fractalclockwork/core-memory-redux/kicad/_preview/pcb_ccs_sense-1.png

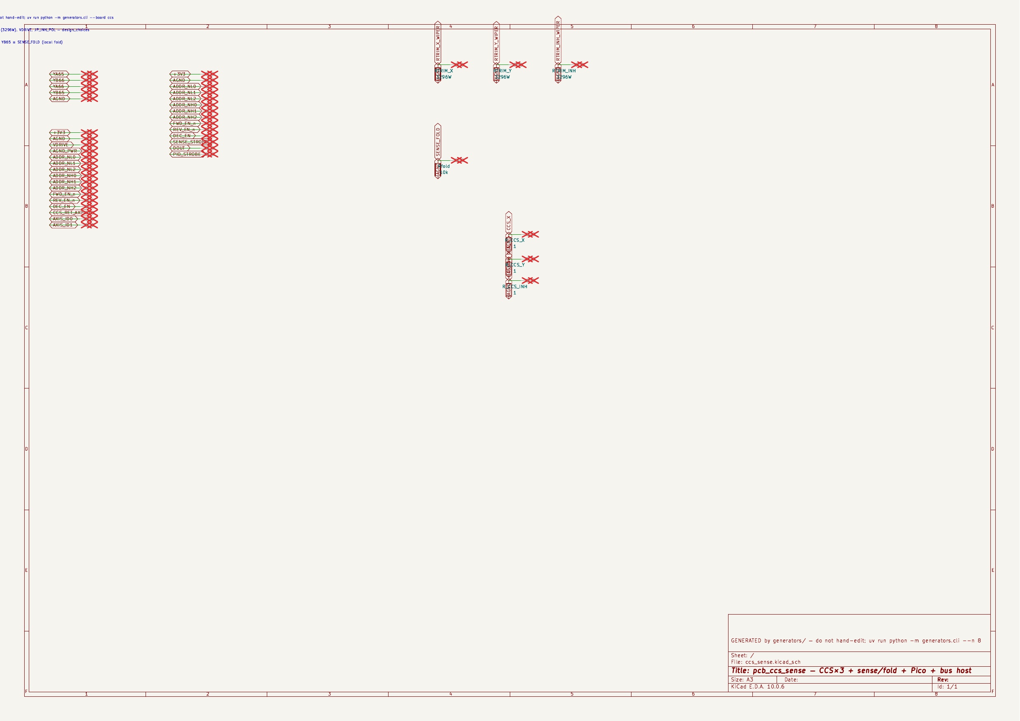
kicad/_preview/pcb_ccs_sense-1.png
