fractalclockwork/core-memory-redux/kicad/bringup_2x2/ccs_channel.kicad_sch

## KiCad design kicad/bringup_2x2/ccs_channel.kicad_sch (2026-10-05)

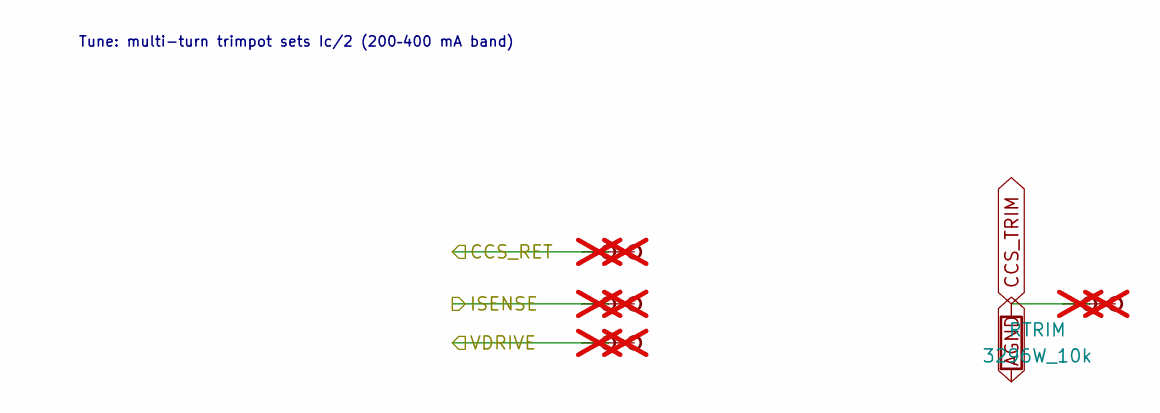
[picture p16: schematic ccs_channel.kicad_sch]

Parts:
RTRIM: 3296W_10k
TP_CCS_RET: Stub; not fitted
TP_CCS_RETb: Stub; not fitted
TP_CCS_TRIM_80_01_35_, TP_CCS_TRIM_80_01_35_b: Stub; not fitted
TP_ISENSE: Stub; not fitted
TP_ISENSEb: Stub; not fitted
TP_VDRIVE: Stub; not fitted
TP_VDRIVEb: Stub; not fitted

Connections:
AGND: RTRIM.2
CCS_RET: TP_CCS_RET.1, TP_CCS_RETb.1
CCS_TRIM: RTRIM.1, TP_CCS_TRIM_80_01_35_.1, TP_CCS_TRIM_80_01_35_b.1
ISENSE: TP_ISENSE.1, TP_ISENSEb.1
VDRIVE: TP_VDRIVE.1, TP_VDRIVEb.1

Notes on the sheet:
Tune: multi-turn trimpot sets Ic/2 (200–400 mA band)
