fractalclockwork/core-memory-redux/kicad/bringup_2x2/decode_block.kicad_sch

## KiCad design kicad/bringup_2x2/decode_block.kicad_sch (2026-10-05)

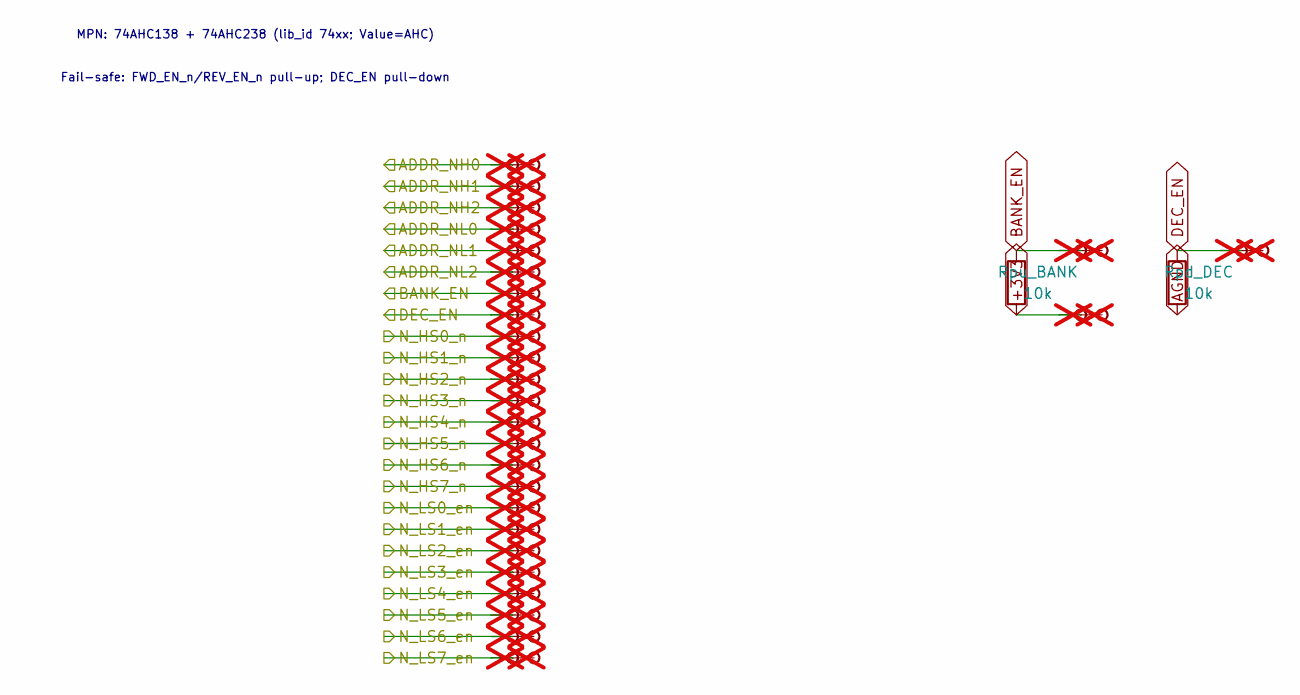
[picture p17: schematic decode_block.kicad_sch]

Parts:
Rpd_DEC: 10k
Rpu_BANK: 10k
TP_ADDR_NH0, TP_ADDR_NH0b, TP_ADDR_NH1, TP_ADDR_NH1b, TP_ADDR_NH2, TP_ADDR_NH2b: Stub; not fitted
TP_ADDR_NL0, TP_ADDR_NL0b, TP_ADDR_NL1, TP_ADDR_NL1b, TP_ADDR_NL2, TP_ADDR_NL2b: Stub; not fitted
TP_BANK_EN: Stub; not fitted
TP_BANK_EN_100_33_35_, TP_BANK_EN_100_33_35_b: Stub; not fitted
TP_BANK_ENb: Stub; not fitted
TP_DEC_EN: Stub; not fitted
TP_DEC_EN_119_38_35_5, TP_DEC_EN_119_38_35_5b: Stub; not fitted
TP_DEC_ENb: Stub; not fitted
TP_N_HS0_n, TP_N_HS0_nb, TP_N_HS1_n, TP_N_HS1_nb, TP_N_HS2_n, TP_N_HS2_nb, TP_N_HS3_n, TP_N_HS3_nb, TP_N_HS4_n, TP_N_HS4_nb, TP_N_HS5_n, TP_N_HS5_nb, TP_N_HS6_n, TP_N_HS6_nb, TP_N_HS7_n, TP_N_HS7_nb: Stub; not fitted
TP_N_LS0_en, TP_N_LS0_enb, TP_N_LS1_en, TP_N_LS1_enb, TP_N_LS2_en, TP_N_LS2_enb, TP_N_LS3_en, TP_N_LS3_enb, TP_N_LS4_en, TP_N_LS4_enb, TP_N_LS5_en, TP_N_LS5_enb, TP_N_LS6_en, TP_N_LS6_enb, TP_N_LS7_en, TP_N_LS7_enb: Stub; not fitted
TP__3V3_100_33_43_18, TP__3V3_100_33_43_18b: Stub; not fitted

Connections:
+3V3: Rpu_BANK.2, TP__3V3_100_33_43_18.1, TP__3V3_100_33_43_18b.1
ADDR_NH0: TP_ADDR_NH0.1, TP_ADDR_NH0b.1
ADDR_NH1: TP_ADDR_NH1.1, TP_ADDR_NH1b.1
ADDR_NH2: TP_ADDR_NH2.1, TP_ADDR_NH2b.1
ADDR_NL0: TP_ADDR_NL0.1, TP_ADDR_NL0b.1
ADDR_NL1: TP_ADDR_NL1.1, TP_ADDR_NL1b.1
ADDR_NL2: TP_ADDR_NL2.1, TP_ADDR_NL2b.1
AGND: Rpd_DEC.2
BANK_EN: Rpu_BANK.1, TP_BANK_EN.1, TP_BANK_EN_100_33_35_.1, TP_BANK_EN_100_33_35_b.1, TP_BANK_ENb.1
DEC_EN: Rpd_DEC.1, TP_DEC_EN.1, TP_DEC_EN_119_38_35_5.1, TP_DEC_EN_119_38_35_5b.1, TP_DEC_ENb.1
N_HS0_n: TP_N_HS0_n.1, TP_N_HS0_nb.1
N_HS1_n: TP_N_HS1_n.1, TP_N_HS1_nb.1
N_HS2_n: TP_N_HS2_n.1, TP_N_HS2_nb.1
N_HS3_n: TP_N_HS3_n.1, TP_N_HS3_nb.1
N_HS4_n: TP_N_HS4_n.1, TP_N_HS4_nb.1
N_HS5_n: TP_N_HS5_n.1, TP_N_HS5_nb.1
N_HS6_n: TP_N_HS6_n.1, TP_N_HS6_nb.1
N_HS7_n: TP_N_HS7_n.1, TP_N_HS7_nb.1
N_LS0_en: TP_N_LS0_en.1, TP_N_LS0_enb.1
N_LS1_en: TP_N_LS1_en.1, TP_N_LS1_enb.1
N_LS2_en: TP_N_LS2_en.1, TP_N_LS2_enb.1
N_LS3_en: TP_N_LS3_en.1, TP_N_LS3_enb.1
N_LS4_en: TP_N_LS4_en.1, TP_N_LS4_enb.1
N_LS5_en: TP_N_LS5_en.1, TP_N_LS5_enb.1
N_LS6_en: TP_N_LS6_en.1, TP_N_LS6_enb.1
N_LS7_en: TP_N_LS7_en.1, TP_N_LS7_enb.1

Notes on the sheet:
MPN: 74AHC138 + 74AHC238 (lib_id 74xx; Value=AHC)
Fail-safe: FWD_EN_n/REV_EN_n pull-up; DEC_EN pull-down
