fractalclockwork/core-memory-redux/kicad/bringup_2x2/dmos_hs_array.kicad_sch

## KiCad design kicad/bringup_2x2/dmos_hs_array.kicad_sch (2026-10-05)

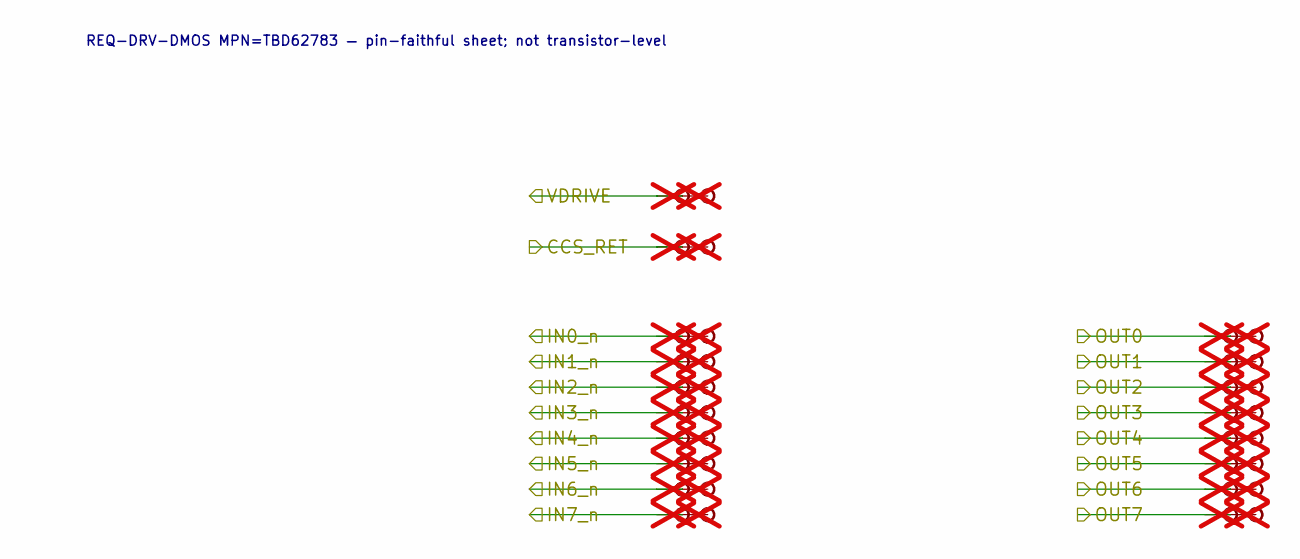
[picture p18: schematic dmos_hs_array.kicad_sch]

Parts:
TP_CCS_RET: Stub; not fitted
TP_CCS_RETb: Stub; not fitted
TP_IN0_n, TP_IN0_nb, TP_IN1_n, TP_IN1_nb, TP_IN2_n, TP_IN2_nb, TP_IN3_n, TP_IN3_nb, TP_IN4_n, TP_IN4_nb, TP_IN5_n, TP_IN5_nb, TP_IN6_n, TP_IN6_nb, TP_IN7_n, TP_IN7_nb: Stub; not fitted
TP_OUT0, TP_OUT0b, TP_OUT1, TP_OUT1b, TP_OUT2, TP_OUT2b, TP_OUT3, TP_OUT3b, TP_OUT4, TP_OUT4b, TP_OUT5, TP_OUT5b, TP_OUT6, TP_OUT6b, TP_OUT7, TP_OUT7b: Stub; not fitted
TP_VDRIVE: Stub; not fitted
TP_VDRIVEb: Stub; not fitted

Connections:
CCS_RET: TP_CCS_RET.1, TP_CCS_RETb.1
IN0_n: TP_IN0_n.1, TP_IN0_nb.1
IN1_n: TP_IN1_n.1, TP_IN1_nb.1
IN2_n: TP_IN2_n.1, TP_IN2_nb.1
IN3_n: TP_IN3_n.1, TP_IN3_nb.1
IN4_n: TP_IN4_n.1, TP_IN4_nb.1
IN5_n: TP_IN5_n.1, TP_IN5_nb.1
IN6_n: TP_IN6_n.1, TP_IN6_nb.1
IN7_n: TP_IN7_n.1, TP_IN7_nb.1
OUT0: TP_OUT0.1, TP_OUT0b.1
OUT1: TP_OUT1.1, TP_OUT1b.1
OUT2: TP_OUT2.1, TP_OUT2b.1
OUT3: TP_OUT3.1, TP_OUT3b.1
OUT4: TP_OUT4.1, TP_OUT4b.1
OUT5: TP_OUT5.1, TP_OUT5b.1
OUT6: TP_OUT6.1, TP_OUT6b.1
OUT7: TP_OUT7.1, TP_OUT7b.1
VDRIVE: TP_VDRIVE.1, TP_VDRIVEb.1

Notes on the sheet:
REQ-DRV-DMOS MPN=TBD62783 — pin-faithful sheet; not transistor-level
