fractalclockwork/core-memory-redux/kicad/bringup_2x2/dmos_ls_array.kicad_sch

## KiCad design kicad/bringup_2x2/dmos_ls_array.kicad_sch (2026-10-05)

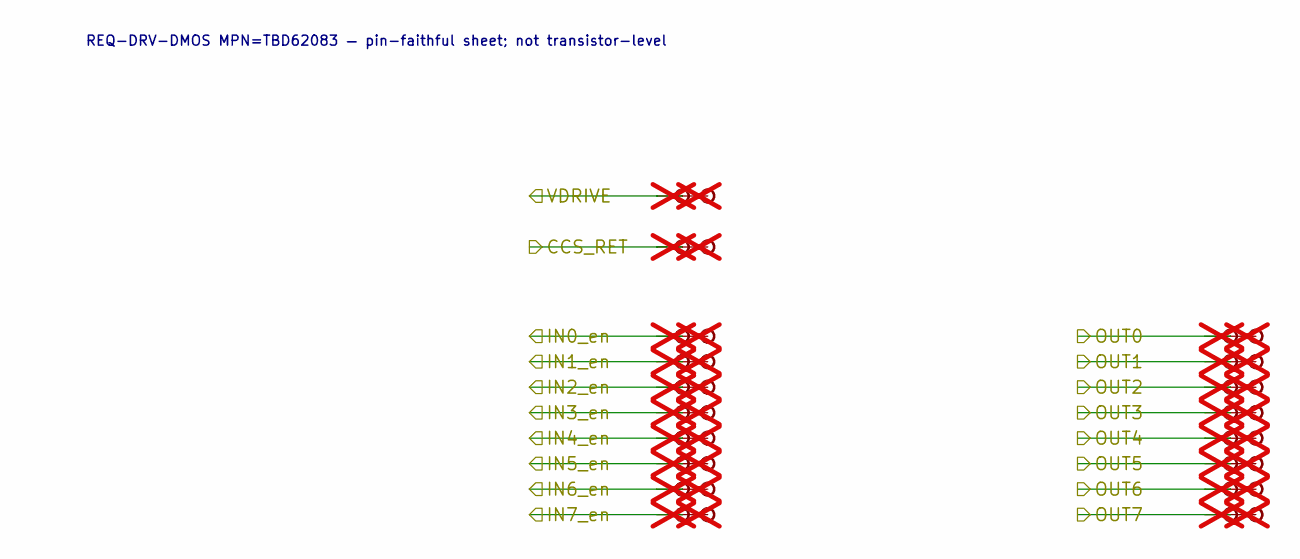
[picture p19: schematic dmos_ls_array.kicad_sch]

Parts:
TP_CCS_RET: Stub; not fitted
TP_CCS_RETb: Stub; not fitted
TP_IN0_en, TP_IN0_enb, TP_IN1_en, TP_IN1_enb, TP_IN2_en, TP_IN2_enb, TP_IN3_en, TP_IN3_enb, TP_IN4_en, TP_IN4_enb, TP_IN5_en, TP_IN5_enb, TP_IN6_en, TP_IN6_enb, TP_IN7_en, TP_IN7_enb: Stub; not fitted
TP_OUT0, TP_OUT0b, TP_OUT1, TP_OUT1b, TP_OUT2, TP_OUT2b, TP_OUT3, TP_OUT3b, TP_OUT4, TP_OUT4b, TP_OUT5, TP_OUT5b, TP_OUT6, TP_OUT6b, TP_OUT7, TP_OUT7b: Stub; not fitted
TP_VDRIVE: Stub; not fitted
TP_VDRIVEb: Stub; not fitted

Connections:
CCS_RET: TP_CCS_RET.1, TP_CCS_RETb.1
IN0_en: TP_IN0_en.1, TP_IN0_enb.1
IN1_en: TP_IN1_en.1, TP_IN1_enb.1
IN2_en: TP_IN2_en.1, TP_IN2_enb.1
IN3_en: TP_IN3_en.1, TP_IN3_enb.1
IN4_en: TP_IN4_en.1, TP_IN4_enb.1
IN5_en: TP_IN5_en.1, TP_IN5_enb.1
IN6_en: TP_IN6_en.1, TP_IN6_enb.1
IN7_en: TP_IN7_en.1, TP_IN7_enb.1
OUT0: TP_OUT0.1, TP_OUT0b.1
OUT1: TP_OUT1.1, TP_OUT1b.1
OUT2: TP_OUT2.1, TP_OUT2b.1
OUT3: TP_OUT3.1, TP_OUT3b.1
OUT4: TP_OUT4.1, TP_OUT4b.1
OUT5: TP_OUT5.1, TP_OUT5b.1
OUT6: TP_OUT6.1, TP_OUT6b.1
OUT7: TP_OUT7.1, TP_OUT7b.1
VDRIVE: TP_VDRIVE.1, TP_VDRIVEb.1

Notes on the sheet:
REQ-DRV-DMOS MPN=TBD62083 — pin-faithful sheet; not transistor-level
