fractalclockwork/core-memory-redux/kicad/bringup_2x2/driver.kicad_sch

## KiCad design kicad/bringup_2x2/driver.kicad_sch (2026-10-05)

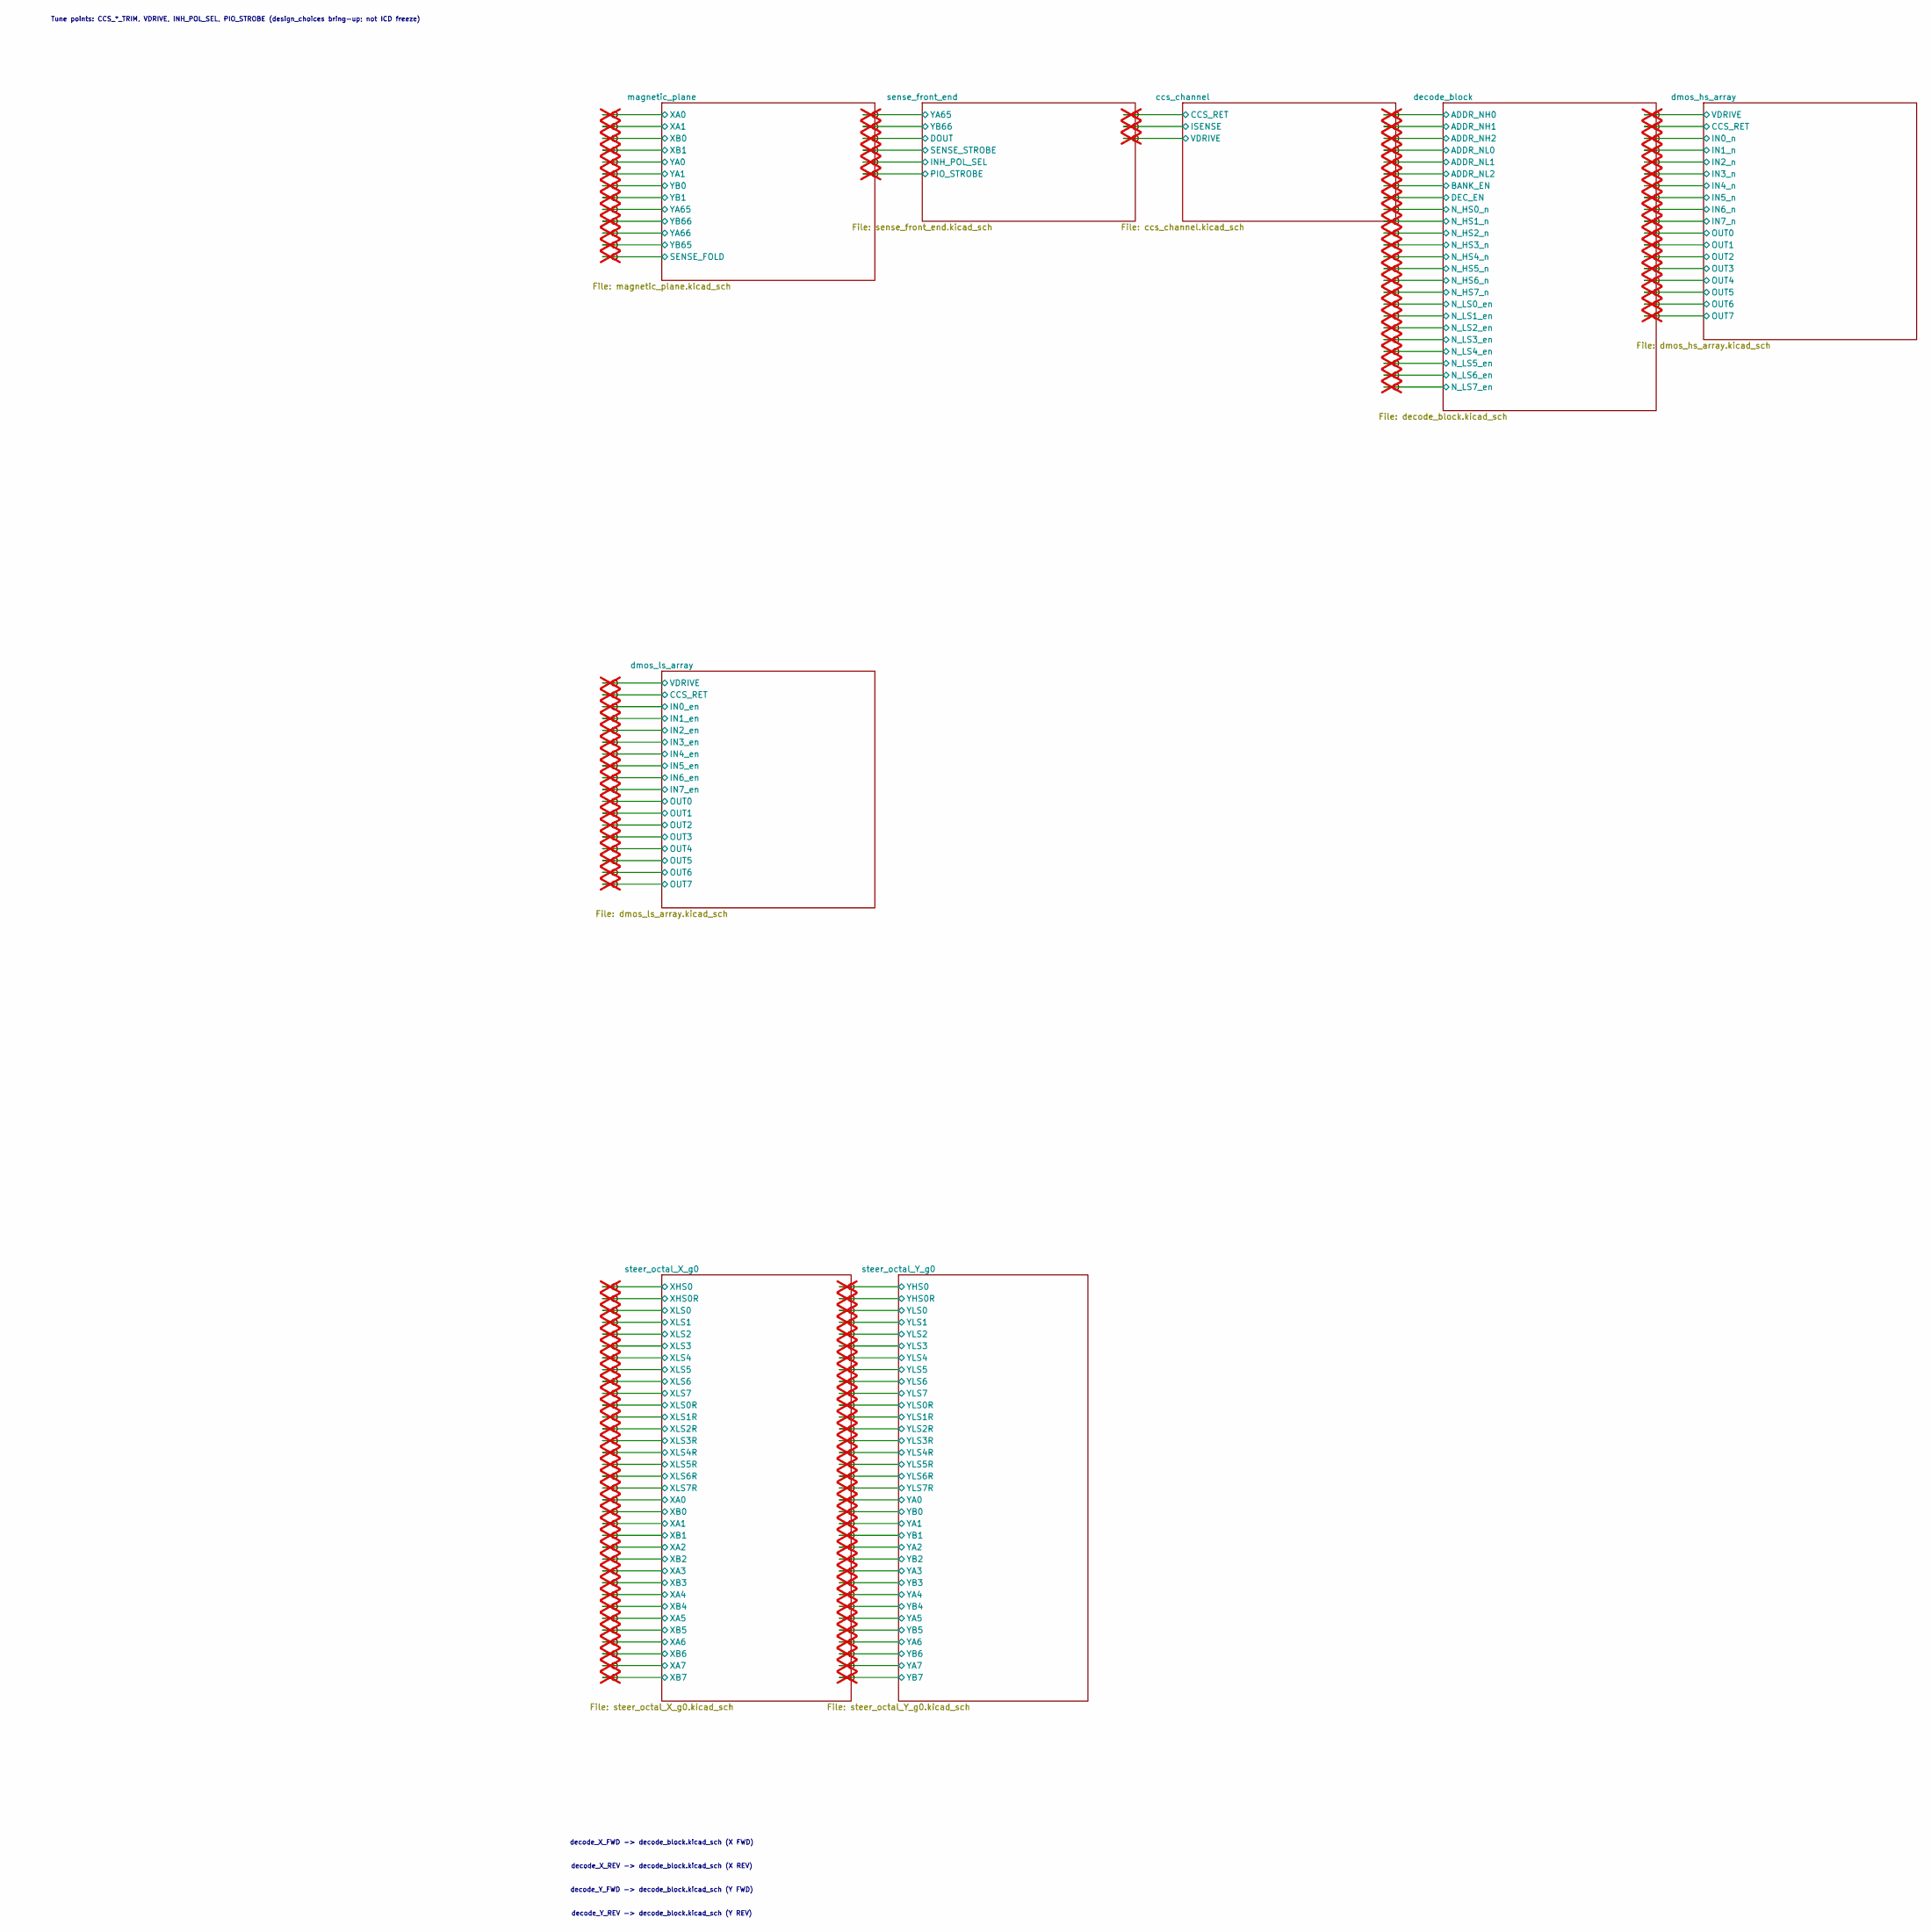
[picture p20: schematic driver.kicad_sch]

Parts:
TP_ccs_channel_CCS_RET: Stub; not fitted
TP_ccs_channel_ISENSE: Stub; not fitted
TP_ccs_channel_VDRIVE: Stub; not fitted
TP_decode_block_ADDR_NH: Stub; not fitted
TP_decode_block_ADDR_NL: Stub; not fitted
TP_decode_block_BANK_EN: Stub; not fitted
TP_decode_block_DEC_EN: Stub; not fitted
TP_decode_block_N_HS0_n, TP_decode_block_N_HS1_n, TP_decode_block_N_HS2_n, TP_decode_block_N_HS3_n, TP_decode_block_N_HS4_n, TP_decode_block_N_HS5_n, TP_decode_block_N_HS6_n, TP_decode_block_N_HS7_n: Stub; not fitted
TP_decode_block_N_LS0_e, TP_decode_block_N_LS1_e, TP_decode_block_N_LS2_e, TP_decode_block_N_LS3_e, TP_decode_block_N_LS4_e, TP_decode_block_N_LS5_e, TP_decode_block_N_LS6_e, TP_decode_block_N_LS7_e: Stub; not fitted
TP_dmos_hs_array_CCS_RE: Stub; not fitted
TP_dmos_hs_array_IN0_n, TP_dmos_hs_array_IN1_n, TP_dmos_hs_array_IN2_n, TP_dmos_hs_array_IN3_n, TP_dmos_hs_array_IN4_n, TP_dmos_hs_array_IN5_n, TP_dmos_hs_array_IN6_n, TP_dmos_hs_array_IN7_n: Stub; not fitted
TP_dmos_hs_array_OUT0, TP_dmos_hs_array_OUT1, TP_dmos_hs_array_OUT2, TP_dmos_hs_array_OUT3, TP_dmos_hs_array_OUT4, TP_dmos_hs_array_OUT5, TP_dmos_hs_array_OUT6, TP_dmos_hs_array_OUT7: Stub; not fitted
TP_dmos_hs_array_VDRIVE: Stub; not fitted
TP_dmos_ls_array_CCS_RE: Stub; not fitted
TP_dmos_ls_array_IN0_en, TP_dmos_ls_array_IN1_en, TP_dmos_ls_array_IN2_en, TP_dmos_ls_array_IN3_en, TP_dmos_ls_array_IN4_en, TP_dmos_ls_array_IN5_en, TP_dmos_ls_array_IN6_en, TP_dmos_ls_array_IN7_en: Stub; not fitted
TP_dmos_ls_array_OUT0, TP_dmos_ls_array_OUT1, TP_dmos_ls_array_OUT2, TP_dmos_ls_array_OUT3, TP_dmos_ls_array_OUT4, TP_dmos_ls_array_OUT5, TP_dmos_ls_array_OUT6, TP_dmos_ls_array_OUT7: Stub; not fitted
TP_dmos_ls_array_VDRIVE: Stub; not fitted
TP_magnetic_plane_SENSE: Stub; not fitted
TP_magnetic_plane_XA0, TP_magnetic_plane_XA1: Stub; not fitted
TP_magnetic_plane_XB0, TP_magnetic_plane_XB1: Stub; not fitted
TP_magnetic_plane_YA0, TP_magnetic_plane_YA1, TP_magnetic_plane_YA65, TP_magnetic_plane_YA66: Stub; not fitted
TP_magnetic_plane_YB0, TP_magnetic_plane_YB1, TP_magnetic_plane_YB65, TP_magnetic_plane_YB66: Stub; not fitted
TP_sense_front_end_DOUT: Stub; not fitted
TP_sense_front_end_INH_: Stub; not fitted
TP_sense_front_end_PIO_: Stub; not fitted
TP_sense_front_end_SENS: Stub; not fitted
TP_sense_front_end_YA65: Stub; not fitted
TP_sense_front_end_YB66: Stub; not fitted
TP_steer_octal_X_g0_XA0, TP_steer_octal_X_g0_XA1, TP_steer_octal_X_g0_XA2, TP_steer_octal_X_g0_XA3, TP_steer_octal_X_g0_XA4, TP_steer_octal_X_g0_XA5, TP_steer_octal_X_g0_XA6, TP_steer_octal_X_g0_XA7, TP_steer_octal_X_g0_XB0, TP_steer_octal_X_g0_XB1, TP_steer_octal_X_g0_XB2, TP_steer_octal_X_g0_XB3, TP_steer_octal_X_g0_XB4, TP_steer_octal_X_g0_XB5, TP_steer_octal_X_g0_XB6, TP_steer_octal_X_g0_XB7, TP_steer_octal_X_g0_XHS, TP_steer_octal_X_g0_XLS: Stub; not fitted
TP_steer_octal_Y_g0_YA0, TP_steer_octal_Y_g0_YA1, TP_steer_octal_Y_g0_YA2, TP_steer_octal_Y_g0_YA3, TP_steer_octal_Y_g0_YA4, TP_steer_octal_Y_g0_YA5, TP_steer_octal_Y_g0_YA6, TP_steer_octal_Y_g0_YA7, TP_steer_octal_Y_g0_YB0, TP_steer_octal_Y_g0_YB1, TP_steer_octal_Y_g0_YB2, TP_steer_octal_Y_g0_YB3, TP_steer_octal_Y_g0_YB4, TP_steer_octal_Y_g0_YB5, TP_steer_octal_Y_g0_YB6, TP_steer_octal_Y_g0_YB7, TP_steer_octal_Y_g0_YHS, TP_steer_octal_Y_g0_YLS: Stub; not fitted

Connections:
ADDR_NH0: TP_decode_block_ADDR_NH.1
ADDR_NH1: TP_decode_block_ADDR_NH.1
ADDR_NH2: TP_decode_block_ADDR_NH.1
ADDR_NL0: TP_decode_block_ADDR_NL.1
ADDR_NL1: TP_decode_block_ADDR_NL.1
ADDR_NL2: TP_decode_block_ADDR_NL.1
BANK_EN: TP_decode_block_BANK_EN.1
CCS_RET: TP_ccs_channel_CCS_RET.1, TP_dmos_hs_array_CCS_RE.1, TP_dmos_ls_array_CCS_RE.1
DEC_EN: TP_decode_block_DEC_EN.1
DOUT: TP_sense_front_end_DOUT.1
IN0_en: TP_dmos_ls_array_IN0_en.1
IN0_n: TP_dmos_hs_array_IN0_n.1
IN1_en: TP_dmos_ls_array_IN1_en.1
IN1_n: TP_dmos_hs_array_IN1_n.1
IN2_en: TP_dmos_ls_array_IN2_en.1
IN2_n: TP_dmos_hs_array_IN2_n.1
IN3_en: TP_dmos_ls_array_IN3_en.1
IN3_n: TP_dmos_hs_array_IN3_n.1
IN4_en: TP_dmos_ls_array_IN4_en.1
IN4_n: TP_dmos_hs_array_IN4_n.1
IN5_en: TP_dmos_ls_array_IN5_en.1
IN5_n: TP_dmos_hs_array_IN5_n.1
IN6_en: TP_dmos_ls_array_IN6_en.1
IN6_n: TP_dmos_hs_array_IN6_n.1
IN7_en: TP_dmos_ls_array_IN7_en.1
IN7_n: TP_dmos_hs_array_IN7_n.1
INH_POL_SEL: TP_sense_front_end_INH_.1
ISENSE: TP_ccs_channel_ISENSE.1
N_HS0_n: TP_decode_block_N_HS0_n.1
N_HS1_n: TP_decode_block_N_HS1_n.1
N_HS2_n: TP_decode_block_N_HS2_n.1
N_HS3_n: TP_decode_block_N_HS3_n.1
N_HS4_n: TP_decode_block_N_HS4_n.1
N_HS5_n: TP_decode_block_N_HS5_n.1
N_HS6_n: TP_decode_block_N_HS6_n.1
N_HS7_n: TP_decode_block_N_HS7_n.1
N_LS0_en: TP_decode_block_N_LS0_e.1
N_LS1_en: TP_decode_block_N_LS1_e.1
N_LS2_en: TP_decode_block_N_LS2_e.1
N_LS3_en: TP_decode_block_N_LS3_e.1
N_LS4_en: TP_decode_block_N_LS4_e.1
N_LS5_en: TP_decode_block_N_LS5_e.1
N_LS6_en: TP_decode_block_N_LS6_e.1
N_LS7_en: TP_decode_block_N_LS7_e.1
OUT0: TP_dmos_hs_array_OUT0.1, TP_dmos_ls_array_OUT0.1
OUT1: TP_dmos_hs_array_OUT1.1, TP_dmos_ls_array_OUT1.1
OUT2: TP_dmos_hs_array_OUT2.1, TP_dmos_ls_array_OUT2.1
OUT3: TP_dmos_hs_array_OUT3.1, TP_dmos_ls_array_OUT3.1
OUT4: TP_dmos_hs_array_OUT4.1, TP_dmos_ls_array_OUT4.1
OUT5: TP_dmos_hs_array_OUT5.1, TP_dmos_ls_array_OUT5.1
OUT6: TP_dmos_hs_array_OUT6.1, TP_dmos_ls_array_OUT6.1
OUT7: TP_dmos_hs_array_OUT7.1, TP_dmos_ls_array_OUT7.1
PIO_STROBE: TP_sense_front_end_PIO_.1
SENSE_FOLD: TP_magnetic_plane_SENSE.1
SENSE_STROBE: TP_sense_front_end_SENS.1
VDRIVE: TP_ccs_channel_VDRIVE.1, TP_dmos_hs_array_VDRIVE.1, TP_dmos_ls_array_VDRIVE.1
XA0: TP_magnetic_plane_XA0.1, TP_steer_octal_X_g0_XA0.1
XA1: TP_magnetic_plane_XA1.1, TP_steer_octal_X_g0_XA1.1
XA2: TP_steer_octal_X_g0_XA2.1
XA3: TP_steer_octal_X_g0_XA3.1
XA4: TP_steer_octal_X_g0_XA4.1
XA5: TP_steer_octal_X_g0_XA5.1
XA6: TP_steer_octal_X_g0_XA6.1
XA7: TP_steer_octal_X_g0_XA7.1
XB0: TP_magnetic_plane_XB0.1, TP_steer_octal_X_g0_XB0.1
XB1: TP_magnetic_plane_XB1.1, TP_steer_octal_X_g0_XB1.1
XB2: TP_steer_octal_X_g0_XB2.1
XB3: TP_steer_octal_X_g0_XB3.1
XB4: TP_steer_octal_X_g0_XB4.1
XB5: TP_steer_octal_X_g0_XB5.1
XB6: TP_steer_octal_X_g0_XB6.1
XB7: TP_steer_octal_X_g0_XB7.1
XHS0: TP_steer_octal_X_g0_XHS.1
XHS0R: TP_steer_octal_X_g0_XHS.1
XLS0: TP_steer_octal_X_g0_XLS.1
XLS0R: TP_steer_octal_X_g0_XLS.1
XLS1: TP_steer_octal_X_g0_XLS.1
XLS1R: TP_steer_octal_X_g0_XLS.1
XLS2: TP_steer_octal_X_g0_XLS.1
XLS2R: TP_steer_octal_X_g0_XLS.1
XLS3: TP_steer_octal_X_g0_XLS.1
XLS3R: TP_steer_octal_X_g0_XLS.1
XLS4: TP_steer_octal_X_g0_XLS.1
XLS4R: TP_steer_octal_X_g0_XLS.1
XLS5: TP_steer_octal_X_g0_XLS.1
XLS5R: TP_steer_octal_X_g0_XLS.1
XLS6: TP_steer_octal_X_g0_XLS.1
XLS6R: TP_steer_octal_X_g0_XLS.1
XLS7: TP_steer_octal_X_g0_XLS.1
XLS7R: TP_steer_octal_X_g0_XLS.1
YA0: TP_magnetic_plane_YA0.1, TP_steer_octal_Y_g0_YA0.1
YA1: TP_magnetic_plane_YA1.1, TP_steer_octal_Y_g0_YA1.1
YA2: TP_steer_octal_Y_g0_YA2.1
YA3: TP_steer_octal_Y_g0_YA3.1
YA4: TP_steer_octal_Y_g0_YA4.1
YA5: TP_steer_octal_Y_g0_YA5.1
YA6: TP_steer_octal_Y_g0_YA6.1
YA7: TP_steer_octal_Y_g0_YA7.1
YA65: TP_magnetic_plane_YA65.1, TP_sense_front_end_YA65.1
YA66: TP_magnetic_plane_YA66.1
YB0: TP_magnetic_plane_YB0.1, TP_steer_octal_Y_g0_YB0.1
YB1: TP_magnetic_plane_YB1.1, TP_steer_octal_Y_g0_YB1.1
YB2: TP_steer_octal_Y_g0_YB2.1
YB3: TP_steer_octal_Y_g0_YB3.1
YB4: TP_steer_octal_Y_g0_YB4.1
YB5: TP_steer_octal_Y_g0_YB5.1
YB6: TP_steer_octal_Y_g0_YB6.1
YB7: TP_steer_octal_Y_g0_YB7.1
YB65: TP_magnetic_plane_YB65.1
YB66: TP_magnetic_plane_YB66.1, TP_sense_front_end_YB66.1
YHS0: TP_steer_octal_Y_g0_YHS.1
YHS0R: TP_steer_octal_Y_g0_YHS.1
YLS0: TP_steer_octal_Y_g0_YLS.1
YLS0R: TP_steer_octal_Y_g0_YLS.1
YLS1: TP_steer_octal_Y_g0_YLS.1
YLS1R: TP_steer_octal_Y_g0_YLS.1
YLS2: TP_steer_octal_Y_g0_YLS.1
YLS2R: TP_steer_octal_Y_g0_YLS.1
YLS3: TP_steer_octal_Y_g0_YLS.1
YLS3R: TP_steer_octal_Y_g0_YLS.1
YLS4: TP_steer_octal_Y_g0_YLS.1
YLS4R: TP_steer_octal_Y_g0_YLS.1
YLS5: TP_steer_octal_Y_g0_YLS.1
YLS5R: TP_steer_octal_Y_g0_YLS.1
YLS6: TP_steer_octal_Y_g0_YLS.1
YLS6R: TP_steer_octal_Y_g0_YLS.1
YLS7: TP_steer_octal_Y_g0_YLS.1
YLS7R: TP_steer_octal_Y_g0_YLS.1

Notes on the sheet:
decode_X_FWD -> decode_block.kicad_sch (X FWD)
decode_Y_FWD -> decode_block.kicad_sch (Y FWD)
Tune points: CCS_*_TRIM, VDRIVE, INH_POL_SEL, PIO_STROBE (design_choices bring-up; not ICD freeze)
decode_X_REV -> decode_block.kicad_sch (X REV)
decode_Y_REV -> decode_block.kicad_sch (Y REV)
