fractalclockwork/core-memory-redux/kicad/bringup_2x2/magnetic_plane.kicad_sch

## KiCad design kicad/bringup_2x2/magnetic_plane.kicad_sch (2026-10-05)

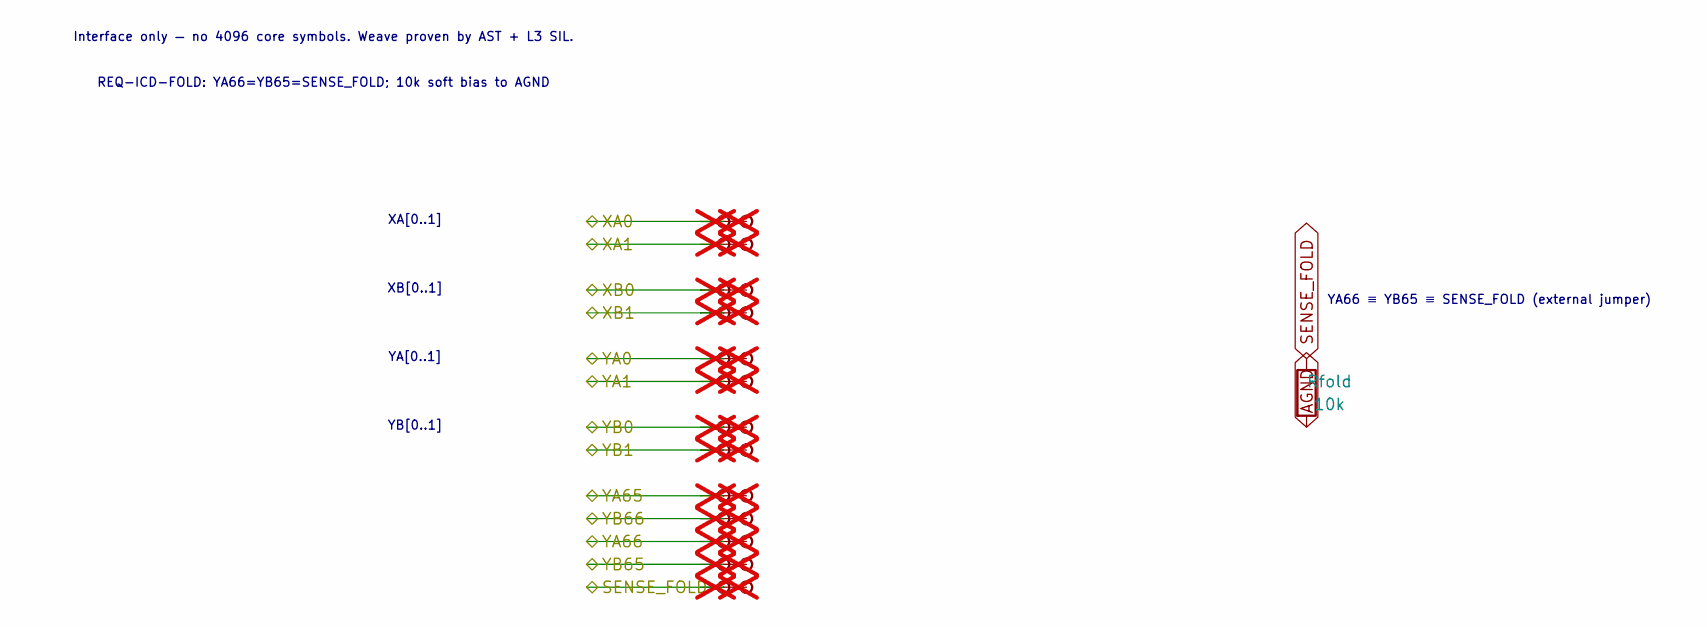
[picture p21: schematic magnetic_plane.kicad_sch]

Parts:
Rfold: 10k
TP_SENSE_FOLD: Stub; not fitted
TP_SENSE_FOLDb: Stub; not fitted
TP_XA0, TP_XA0b, TP_XA1, TP_XA1b: Stub; not fitted
TP_XB0, TP_XB0b, TP_XB1, TP_XB1b: Stub; not fitted
TP_YA0, TP_YA0b, TP_YA1, TP_YA1b, TP_YA65, TP_YA65b, TP_YA66, TP_YA66b: Stub; not fitted
TP_YB0, TP_YB0b, TP_YB1, TP_YB1b, TP_YB65, TP_YB65b, TP_YB66, TP_YB66b: Stub; not fitted

Connections:
AGND: Rfold.2
SENSE_FOLD: Rfold.1, TP_SENSE_FOLD.1, TP_SENSE_FOLDb.1
XA0: TP_XA0.1, TP_XA0b.1
XA1: TP_XA1.1, TP_XA1b.1
XB0: TP_XB0.1, TP_XB0b.1
XB1: TP_XB1.1, TP_XB1b.1
YA0: TP_YA0.1, TP_YA0b.1
YA1: TP_YA1.1, TP_YA1b.1
YA65: TP_YA65.1, TP_YA65b.1
YA66: TP_YA66.1, TP_YA66b.1
YB0: TP_YB0.1, TP_YB0b.1
YB1: TP_YB1.1, TP_YB1b.1
YB65: TP_YB65.1, TP_YB65b.1
YB66: TP_YB66.1, TP_YB66b.1

Notes on the sheet:
Interface only — no 4096 core symbols. Weave proven by AST + L3 SIL.
REQ-ICD-FOLD: YA66=YB65=SENSE_FOLD; 10k soft bias to AGND
XA[0..1]
XB[0..1]
YA[0..1]
YB[0..1]
YA66 ≡ YB65 ≡ SENSE_FOLD (external jumper)
