fractalclockwork/core-memory-redux/kicad/bringup_2x2/sense_front_end.kicad_sch

## KiCad design kicad/bringup_2x2/sense_front_end.kicad_sch (2026-10-05)

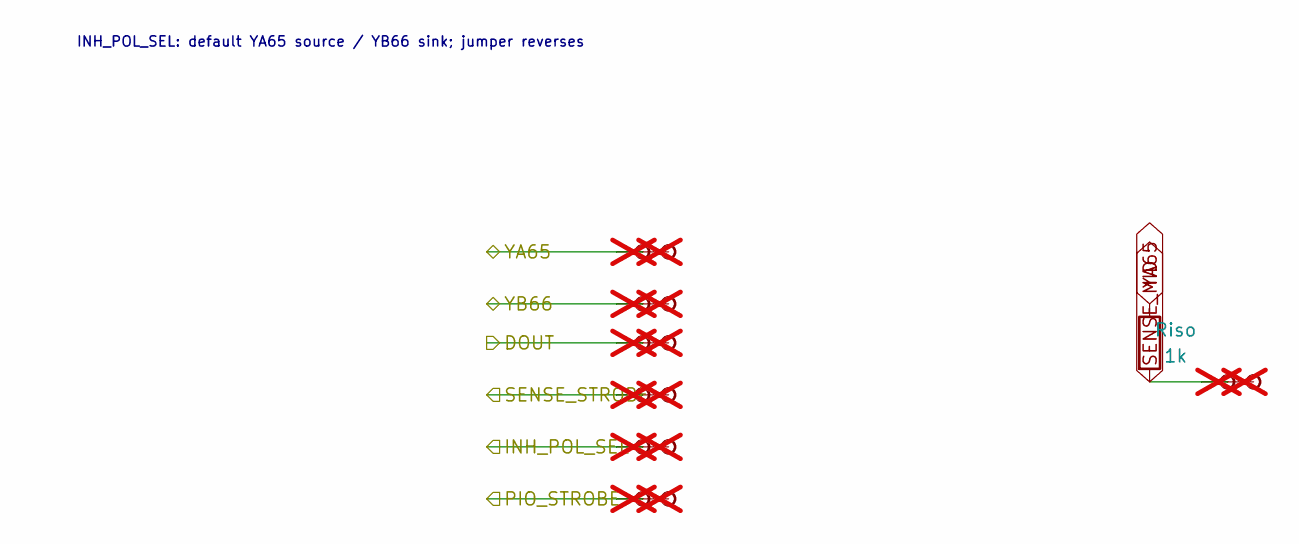
[picture p22: schematic sense_front_end.kicad_sch]

Parts:
Riso: 1k
TP_DOUT: Stub; not fitted
TP_DOUTb: Stub; not fitted
TP_INH_POL_SEL: Stub; not fitted
TP_INH_POL_SELb: Stub; not fitted
TP_PIO_STROBE: Stub; not fitted
TP_PIO_STROBEb: Stub; not fitted
TP_SENSE_MID_90_17_43, TP_SENSE_MID_90_17_43b: Stub; not fitted
TP_SENSE_STROBE: Stub; not fitted
TP_SENSE_STROBEb: Stub; not fitted
TP_YA65, TP_YA65b: Stub; not fitted
TP_YB66, TP_YB66b: Stub; not fitted

Connections:
DOUT: TP_DOUT.1, TP_DOUTb.1
INH_POL_SEL: TP_INH_POL_SEL.1, TP_INH_POL_SELb.1
PIO_STROBE: TP_PIO_STROBE.1, TP_PIO_STROBEb.1
SENSE_MID: Riso.2, TP_SENSE_MID_90_17_43.1, TP_SENSE_MID_90_17_43b.1
SENSE_STROBE: TP_SENSE_STROBE.1, TP_SENSE_STROBEb.1
YA65: Riso.1, TP_YA65.1, TP_YA65b.1
YB66: TP_YB66.1, TP_YB66b.1

Notes on the sheet:
INH_POL_SEL: default YA65 source / YB66 sink; jumper reverses
