fractalclockwork/core-memory-redux/kicad/bringup_2x2/steer_octal_X_g0.kicad_sch

## KiCad design kicad/bringup_2x2/steer_octal_X_g0.kicad_sch (2026-10-05)

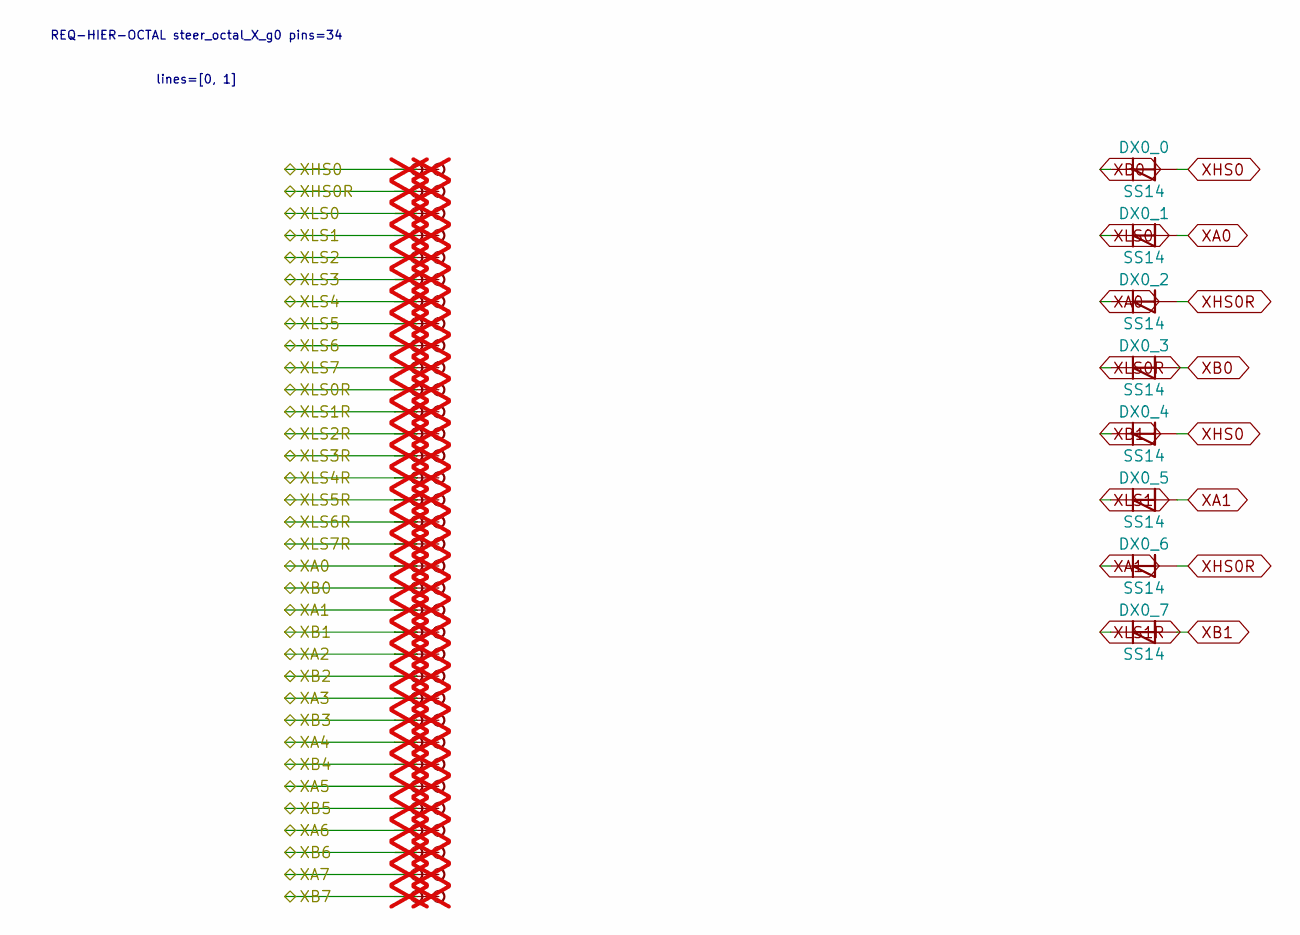
[picture p23: schematic steer_octal_X_g0.kicad_sch]

Parts:
DX0_0, DX0_1, DX0_2, DX0_3, DX0_4, DX0_5, DX0_6, DX0_7: SS14; D_SMA
TP_XA0, TP_XA0b, TP_XA1, TP_XA1b, TP_XA2, TP_XA2b, TP_XA3, TP_XA3b, TP_XA4, TP_XA4b, TP_XA5, TP_XA5b, TP_XA6, TP_XA6b, TP_XA7, TP_XA7b: Stub; not fitted
TP_XB0, TP_XB0b, TP_XB1, TP_XB1b, TP_XB2, TP_XB2b, TP_XB3, TP_XB3b, TP_XB4, TP_XB4b, TP_XB5, TP_XB5b, TP_XB6, TP_XB6b, TP_XB7, TP_XB7b: Stub; not fitted
TP_XHS0, TP_XHS0R, TP_XHS0Rb, TP_XHS0b: Stub; not fitted
TP_XLS0, TP_XLS0R, TP_XLS0Rb, TP_XLS0b, TP_XLS1, TP_XLS1R, TP_XLS1Rb, TP_XLS1b, TP_XLS2, TP_XLS2R, TP_XLS2Rb, TP_XLS2b, TP_XLS3, TP_XLS3R, TP_XLS3Rb, TP_XLS3b, TP_XLS4, TP_XLS4R, TP_XLS4Rb, TP_XLS4b, TP_XLS5, TP_XLS5R, TP_XLS5Rb, TP_XLS5b, TP_XLS6, TP_XLS6R, TP_XLS6Rb, TP_XLS6b, TP_XLS7, TP_XLS7R, TP_XLS7Rb, TP_XLS7b: Stub; not fitted

Connections:
XA0: DX0_1.2 (A), DX0_2.1 (K), TP_XA0.1, TP_XA0b.1
XA1: DX0_5.2 (A), DX0_6.1 (K), TP_XA1.1, TP_XA1b.1
XA2: TP_XA2.1, TP_XA2b.1
XA3: TP_XA3.1, TP_XA3b.1
XA4: TP_XA4.1, TP_XA4b.1
XA5: TP_XA5.1, TP_XA5b.1
XA6: TP_XA6.1, TP_XA6b.1
XA7: TP_XA7.1, TP_XA7b.1
XB0: DX0_0.1 (K), DX0_3.2 (A), TP_XB0.1, TP_XB0b.1
XB1: DX0_4.1 (K), DX0_7.2 (A), TP_XB1.1, TP_XB1b.1
XB2: TP_XB2.1, TP_XB2b.1
XB3: TP_XB3.1, TP_XB3b.1
XB4: TP_XB4.1, TP_XB4b.1
XB5: TP_XB5.1, TP_XB5b.1
XB6: TP_XB6.1, TP_XB6b.1
XB7: TP_XB7.1, TP_XB7b.1
XHS0: DX0_0.2 (A), DX0_4.2 (A), TP_XHS0.1, TP_XHS0b.1
XHS0R: DX0_2.2 (A), DX0_6.2 (A), TP_XHS0R.1, TP_XHS0Rb.1
XLS0: DX0_1.1 (K), TP_XLS0.1, TP_XLS0b.1
XLS0R: DX0_3.1 (K), TP_XLS0R.1, TP_XLS0Rb.1
XLS1: DX0_5.1 (K), TP_XLS1.1, TP_XLS1b.1
XLS1R: DX0_7.1 (K), TP_XLS1R.1, TP_XLS1Rb.1
XLS2: TP_XLS2.1, TP_XLS2b.1
XLS2R: TP_XLS2R.1, TP_XLS2Rb.1
XLS3: TP_XLS3.1, TP_XLS3b.1
XLS3R: TP_XLS3R.1, TP_XLS3Rb.1
XLS4: TP_XLS4.1, TP_XLS4b.1
XLS4R: TP_XLS4R.1, TP_XLS4Rb.1
XLS5: TP_XLS5.1, TP_XLS5b.1
XLS5R: TP_XLS5R.1, TP_XLS5Rb.1
XLS6: TP_XLS6.1, TP_XLS6b.1
XLS6R: TP_XLS6R.1, TP_XLS6Rb.1
XLS7: TP_XLS7.1, TP_XLS7b.1
XLS7R: TP_XLS7R.1, TP_XLS7Rb.1

Notes on the sheet:
REQ-HIER-OCTAL steer_octal_X_g0 pins=34
lines=[0, 1]
