fractalclockwork/core-memory-redux/kicad/bringup_2x2/steer_octal_Y_g0.kicad_sch

## KiCad design kicad/bringup_2x2/steer_octal_Y_g0.kicad_sch (2026-10-05)

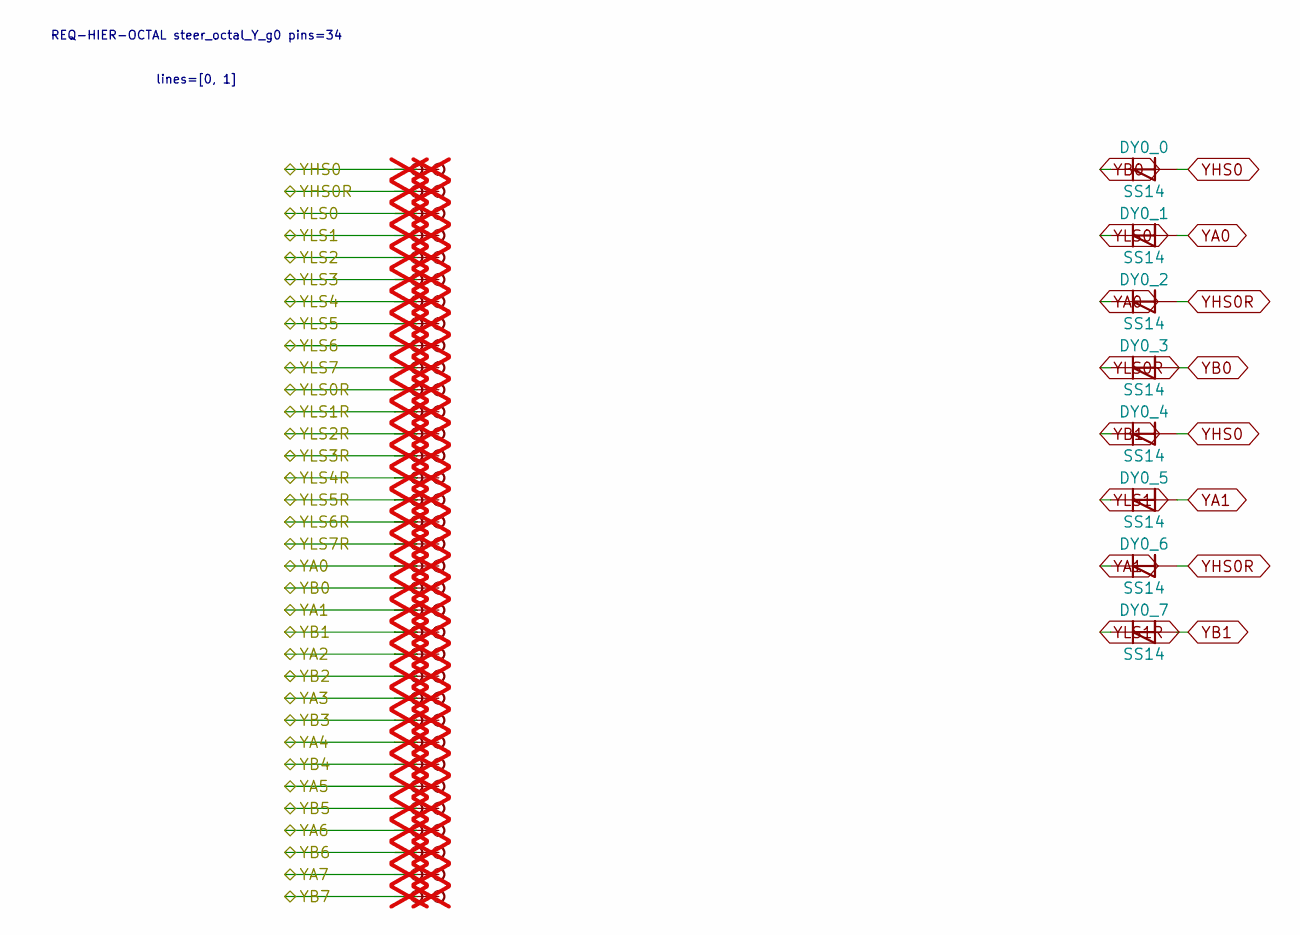
[picture p24: schematic steer_octal_Y_g0.kicad_sch]

Parts:
DY0_0, DY0_1, DY0_2, DY0_3, DY0_4, DY0_5, DY0_6, DY0_7: SS14; D_SMA
TP_YA0, TP_YA0b, TP_YA1, TP_YA1b, TP_YA2, TP_YA2b, TP_YA3, TP_YA3b, TP_YA4, TP_YA4b, TP_YA5, TP_YA5b, TP_YA6, TP_YA6b, TP_YA7, TP_YA7b: Stub; not fitted
TP_YB0, TP_YB0b, TP_YB1, TP_YB1b, TP_YB2, TP_YB2b, TP_YB3, TP_YB3b, TP_YB4, TP_YB4b, TP_YB5, TP_YB5b, TP_YB6, TP_YB6b, TP_YB7, TP_YB7b: Stub; not fitted
TP_YHS0, TP_YHS0R, TP_YHS0Rb, TP_YHS0b: Stub; not fitted
TP_YLS0, TP_YLS0R, TP_YLS0Rb, TP_YLS0b, TP_YLS1, TP_YLS1R, TP_YLS1Rb, TP_YLS1b, TP_YLS2, TP_YLS2R, TP_YLS2Rb, TP_YLS2b, TP_YLS3, TP_YLS3R, TP_YLS3Rb, TP_YLS3b, TP_YLS4, TP_YLS4R, TP_YLS4Rb, TP_YLS4b, TP_YLS5, TP_YLS5R, TP_YLS5Rb, TP_YLS5b, TP_YLS6, TP_YLS6R, TP_YLS6Rb, TP_YLS6b, TP_YLS7, TP_YLS7R, TP_YLS7Rb, TP_YLS7b: Stub; not fitted

Connections:
YA0: DY0_1.2 (A), DY0_2.1 (K), TP_YA0.1, TP_YA0b.1
YA1: DY0_5.2 (A), DY0_6.1 (K), TP_YA1.1, TP_YA1b.1
YA2: TP_YA2.1, TP_YA2b.1
YA3: TP_YA3.1, TP_YA3b.1
YA4: TP_YA4.1, TP_YA4b.1
YA5: TP_YA5.1, TP_YA5b.1
YA6: TP_YA6.1, TP_YA6b.1
YA7: TP_YA7.1, TP_YA7b.1
YB0: DY0_0.1 (K), DY0_3.2 (A), TP_YB0.1, TP_YB0b.1
YB1: DY0_4.1 (K), DY0_7.2 (A), TP_YB1.1, TP_YB1b.1
YB2: TP_YB2.1, TP_YB2b.1
YB3: TP_YB3.1, TP_YB3b.1
YB4: TP_YB4.1, TP_YB4b.1
YB5: TP_YB5.1, TP_YB5b.1
YB6: TP_YB6.1, TP_YB6b.1
YB7: TP_YB7.1, TP_YB7b.1
YHS0: DY0_0.2 (A), DY0_4.2 (A), TP_YHS0.1, TP_YHS0b.1
YHS0R: DY0_2.2 (A), DY0_6.2 (A), TP_YHS0R.1, TP_YHS0Rb.1
YLS0: DY0_1.1 (K), TP_YLS0.1, TP_YLS0b.1
YLS0R: DY0_3.1 (K), TP_YLS0R.1, TP_YLS0Rb.1
YLS1: DY0_5.1 (K), TP_YLS1.1, TP_YLS1b.1
YLS1R: DY0_7.1 (K), TP_YLS1R.1, TP_YLS1Rb.1
YLS2: TP_YLS2.1, TP_YLS2b.1
YLS2R: TP_YLS2R.1, TP_YLS2Rb.1
YLS3: TP_YLS3.1, TP_YLS3b.1
YLS3R: TP_YLS3R.1, TP_YLS3Rb.1
YLS4: TP_YLS4.1, TP_YLS4b.1
YLS4R: TP_YLS4R.1, TP_YLS4Rb.1
YLS5: TP_YLS5.1, TP_YLS5b.1
YLS5R: TP_YLS5R.1, TP_YLS5Rb.1
YLS6: TP_YLS6.1, TP_YLS6b.1
YLS6R: TP_YLS6R.1, TP_YLS6Rb.1
YLS7: TP_YLS7.1, TP_YLS7b.1
YLS7R: TP_YLS7R.1, TP_YLS7Rb.1

Notes on the sheet:
REQ-HIER-OCTAL steer_octal_Y_g0 pins=34
lines=[0, 1]
