fractalclockwork/core-memory-redux/kicad/driver_64x64/driver.kicad_sch

## KiCad design kicad/driver_64x64/driver.kicad_sch (2026-10-05)

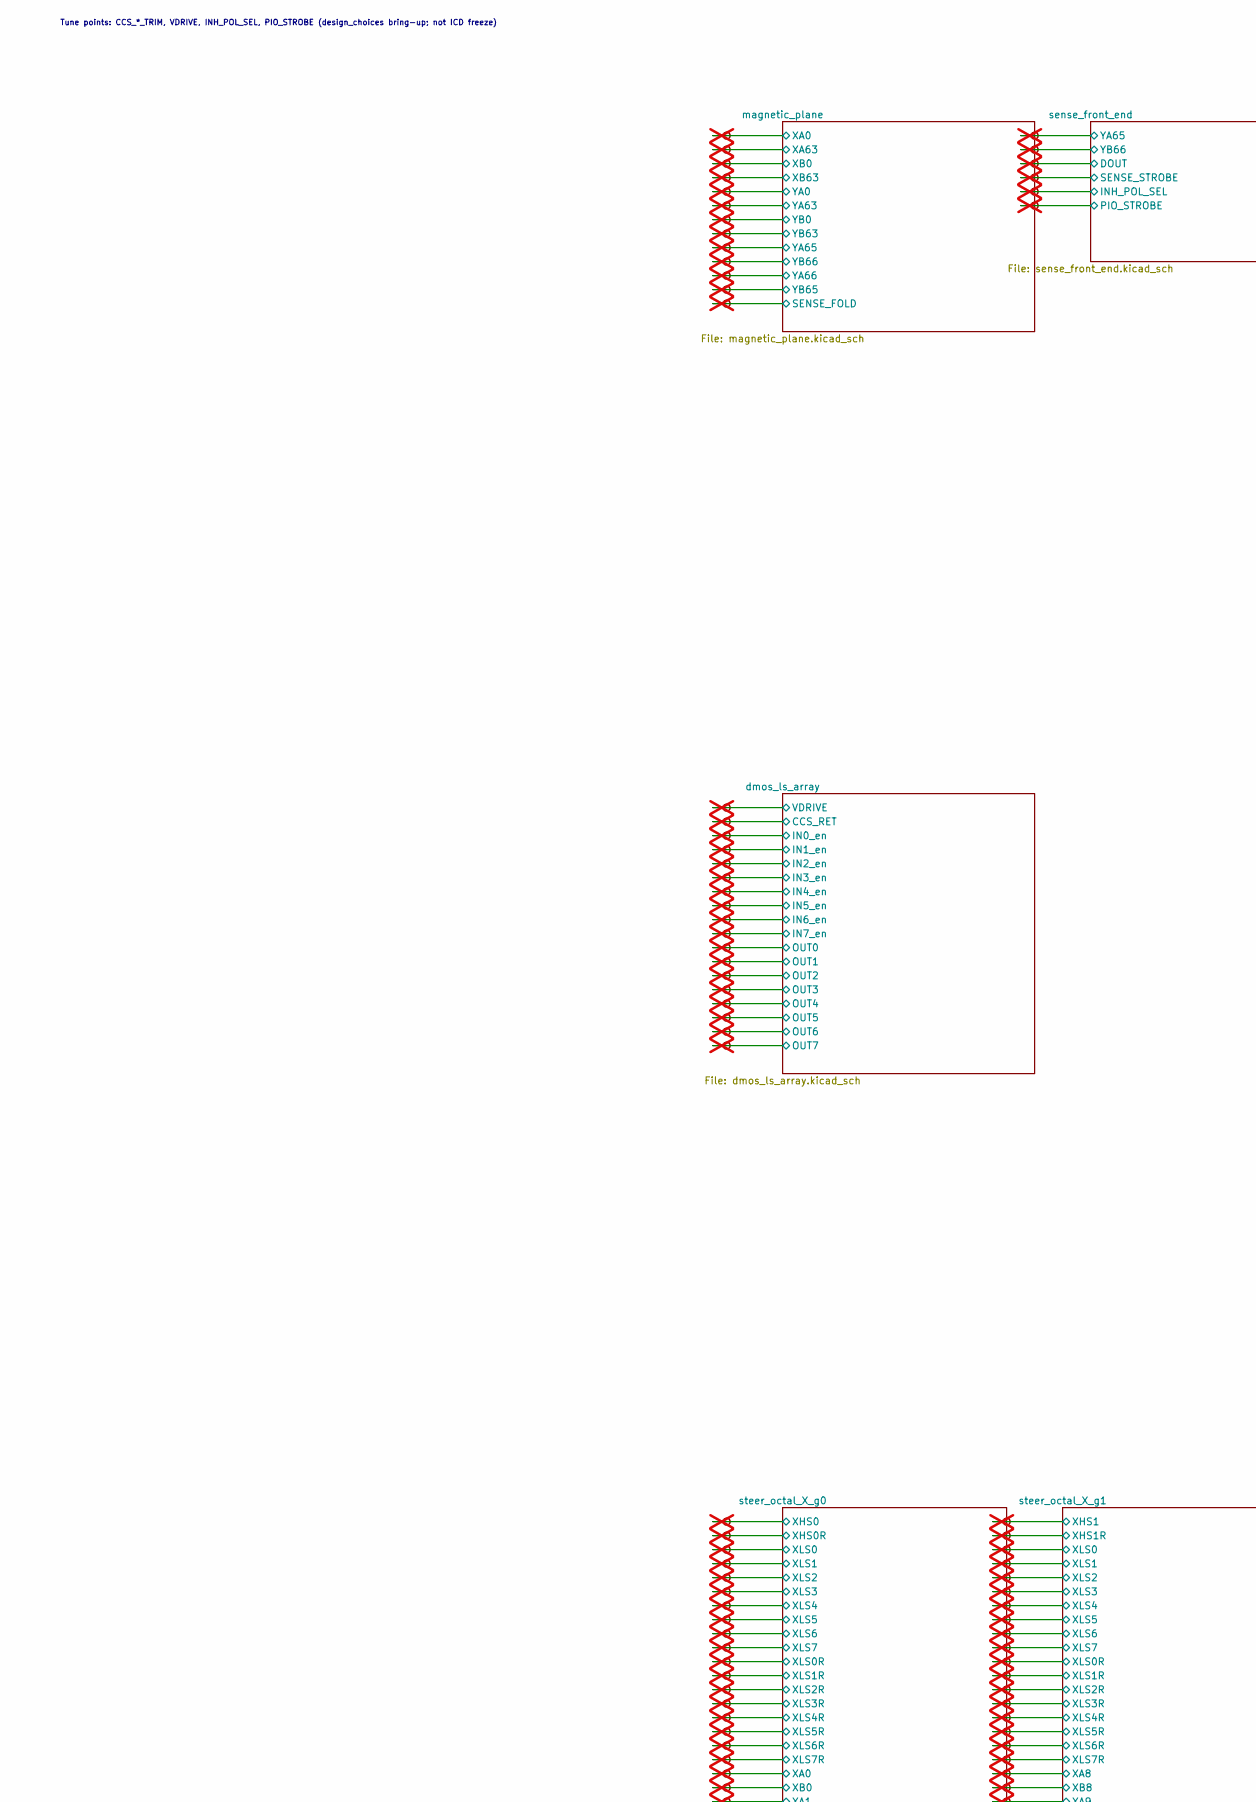
[picture p25: schematic driver.kicad_sch, part in row 1, column 1]

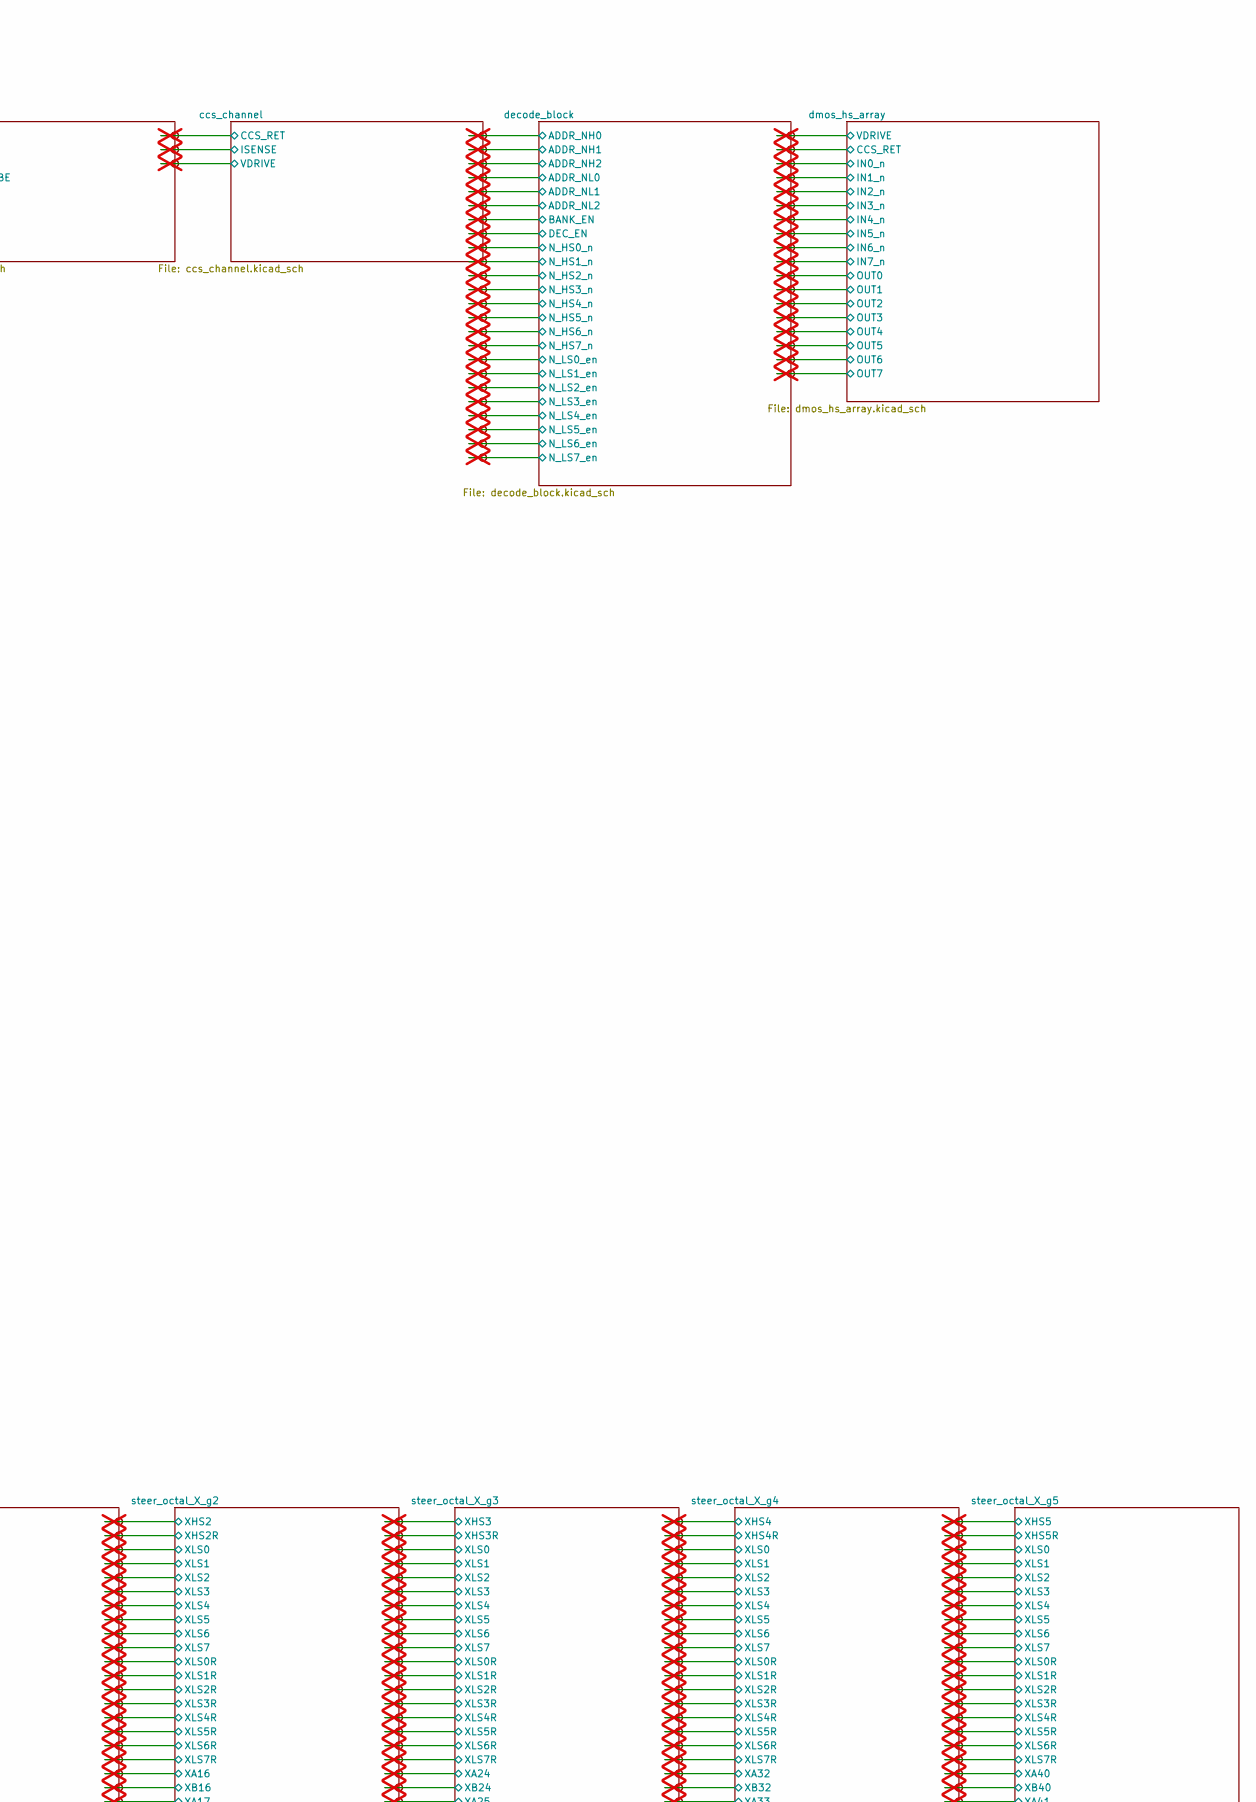
[picture p26: schematic driver.kicad_sch, part in row 1, column 2]

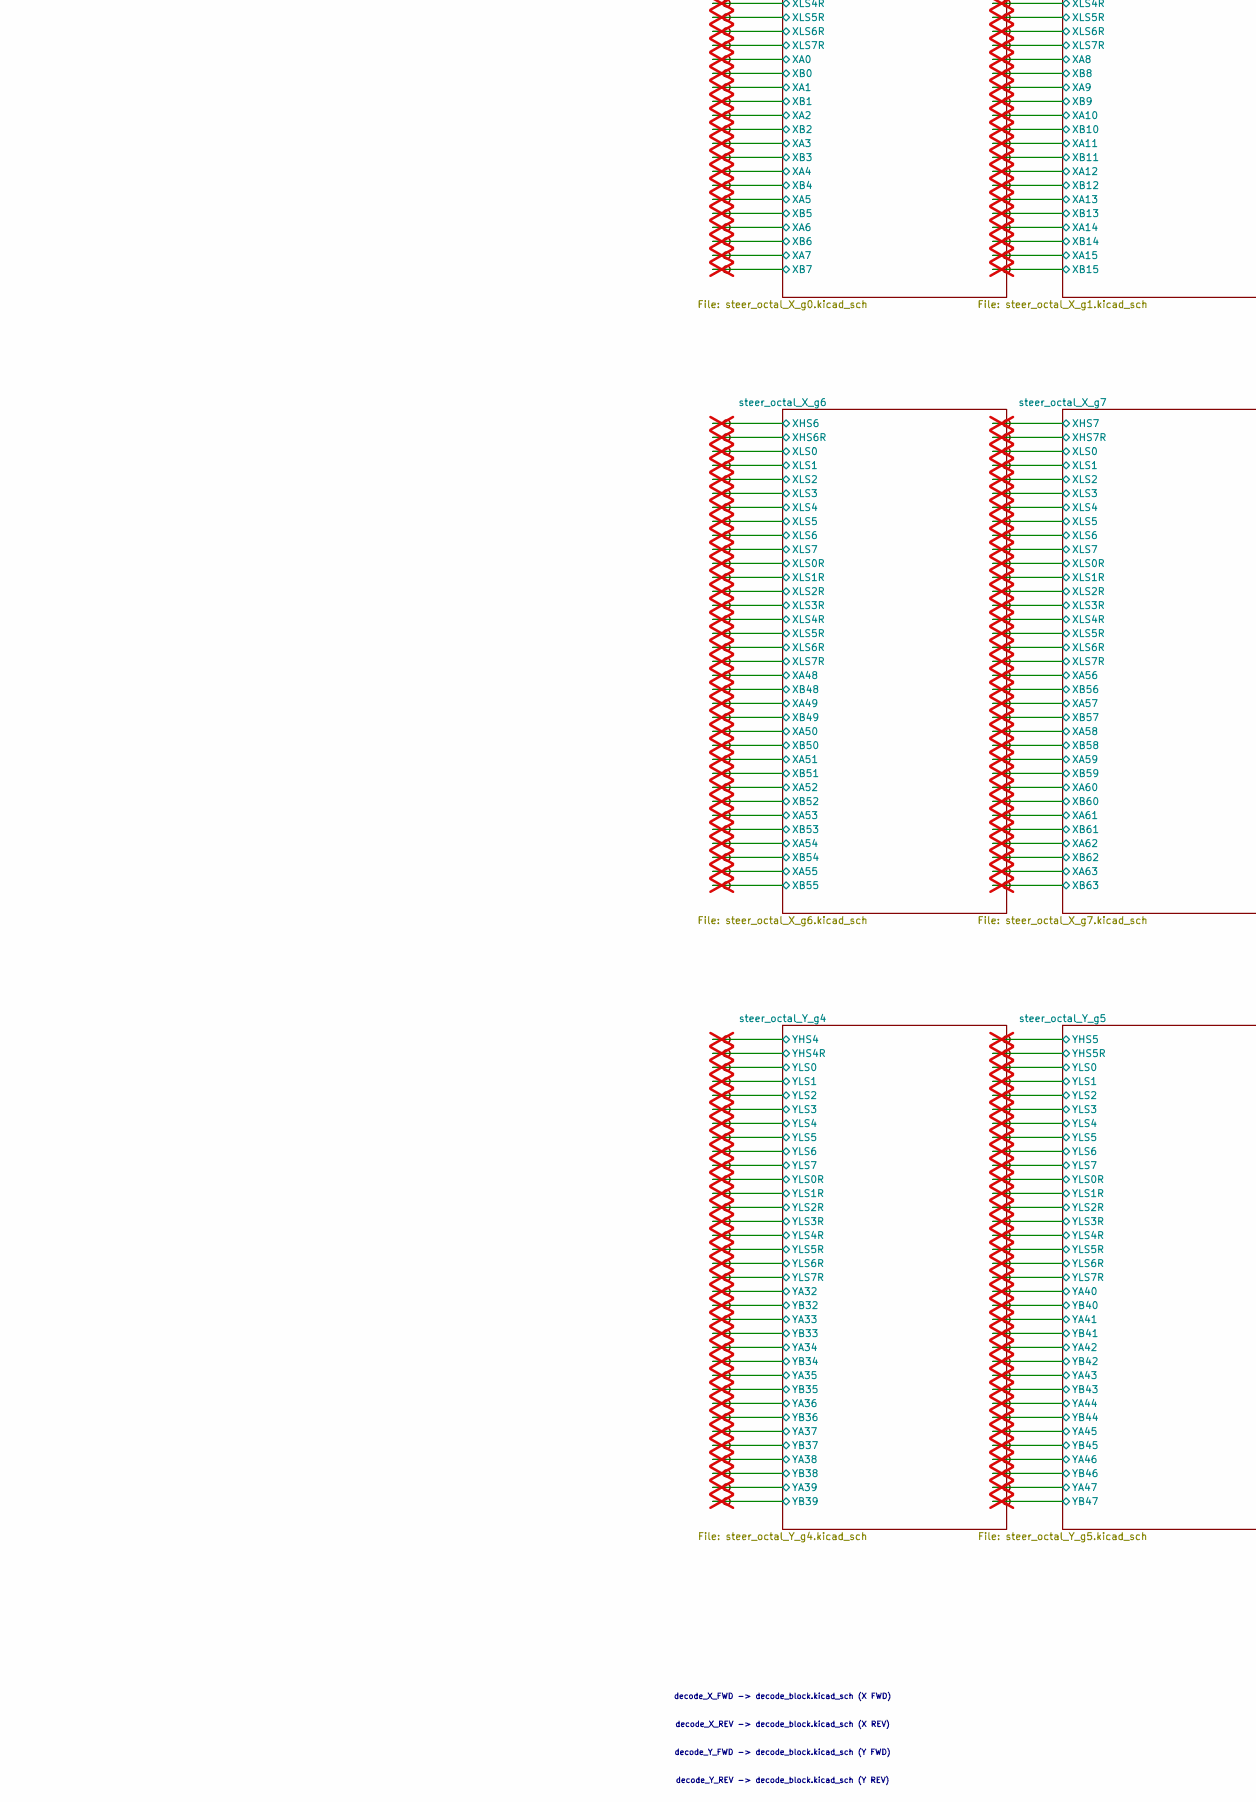
[picture p27: schematic driver.kicad_sch, part in row 2, column 1]

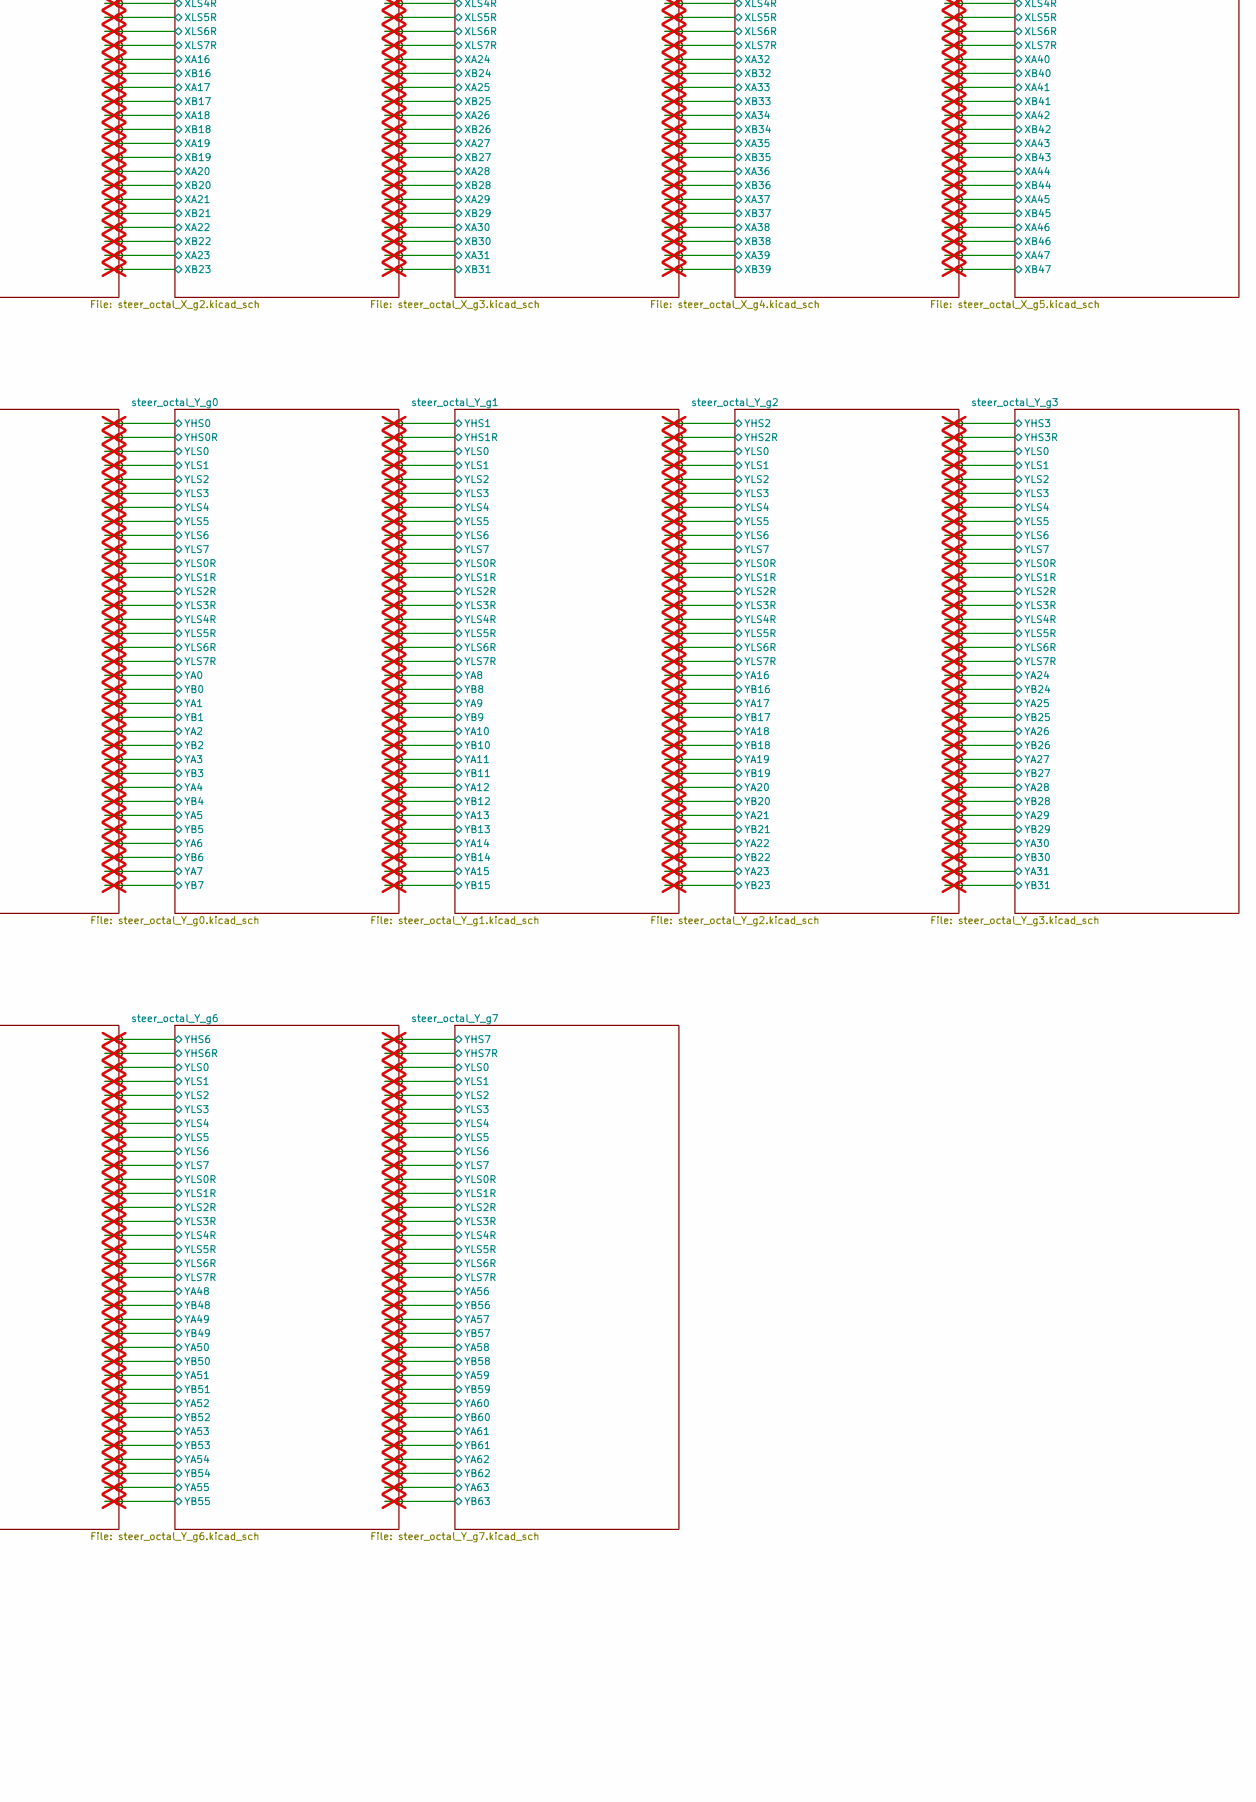
[picture p28: schematic driver.kicad_sch, part in row 2, column 2]

Parts:
TP_ccs_channel_CCS_RET: Stub; not fitted
TP_ccs_channel_ISENSE: Stub; not fitted
TP_ccs_channel_VDRIVE: Stub; not fitted
TP_decode_block_ADDR_NH: Stub; not fitted
TP_decode_block_ADDR_NL: Stub; not fitted
TP_decode_block_BANK_EN: Stub; not fitted
TP_decode_block_DEC_EN: Stub; not fitted
TP_decode_block_N_HS0_n, TP_decode_block_N_HS1_n, TP_decode_block_N_HS2_n, TP_decode_block_N_HS3_n, TP_decode_block_N_HS4_n, TP_decode_block_N_HS5_n, TP_decode_block_N_HS6_n, TP_decode_block_N_HS7_n: Stub; not fitted
TP_decode_block_N_LS0_e, TP_decode_block_N_LS1_e, TP_decode_block_N_LS2_e, TP_decode_block_N_LS3_e, TP_decode_block_N_LS4_e, TP_decode_block_N_LS5_e, TP_decode_block_N_LS6_e, TP_decode_block_N_LS7_e: Stub; not fitted
TP_dmos_hs_array_CCS_RE: Stub; not fitted
TP_dmos_hs_array_IN0_n, TP_dmos_hs_array_IN1_n, TP_dmos_hs_array_IN2_n, TP_dmos_hs_array_IN3_n, TP_dmos_hs_array_IN4_n, TP_dmos_hs_array_IN5_n, TP_dmos_hs_array_IN6_n, TP_dmos_hs_array_IN7_n: Stub; not fitted
TP_dmos_hs_array_OUT0, TP_dmos_hs_array_OUT1, TP_dmos_hs_array_OUT2, TP_dmos_hs_array_OUT3, TP_dmos_hs_array_OUT4, TP_dmos_hs_array_OUT5, TP_dmos_hs_array_OUT6, TP_dmos_hs_array_OUT7: Stub; not fitted
TP_dmos_hs_array_VDRIVE: Stub; not fitted
TP_dmos_ls_array_CCS_RE: Stub; not fitted
TP_dmos_ls_array_IN0_en, TP_dmos_ls_array_IN1_en, TP_dmos_ls_array_IN2_en, TP_dmos_ls_array_IN3_en, TP_dmos_ls_array_IN4_en, TP_dmos_ls_array_IN5_en, TP_dmos_ls_array_IN6_en, TP_dmos_ls_array_IN7_en: Stub; not fitted
TP_dmos_ls_array_OUT0, TP_dmos_ls_array_OUT1, TP_dmos_ls_array_OUT2, TP_dmos_ls_array_OUT3, TP_dmos_ls_array_OUT4, TP_dmos_ls_array_OUT5, TP_dmos_ls_array_OUT6, TP_dmos_ls_array_OUT7: Stub; not fitted
TP_dmos_ls_array_VDRIVE: Stub; not fitted
TP_magnetic_plane_SENSE: Stub; not fitted
TP_magnetic_plane_XA0, TP_magnetic_plane_XA63: Stub; not fitted
TP_magnetic_plane_XB0, TP_magnetic_plane_XB63: Stub; not fitted
TP_magnetic_plane_YA0, TP_magnetic_plane_YA63, TP_magnetic_plane_YA65, TP_magnetic_plane_YA66: Stub; not fitted
TP_magnetic_plane_YB0, TP_magnetic_plane_YB63, TP_magnetic_plane_YB65, TP_magnetic_plane_YB66: Stub; not fitted
TP_sense_front_end_DOUT: Stub; not fitted
TP_sense_front_end_INH_: Stub; not fitted
TP_sense_front_end_PIO_: Stub; not fitted
TP_sense_front_end_SENS: Stub; not fitted
TP_sense_front_end_YA65: Stub; not fitted
TP_sense_front_end_YB66: Stub; not fitted
TP_steer_octal_X_g0_XA0, TP_steer_octal_X_g0_XA1, TP_steer_octal_X_g0_XA2, TP_steer_octal_X_g0_XA3, TP_steer_octal_X_g0_XA4, TP_steer_octal_X_g0_XA5, TP_steer_octal_X_g0_XA6, TP_steer_octal_X_g0_XA7, TP_steer_octal_X_g0_XB0, TP_steer_octal_X_g0_XB1, TP_steer_octal_X_g0_XB2, TP_steer_octal_X_g0_XB3, TP_steer_octal_X_g0_XB4, TP_steer_octal_X_g0_XB5, TP_steer_octal_X_g0_XB6, TP_steer_octal_X_g0_XB7, TP_steer_octal_X_g0_XHS, TP_steer_octal_X_g0_XLS, TP_steer_octal_X_g1_XA1, TP_steer_octal_X_g1_XA8, TP_steer_octal_X_g1_XA9, TP_steer_octal_X_g1_XB1, TP_steer_octal_X_g1_XB8, TP_steer_octal_X_g1_XB9, TP_steer_octal_X_g1_XHS, TP_steer_octal_X_g1_XLS, TP_steer_octal_X_g2_XA1, TP_steer_octal_X_g2_XA2, TP_steer_octal_X_g2_XB1, TP_steer_octal_X_g2_XB2, TP_steer_octal_X_g2_XHS, TP_steer_octal_X_g2_XLS, TP_steer_octal_X_g3_XA2, TP_steer_octal_X_g3_XA3, TP_steer_octal_X_g3_XB2, TP_steer_octal_X_g3_XB3, TP_steer_octal_X_g3_XHS, TP_steer_octal_X_g3_XLS, TP_steer_octal_X_g4_XA3, TP_steer_octal_X_g4_XB3, TP_steer_octal_X_g4_XHS, TP_steer_octal_X_g4_XLS, TP_steer_octal_X_g5_XA4, TP_steer_octal_X_g5_XB4, TP_steer_octal_X_g5_XHS, TP_steer_octal_X_g5_XLS, TP_steer_octal_X_g6_XA4, TP_steer_octal_X_g6_XA5, TP_steer_octal_X_g6_XB4, TP_steer_octal_X_g6_XB5, TP_steer_octal_X_g6_XHS, TP_steer_octal_X_g6_XLS, TP_steer_octal_X_g7_XA5, TP_steer_octal_X_g7_XA6, TP_steer_octal_X_g7_XB5, TP_steer_octal_X_g7_XB6, TP_steer_octal_X_g7_XHS, TP_steer_octal_X_g7_XLS: Stub; not fitted
TP_steer_octal_Y_g0_YA0, TP_steer_octal_Y_g0_YA1, TP_steer_octal_Y_g0_YA2, TP_steer_octal_Y_g0_YA3, TP_steer_octal_Y_g0_YA4, TP_steer_octal_Y_g0_YA5, TP_steer_octal_Y_g0_YA6, TP_steer_octal_Y_g0_YA7, TP_steer_octal_Y_g0_YB0, TP_steer_octal_Y_g0_YB1, TP_steer_octal_Y_g0_YB2, TP_steer_octal_Y_g0_YB3, TP_steer_octal_Y_g0_YB4, TP_steer_octal_Y_g0_YB5, TP_steer_octal_Y_g0_YB6, TP_steer_octal_Y_g0_YB7, TP_steer_octal_Y_g0_YHS, TP_steer_octal_Y_g0_YLS, TP_steer_octal_Y_g1_YA1, TP_steer_octal_Y_g1_YA8, TP_steer_octal_Y_g1_YA9, TP_steer_octal_Y_g1_YB1, TP_steer_octal_Y_g1_YB8, TP_steer_octal_Y_g1_YB9, TP_steer_octal_Y_g1_YHS, TP_steer_octal_Y_g1_YLS, TP_steer_octal_Y_g2_YA1, TP_steer_octal_Y_g2_YA2, TP_steer_octal_Y_g2_YB1, TP_steer_octal_Y_g2_YB2, TP_steer_octal_Y_g2_YHS, TP_steer_octal_Y_g2_YLS, TP_steer_octal_Y_g3_YA2, TP_steer_octal_Y_g3_YA3, TP_steer_octal_Y_g3_YB2, TP_steer_octal_Y_g3_YB3, TP_steer_octal_Y_g3_YHS, TP_steer_octal_Y_g3_YLS, TP_steer_octal_Y_g4_YA3, TP_steer_octal_Y_g4_YB3, TP_steer_octal_Y_g4_YHS, TP_steer_octal_Y_g4_YLS, TP_steer_octal_Y_g5_YA4, TP_steer_octal_Y_g5_YB4, TP_steer_octal_Y_g5_YHS, TP_steer_octal_Y_g5_YLS, TP_steer_octal_Y_g6_YA4, TP_steer_octal_Y_g6_YA5, TP_steer_octal_Y_g6_YB4, TP_steer_octal_Y_g6_YB5, TP_steer_octal_Y_g6_YHS, TP_steer_octal_Y_g6_YLS, TP_steer_octal_Y_g7_YA5, TP_steer_octal_Y_g7_YA6, TP_steer_octal_Y_g7_YB5, TP_steer_octal_Y_g7_YB6, TP_steer_octal_Y_g7_YHS, TP_steer_octal_Y_g7_YLS: Stub; not fitted

Connections:
ADDR_NH0: TP_decode_block_ADDR_NH.1
ADDR_NH1: TP_decode_block_ADDR_NH.1
ADDR_NH2: TP_decode_block_ADDR_NH.1
ADDR_NL0: TP_decode_block_ADDR_NL.1
ADDR_NL1: TP_decode_block_ADDR_NL.1
ADDR_NL2: TP_decode_block_ADDR_NL.1
BANK_EN: TP_decode_block_BANK_EN.1
CCS_RET: TP_ccs_channel_CCS_RET.1, TP_dmos_hs_array_CCS_RE.1, TP_dmos_ls_array_CCS_RE.1
DEC_EN: TP_decode_block_DEC_EN.1
DOUT: TP_sense_front_end_DOUT.1
IN0_en: TP_dmos_ls_array_IN0_en.1
IN0_n: TP_dmos_hs_array_IN0_n.1
IN1_en: TP_dmos_ls_array_IN1_en.1
IN1_n: TP_dmos_hs_array_IN1_n.1
IN2_en: TP_dmos_ls_array_IN2_en.1
IN2_n: TP_dmos_hs_array_IN2_n.1
IN3_en: TP_dmos_ls_array_IN3_en.1
IN3_n: TP_dmos_hs_array_IN3_n.1
IN4_en: TP_dmos_ls_array_IN4_en.1
IN4_n: TP_dmos_hs_array_IN4_n.1
IN5_en: TP_dmos_ls_array_IN5_en.1
IN5_n: TP_dmos_hs_array_IN5_n.1
IN6_en: TP_dmos_ls_array_IN6_en.1
IN6_n: TP_dmos_hs_array_IN6_n.1
IN7_en: TP_dmos_ls_array_IN7_en.1
IN7_n: TP_dmos_hs_array_IN7_n.1
INH_POL_SEL: TP_sense_front_end_INH_.1
ISENSE: TP_ccs_channel_ISENSE.1
N_HS0_n: TP_decode_block_N_HS0_n.1
N_HS1_n: TP_decode_block_N_HS1_n.1
N_HS2_n: TP_decode_block_N_HS2_n.1
N_HS3_n: TP_decode_block_N_HS3_n.1
N_HS4_n: TP_decode_block_N_HS4_n.1
N_HS5_n: TP_decode_block_N_HS5_n.1
N_HS6_n: TP_decode_block_N_HS6_n.1
N_HS7_n: TP_decode_block_N_HS7_n.1
N_LS0_en: TP_decode_block_N_LS0_e.1
N_LS1_en: TP_decode_block_N_LS1_e.1
N_LS2_en: TP_decode_block_N_LS2_e.1
N_LS3_en: TP_decode_block_N_LS3_e.1
N_LS4_en: TP_decode_block_N_LS4_e.1
N_LS5_en: TP_decode_block_N_LS5_e.1
N_LS6_en: TP_decode_block_N_LS6_e.1
N_LS7_en: TP_decode_block_N_LS7_e.1
OUT0: TP_dmos_hs_array_OUT0.1, TP_dmos_ls_array_OUT0.1
OUT1: TP_dmos_hs_array_OUT1.1, TP_dmos_ls_array_OUT1.1
OUT2: TP_dmos_hs_array_OUT2.1, TP_dmos_ls_array_OUT2.1
OUT3: TP_dmos_hs_array_OUT3.1, TP_dmos_ls_array_OUT3.1
OUT4: TP_dmos_hs_array_OUT4.1, TP_dmos_ls_array_OUT4.1
OUT5: TP_dmos_hs_array_OUT5.1, TP_dmos_ls_array_OUT5.1
OUT6: TP_dmos_hs_array_OUT6.1, TP_dmos_ls_array_OUT6.1
OUT7: TP_dmos_hs_array_OUT7.1, TP_dmos_ls_array_OUT7.1
PIO_STROBE: TP_sense_front_end_PIO_.1
SENSE_FOLD: TP_magnetic_plane_SENSE.1
SENSE_STROBE: TP_sense_front_end_SENS.1
VDRIVE: TP_ccs_channel_VDRIVE.1, TP_dmos_hs_array_VDRIVE.1, TP_dmos_ls_array_VDRIVE.1
XA0: TP_magnetic_plane_XA0.1, TP_steer_octal_X_g0_XA0.1
XA1: TP_steer_octal_X_g0_XA1.1
XA2: TP_steer_octal_X_g0_XA2.1
XA3: TP_steer_octal_X_g0_XA3.1
XA4: TP_steer_octal_X_g0_XA4.1
XA5: TP_steer_octal_X_g0_XA5.1
XA6: TP_steer_octal_X_g0_XA6.1
XA7: TP_steer_octal_X_g0_XA7.1
XA8: TP_steer_octal_X_g1_XA8.1
XA9: TP_steer_octal_X_g1_XA9.1
XA10: TP_steer_octal_X_g1_XA1.1
XA11: TP_steer_octal_X_g1_XA1.1
XA12: TP_steer_octal_X_g1_XA1.1
XA13: TP_steer_octal_X_g1_XA1.1
XA14: TP_steer_octal_X_g1_XA1.1
XA15: TP_steer_octal_X_g1_XA1.1
XA16: TP_steer_octal_X_g2_XA1.1
XA17: TP_steer_octal_X_g2_XA1.1
XA18: TP_steer_octal_X_g2_XA1.1
XA19: TP_steer_octal_X_g2_XA1.1
XA20: TP_steer_octal_X_g2_XA2.1
XA21: TP_steer_octal_X_g2_XA2.1
XA22: TP_steer_octal_X_g2_XA2.1
XA23: TP_steer_octal_X_g2_XA2.1
XA24: TP_steer_octal_X_g3_XA2.1
XA25: TP_steer_octal_X_g3_XA2.1
XA26: TP_steer_octal_X_g3_XA2.1
XA27: TP_steer_octal_X_g3_XA2.1
XA28: TP_steer_octal_X_g3_XA2.1
XA29: TP_steer_octal_X_g3_XA2.1
XA30: TP_steer_octal_X_g3_XA3.1
XA31: TP_steer_octal_X_g3_XA3.1
XA32: TP_steer_octal_X_g4_XA3.1
XA33: TP_steer_octal_X_g4_XA3.1
XA34: TP_steer_octal_X_g4_XA3.1
XA35: TP_steer_octal_X_g4_XA3.1
XA36: TP_steer_octal_X_g4_XA3.1
XA37: TP_steer_octal_X_g4_XA3.1
XA38: TP_steer_octal_X_g4_XA3.1
XA39: TP_steer_octal_X_g4_XA3.1
XA40: TP_steer_octal_X_g5_XA4.1
XA41: TP_steer_octal_X_g5_XA4.1
XA42: TP_steer_octal_X_g5_XA4.1
XA43: TP_steer_octal_X_g5_XA4.1
XA44: TP_steer_octal_X_g5_XA4.1
XA45: TP_steer_octal_X_g5_XA4.1
XA46: TP_steer_octal_X_g5_XA4.1
XA47: TP_steer_octal_X_g5_XA4.1
XA48: TP_steer_octal_X_g6_XA4.1
XA49: TP_steer_octal_X_g6_XA4.1
XA50: TP_steer_octal_X_g6_XA5.1
XA51: TP_steer_octal_X_g6_XA5.1
XA52: TP_steer_octal_X_g6_XA5.1
XA53: TP_steer_octal_X_g6_XA5.1
XA54: TP_steer_octal_X_g6_XA5.1
XA55: TP_steer_octal_X_g6_XA5.1
XA56: TP_steer_octal_X_g7_XA5.1
XA57: TP_steer_octal_X_g7_XA5.1
XA58: TP_steer_octal_X_g7_XA5.1
XA59: TP_steer_octal_X_g7_XA5.1
XA60: TP_steer_octal_X_g7_XA6.1
XA61: TP_steer_octal_X_g7_XA6.1
XA62: TP_steer_octal_X_g7_XA6.1
XA63: TP_magnetic_plane_XA63.1, TP_steer_octal_X_g7_XA6.1
XB0: TP_magnetic_plane_XB0.1, TP_steer_octal_X_g0_XB0.1
XB1: TP_steer_octal_X_g0_XB1.1
XB2: TP_steer_octal_X_g0_XB2.1
XB3: TP_steer_octal_X_g0_XB3.1
XB4: TP_steer_octal_X_g0_XB4.1
XB5: TP_steer_octal_X_g0_XB5.1
XB6: TP_steer_octal_X_g0_XB6.1
XB7: TP_steer_octal_X_g0_XB7.1
XB8: TP_steer_octal_X_g1_XB8.1
XB9: TP_steer_octal_X_g1_XB9.1
XB10: TP_steer_octal_X_g1_XB1.1
XB11: TP_steer_octal_X_g1_XB1.1
XB12: TP_steer_octal_X_g1_XB1.1
XB13: TP_steer_octal_X_g1_XB1.1
XB14: TP_steer_octal_X_g1_XB1.1
XB15: TP_steer_octal_X_g1_XB1.1
XB16: TP_steer_octal_X_g2_XB1.1
XB17: TP_steer_octal_X_g2_XB1.1
XB18: TP_steer_octal_X_g2_XB1.1
XB19: TP_steer_octal_X_g2_XB1.1
XB20: TP_steer_octal_X_g2_XB2.1
XB21: TP_steer_octal_X_g2_XB2.1
XB22: TP_steer_octal_X_g2_XB2.1
XB23: TP_steer_octal_X_g2_XB2.1
XB24: TP_steer_octal_X_g3_XB2.1
XB25: TP_steer_octal_X_g3_XB2.1
XB26: TP_steer_octal_X_g3_XB2.1
XB27: TP_steer_octal_X_g3_XB2.1
XB28: TP_steer_octal_X_g3_XB2.1
XB29: TP_steer_octal_X_g3_XB2.1
XB30: TP_steer_octal_X_g3_XB3.1
XB31: TP_steer_octal_X_g3_XB3.1
XB32: TP_steer_octal_X_g4_XB3.1
XB33: TP_steer_octal_X_g4_XB3.1
XB34: TP_steer_octal_X_g4_XB3.1
XB35: TP_steer_octal_X_g4_XB3.1
XB36: TP_steer_octal_X_g4_XB3.1
XB37: TP_steer_octal_X_g4_XB3.1
XB38: TP_steer_octal_X_g4_XB3.1
XB39: TP_steer_octal_X_g4_XB3.1
XB40: TP_steer_octal_X_g5_XB4.1
XB41: TP_steer_octal_X_g5_XB4.1
XB42: TP_steer_octal_X_g5_XB4.1
XB43: TP_steer_octal_X_g5_XB4.1
XB44: TP_steer_octal_X_g5_XB4.1
XB45: TP_steer_octal_X_g5_XB4.1
XB46: TP_steer_octal_X_g5_XB4.1
XB47: TP_steer_octal_X_g5_XB4.1
XB48: TP_steer_octal_X_g6_XB4.1
XB49: TP_steer_octal_X_g6_XB4.1
XB50: TP_steer_octal_X_g6_XB5.1
XB51: TP_steer_octal_X_g6_XB5.1
XB52: TP_steer_octal_X_g6_XB5.1
XB53: TP_steer_octal_X_g6_XB5.1
XB54: TP_steer_octal_X_g6_XB5.1
XB55: TP_steer_octal_X_g6_XB5.1
XB56: TP_steer_octal_X_g7_XB5.1
XB57: TP_steer_octal_X_g7_XB5.1
XB58: TP_steer_octal_X_g7_XB5.1
XB59: TP_steer_octal_X_g7_XB5.1
XB60: TP_steer_octal_X_g7_XB6.1
XB61: TP_steer_octal_X_g7_XB6.1
XB62: TP_steer_octal_X_g7_XB6.1
XB63: TP_magnetic_plane_XB63.1, TP_steer_octal_X_g7_XB6.1
XHS0: TP_steer_octal_X_g0_XHS.1
XHS0R: TP_steer_octal_X_g0_XHS.1
XHS1: TP_steer_octal_X_g1_XHS.1
XHS1R: TP_steer_octal_X_g1_XHS.1
XHS2: TP_steer_octal_X_g2_XHS.1
XHS2R: TP_steer_octal_X_g2_XHS.1
XHS3: TP_steer_octal_X_g3_XHS.1
XHS3R: TP_steer_octal_X_g3_XHS.1
XHS4: TP_steer_octal_X_g4_XHS.1
XHS4R: TP_steer_octal_X_g4_XHS.1
XHS5: TP_steer_octal_X_g5_XHS.1
XHS5R: TP_steer_octal_X_g5_XHS.1
XHS6: TP_steer_octal_X_g6_XHS.1
XHS6R: TP_steer_octal_X_g6_XHS.1
XHS7: TP_steer_octal_X_g7_XHS.1
XHS7R: TP_steer_octal_X_g7_XHS.1
XLS0: TP_steer_octal_X_g0_XLS.1, TP_steer_octal_X_g1_XLS.1, TP_steer_octal_X_g2_XLS.1, TP_steer_octal_X_g3_XLS.1, TP_steer_octal_X_g4_XLS.1, TP_steer_octal_X_g5_XLS.1, TP_steer_octal_X_g6_XLS.1, TP_steer_octal_X_g7_XLS.1
XLS0R: TP_steer_octal_X_g0_XLS.1, TP_steer_octal_X_g1_XLS.1, TP_steer_octal_X_g2_XLS.1, TP_steer_octal_X_g3_XLS.1, TP_steer_octal_X_g4_XLS.1, TP_steer_octal_X_g5_XLS.1, TP_steer_octal_X_g6_XLS.1, TP_steer_octal_X_g7_XLS.1
XLS1: TP_steer_octal_X_g0_XLS.1, TP_steer_octal_X_g1_XLS.1, TP_steer_octal_X_g2_XLS.1, TP_steer_octal_X_g3_XLS.1, TP_steer_octal_X_g4_XLS.1, TP_steer_octal_X_g5_XLS.1, TP_steer_octal_X_g6_XLS.1, TP_steer_octal_X_g7_XLS.1
XLS1R: TP_steer_octal_X_g0_XLS.1, TP_steer_octal_X_g1_XLS.1, TP_steer_octal_X_g2_XLS.1, TP_steer_octal_X_g3_XLS.1, TP_steer_octal_X_g4_XLS.1, TP_steer_octal_X_g5_XLS.1, TP_steer_octal_X_g6_XLS.1, TP_steer_octal_X_g7_XLS.1
XLS2: TP_steer_octal_X_g0_XLS.1, TP_steer_octal_X_g1_XLS.1, TP_steer_octal_X_g2_XLS.1, TP_steer_octal_X_g3_XLS.1, TP_steer_octal_X_g4_XLS.1, TP_steer_octal_X_g5_XLS.1, TP_steer_octal_X_g6_XLS.1, TP_steer_octal_X_g7_XLS.1
XLS2R: TP_steer_octal_X_g0_XLS.1, TP_steer_octal_X_g1_XLS.1, TP_steer_octal_X_g2_XLS.1, TP_steer_octal_X_g3_XLS.1, TP_steer_octal_X_g4_XLS.1, TP_steer_octal_X_g5_XLS.1, TP_steer_octal_X_g6_XLS.1, TP_steer_octal_X_g7_XLS.1
XLS3: TP_steer_octal_X_g0_XLS.1, TP_steer_octal_X_g1_XLS.1, TP_steer_octal_X_g2_XLS.1, TP_steer_octal_X_g3_XLS.1, TP_steer_octal_X_g4_XLS.1, TP_steer_octal_X_g5_XLS.1, TP_steer_octal_X_g6_XLS.1, TP_steer_octal_X_g7_XLS.1
XLS3R: TP_steer_octal_X_g0_XLS.1, TP_steer_octal_X_g1_XLS.1, TP_steer_octal_X_g2_XLS.1, TP_steer_octal_X_g3_XLS.1, TP_steer_octal_X_g4_XLS.1, TP_steer_octal_X_g5_XLS.1, TP_steer_octal_X_g6_XLS.1, TP_steer_octal_X_g7_XLS.1
XLS4: TP_steer_octal_X_g0_XLS.1, TP_steer_octal_X_g1_XLS.1, TP_steer_octal_X_g2_XLS.1, TP_steer_octal_X_g3_XLS.1, TP_steer_octal_X_g4_XLS.1, TP_steer_octal_X_g5_XLS.1, TP_steer_octal_X_g6_XLS.1, TP_steer_octal_X_g7_XLS.1
XLS4R: TP_steer_octal_X_g0_XLS.1, TP_steer_octal_X_g1_XLS.1, TP_steer_octal_X_g2_XLS.1, TP_steer_octal_X_g3_XLS.1, TP_steer_octal_X_g4_XLS.1, TP_steer_octal_X_g5_XLS.1, TP_steer_octal_X_g6_XLS.1, TP_steer_octal_X_g7_XLS.1
XLS5: TP_steer_octal_X_g0_XLS.1, TP_steer_octal_X_g1_XLS.1, TP_steer_octal_X_g2_XLS.1, TP_steer_octal_X_g3_XLS.1, TP_steer_octal_X_g4_XLS.1, TP_steer_octal_X_g5_XLS.1, TP_steer_octal_X_g6_XLS.1, TP_steer_octal_X_g7_XLS.1
XLS5R: TP_steer_octal_X_g0_XLS.1, TP_steer_octal_X_g1_XLS.1, TP_steer_octal_X_g2_XLS.1, TP_steer_octal_X_g3_XLS.1, TP_steer_octal_X_g4_XLS.1, TP_steer_octal_X_g5_XLS.1, TP_steer_octal_X_g6_XLS.1, TP_steer_octal_X_g7_XLS.1
XLS6: TP_steer_octal_X_g0_XLS.1, TP_steer_octal_X_g1_XLS.1, TP_steer_octal_X_g2_XLS.1, TP_steer_octal_X_g3_XLS.1, TP_steer_octal_X_g4_XLS.1, TP_steer_octal_X_g5_XLS.1, TP_steer_octal_X_g6_XLS.1, TP_steer_octal_X_g7_XLS.1
XLS6R: TP_steer_octal_X_g0_XLS.1, TP_steer_octal_X_g1_XLS.1, TP_steer_octal_X_g2_XLS.1, TP_steer_octal_X_g3_XLS.1, TP_steer_octal_X_g4_XLS.1, TP_steer_octal_X_g5_XLS.1, TP_steer_octal_X_g6_XLS.1, TP_steer_octal_X_g7_XLS.1
XLS7: TP_steer_octal_X_g0_XLS.1, TP_steer_octal_X_g1_XLS.1, TP_steer_octal_X_g2_XLS.1, TP_steer_octal_X_g3_XLS.1, TP_steer_octal_X_g4_XLS.1, TP_steer_octal_X_g5_XLS.1, TP_steer_octal_X_g6_XLS.1, TP_steer_octal_X_g7_XLS.1
XLS7R: TP_steer_octal_X_g0_XLS.1, TP_steer_octal_X_g1_XLS.1, TP_steer_octal_X_g2_XLS.1, TP_steer_octal_X_g3_XLS.1, TP_steer_octal_X_g4_XLS.1, TP_steer_octal_X_g5_XLS.1, TP_steer_octal_X_g6_XLS.1, TP_steer_octal_X_g7_XLS.1
YA0: TP_magnetic_plane_YA0.1, TP_steer_octal_Y_g0_YA0.1
YA1: TP_steer_octal_Y_g0_YA1.1
YA2: TP_steer_octal_Y_g0_YA2.1
YA3: TP_steer_octal_Y_g0_YA3.1
YA4: TP_steer_octal_Y_g0_YA4.1
YA5: TP_steer_octal_Y_g0_YA5.1
YA6: TP_steer_octal_Y_g0_YA6.1
YA7: TP_steer_octal_Y_g0_YA7.1
YA8: TP_steer_octal_Y_g1_YA8.1
YA9: TP_steer_octal_Y_g1_YA9.1
YA10: TP_steer_octal_Y_g1_YA1.1
YA11: TP_steer_octal_Y_g1_YA1.1
YA12: TP_steer_octal_Y_g1_YA1.1
YA13: TP_steer_octal_Y_g1_YA1.1
YA14: TP_steer_octal_Y_g1_YA1.1
YA15: TP_steer_octal_Y_g1_YA1.1
YA16: TP_steer_octal_Y_g2_YA1.1
YA17: TP_steer_octal_Y_g2_YA1.1
YA18: TP_steer_octal_Y_g2_YA1.1
YA19: TP_steer_octal_Y_g2_YA1.1
YA20: TP_steer_octal_Y_g2_YA2.1
YA21: TP_steer_octal_Y_g2_YA2.1
YA22: TP_steer_octal_Y_g2_YA2.1
YA23: TP_steer_octal_Y_g2_YA2.1
YA24: TP_steer_octal_Y_g3_YA2.1
YA25: TP_steer_octal_Y_g3_YA2.1
YA26: TP_steer_octal_Y_g3_YA2.1
YA27: TP_steer_octal_Y_g3_YA2.1
YA28: TP_steer_octal_Y_g3_YA2.1
YA29: TP_steer_octal_Y_g3_YA2.1
YA30: TP_steer_octal_Y_g3_YA3.1
YA31: TP_steer_octal_Y_g3_YA3.1
YA32: TP_steer_octal_Y_g4_YA3.1
YA33: TP_steer_octal_Y_g4_YA3.1
YA34: TP_steer_octal_Y_g4_YA3.1
YA35: TP_steer_octal_Y_g4_YA3.1
YA36: TP_steer_octal_Y_g4_YA3.1
YA37: TP_steer_octal_Y_g4_YA3.1
YA38: TP_steer_octal_Y_g4_YA3.1
YA39: TP_steer_octal_Y_g4_YA3.1
YA40: TP_steer_octal_Y_g5_YA4.1
YA41: TP_steer_octal_Y_g5_YA4.1
YA42: TP_steer_octal_Y_g5_YA4.1
YA43: TP_steer_octal_Y_g5_YA4.1
YA44: TP_steer_octal_Y_g5_YA4.1
YA45: TP_steer_octal_Y_g5_YA4.1
YA46: TP_steer_octal_Y_g5_YA4.1
YA47: TP_steer_octal_Y_g5_YA4.1
YA48: TP_steer_octal_Y_g6_YA4.1
YA49: TP_steer_octal_Y_g6_YA4.1
YA50: TP_steer_octal_Y_g6_YA5.1
YA51: TP_steer_octal_Y_g6_YA5.1
YA52: TP_steer_octal_Y_g6_YA5.1
YA53: TP_steer_octal_Y_g6_YA5.1
YA54: TP_steer_octal_Y_g6_YA5.1
YA55: TP_steer_octal_Y_g6_YA5.1
YA56: TP_steer_octal_Y_g7_YA5.1
YA57: TP_steer_octal_Y_g7_YA5.1
YA58: TP_steer_octal_Y_g7_YA5.1
YA59: TP_steer_octal_Y_g7_YA5.1
YA60: TP_steer_octal_Y_g7_YA6.1
YA61: TP_steer_octal_Y_g7_YA6.1
YA62: TP_steer_octal_Y_g7_YA6.1
YA63: TP_magnetic_plane_YA63.1, TP_steer_octal_Y_g7_YA6.1
YA65: TP_magnetic_plane_YA65.1, TP_sense_front_end_YA65.1
YA66: TP_magnetic_plane_YA66.1
YB0: TP_magnetic_plane_YB0.1, TP_steer_octal_Y_g0_YB0.1
YB1: TP_steer_octal_Y_g0_YB1.1
YB2: TP_steer_octal_Y_g0_YB2.1
YB3: TP_steer_octal_Y_g0_YB3.1
YB4: TP_steer_octal_Y_g0_YB4.1
YB5: TP_steer_octal_Y_g0_YB5.1
YB6: TP_steer_octal_Y_g0_YB6.1
YB7: TP_steer_octal_Y_g0_YB7.1
YB8: TP_steer_octal_Y_g1_YB8.1
YB9: TP_steer_octal_Y_g1_YB9.1
YB10: TP_steer_octal_Y_g1_YB1.1
YB11: TP_steer_octal_Y_g1_YB1.1
YB12: TP_steer_octal_Y_g1_YB1.1
YB13: TP_steer_octal_Y_g1_YB1.1
YB14: TP_steer_octal_Y_g1_YB1.1
YB15: TP_steer_octal_Y_g1_YB1.1
YB16: TP_steer_octal_Y_g2_YB1.1
YB17: TP_steer_octal_Y_g2_YB1.1
YB18: TP_steer_octal_Y_g2_YB1.1
YB19: TP_steer_octal_Y_g2_YB1.1
YB20: TP_steer_octal_Y_g2_YB2.1
YB21: TP_steer_octal_Y_g2_YB2.1
YB22: TP_steer_octal_Y_g2_YB2.1
YB23: TP_steer_octal_Y_g2_YB2.1
YB24: TP_steer_octal_Y_g3_YB2.1
YB25: TP_steer_octal_Y_g3_YB2.1
YB26: TP_steer_octal_Y_g3_YB2.1
YB27: TP_steer_octal_Y_g3_YB2.1
YB28: TP_steer_octal_Y_g3_YB2.1
YB29: TP_steer_octal_Y_g3_YB2.1
YB30: TP_steer_octal_Y_g3_YB3.1
YB31: TP_steer_octal_Y_g3_YB3.1
YB32: TP_steer_octal_Y_g4_YB3.1
YB33: TP_steer_octal_Y_g4_YB3.1
YB34: TP_steer_octal_Y_g4_YB3.1
YB35: TP_steer_octal_Y_g4_YB3.1
YB36: TP_steer_octal_Y_g4_YB3.1
YB37: TP_steer_octal_Y_g4_YB3.1
YB38: TP_steer_octal_Y_g4_YB3.1
YB39: TP_steer_octal_Y_g4_YB3.1
YB40: TP_steer_octal_Y_g5_YB4.1
YB41: TP_steer_octal_Y_g5_YB4.1
YB42: TP_steer_octal_Y_g5_YB4.1
YB43: TP_steer_octal_Y_g5_YB4.1
YB44: TP_steer_octal_Y_g5_YB4.1
YB45: TP_steer_octal_Y_g5_YB4.1
YB46: TP_steer_octal_Y_g5_YB4.1
YB47: TP_steer_octal_Y_g5_YB4.1
YB48: TP_steer_octal_Y_g6_YB4.1
YB49: TP_steer_octal_Y_g6_YB4.1
YB50: TP_steer_octal_Y_g6_YB5.1
YB51: TP_steer_octal_Y_g6_YB5.1
YB52: TP_steer_octal_Y_g6_YB5.1
YB53: TP_steer_octal_Y_g6_YB5.1
YB54: TP_steer_octal_Y_g6_YB5.1
YB55: TP_steer_octal_Y_g6_YB5.1
YB56: TP_steer_octal_Y_g7_YB5.1
YB57: TP_steer_octal_Y_g7_YB5.1
YB58: TP_steer_octal_Y_g7_YB5.1
YB59: TP_steer_octal_Y_g7_YB5.1
YB60: TP_steer_octal_Y_g7_YB6.1
YB61: TP_steer_octal_Y_g7_YB6.1
YB62: TP_steer_octal_Y_g7_YB6.1
YB63: TP_magnetic_plane_YB63.1, TP_steer_octal_Y_g7_YB6.1
YB65: TP_magnetic_plane_YB65.1
YB66: TP_magnetic_plane_YB66.1, TP_sense_front_end_YB66.1
YHS0: TP_steer_octal_Y_g0_YHS.1
YHS0R: TP_steer_octal_Y_g0_YHS.1
YHS1: TP_steer_octal_Y_g1_YHS.1
YHS1R: TP_steer_octal_Y_g1_YHS.1
YHS2: TP_steer_octal_Y_g2_YHS.1
YHS2R: TP_steer_octal_Y_g2_YHS.1
YHS3: TP_steer_octal_Y_g3_YHS.1
YHS3R: TP_steer_octal_Y_g3_YHS.1
YHS4: TP_steer_octal_Y_g4_YHS.1
YHS4R: TP_steer_octal_Y_g4_YHS.1
YHS5: TP_steer_octal_Y_g5_YHS.1
YHS5R: TP_steer_octal_Y_g5_YHS.1
YHS6: TP_steer_octal_Y_g6_YHS.1
YHS6R: TP_steer_octal_Y_g6_YHS.1
YHS7: TP_steer_octal_Y_g7_YHS.1
YHS7R: TP_steer_octal_Y_g7_YHS.1
YLS0: TP_steer_octal_Y_g0_YLS.1, TP_steer_octal_Y_g1_YLS.1, TP_steer_octal_Y_g2_YLS.1, TP_steer_octal_Y_g3_YLS.1, TP_steer_octal_Y_g4_YLS.1, TP_steer_octal_Y_g5_YLS.1, TP_steer_octal_Y_g6_YLS.1, TP_steer_octal_Y_g7_YLS.1
YLS0R: TP_steer_octal_Y_g0_YLS.1, TP_steer_octal_Y_g1_YLS.1, TP_steer_octal_Y_g2_YLS.1, TP_steer_octal_Y_g3_YLS.1, TP_steer_octal_Y_g4_YLS.1, TP_steer_octal_Y_g5_YLS.1, TP_steer_octal_Y_g6_YLS.1, TP_steer_octal_Y_g7_YLS.1
YLS1: TP_steer_octal_Y_g0_YLS.1, TP_steer_octal_Y_g1_YLS.1, TP_steer_octal_Y_g2_YLS.1, TP_steer_octal_Y_g3_YLS.1, TP_steer_octal_Y_g4_YLS.1, TP_steer_octal_Y_g5_YLS.1, TP_steer_octal_Y_g6_YLS.1, TP_steer_octal_Y_g7_YLS.1
YLS1R: TP_steer_octal_Y_g0_YLS.1, TP_steer_octal_Y_g1_YLS.1, TP_steer_octal_Y_g2_YLS.1, TP_steer_octal_Y_g3_YLS.1, TP_steer_octal_Y_g4_YLS.1, TP_steer_octal_Y_g5_YLS.1, TP_steer_octal_Y_g6_YLS.1, TP_steer_octal_Y_g7_YLS.1
YLS2: TP_steer_octal_Y_g0_YLS.1, TP_steer_octal_Y_g1_YLS.1, TP_steer_octal_Y_g2_YLS.1, TP_steer_octal_Y_g3_YLS.1, TP_steer_octal_Y_g4_YLS.1, TP_steer_octal_Y_g5_YLS.1, TP_steer_octal_Y_g6_YLS.1, TP_steer_octal_Y_g7_YLS.1
YLS2R: TP_steer_octal_Y_g0_YLS.1, TP_steer_octal_Y_g1_YLS.1, TP_steer_octal_Y_g2_YLS.1, TP_steer_octal_Y_g3_YLS.1, TP_steer_octal_Y_g4_YLS.1, TP_steer_octal_Y_g5_YLS.1, TP_steer_octal_Y_g6_YLS.1, TP_steer_octal_Y_g7_YLS.1
YLS3: TP_steer_octal_Y_g0_YLS.1, TP_steer_octal_Y_g1_YLS.1, TP_steer_octal_Y_g2_YLS.1, TP_steer_octal_Y_g3_YLS.1, TP_steer_octal_Y_g4_YLS.1, TP_steer_octal_Y_g5_YLS.1, TP_steer_octal_Y_g6_YLS.1, TP_steer_octal_Y_g7_YLS.1
YLS3R: TP_steer_octal_Y_g0_YLS.1, TP_steer_octal_Y_g1_YLS.1, TP_steer_octal_Y_g2_YLS.1, TP_steer_octal_Y_g3_YLS.1, TP_steer_octal_Y_g4_YLS.1, TP_steer_octal_Y_g5_YLS.1, TP_steer_octal_Y_g6_YLS.1, TP_steer_octal_Y_g7_YLS.1
YLS4: TP_steer_octal_Y_g0_YLS.1, TP_steer_octal_Y_g1_YLS.1, TP_steer_octal_Y_g2_YLS.1, TP_steer_octal_Y_g3_YLS.1, TP_steer_octal_Y_g4_YLS.1, TP_steer_octal_Y_g5_YLS.1, TP_steer_octal_Y_g6_YLS.1, TP_steer_octal_Y_g7_YLS.1
YLS4R: TP_steer_octal_Y_g0_YLS.1, TP_steer_octal_Y_g1_YLS.1, TP_steer_octal_Y_g2_YLS.1, TP_steer_octal_Y_g3_YLS.1, TP_steer_octal_Y_g4_YLS.1, TP_steer_octal_Y_g5_YLS.1, TP_steer_octal_Y_g6_YLS.1, TP_steer_octal_Y_g7_YLS.1
YLS5: TP_steer_octal_Y_g0_YLS.1, TP_steer_octal_Y_g1_YLS.1, TP_steer_octal_Y_g2_YLS.1, TP_steer_octal_Y_g3_YLS.1, TP_steer_octal_Y_g4_YLS.1, TP_steer_octal_Y_g5_YLS.1, TP_steer_octal_Y_g6_YLS.1, TP_steer_octal_Y_g7_YLS.1
YLS5R: TP_steer_octal_Y_g0_YLS.1, TP_steer_octal_Y_g1_YLS.1, TP_steer_octal_Y_g2_YLS.1, TP_steer_octal_Y_g3_YLS.1, TP_steer_octal_Y_g4_YLS.1, TP_steer_octal_Y_g5_YLS.1, TP_steer_octal_Y_g6_YLS.1, TP_steer_octal_Y_g7_YLS.1
YLS6: TP_steer_octal_Y_g0_YLS.1, TP_steer_octal_Y_g1_YLS.1, TP_steer_octal_Y_g2_YLS.1, TP_steer_octal_Y_g3_YLS.1, TP_steer_octal_Y_g4_YLS.1, TP_steer_octal_Y_g5_YLS.1, TP_steer_octal_Y_g6_YLS.1, TP_steer_octal_Y_g7_YLS.1
YLS6R: TP_steer_octal_Y_g0_YLS.1, TP_steer_octal_Y_g1_YLS.1, TP_steer_octal_Y_g2_YLS.1, TP_steer_octal_Y_g3_YLS.1, TP_steer_octal_Y_g4_YLS.1, TP_steer_octal_Y_g5_YLS.1, TP_steer_octal_Y_g6_YLS.1, TP_steer_octal_Y_g7_YLS.1
YLS7: TP_steer_octal_Y_g0_YLS.1, TP_steer_octal_Y_g1_YLS.1, TP_steer_octal_Y_g2_YLS.1, TP_steer_octal_Y_g3_YLS.1, TP_steer_octal_Y_g4_YLS.1, TP_steer_octal_Y_g5_YLS.1, TP_steer_octal_Y_g6_YLS.1, TP_steer_octal_Y_g7_YLS.1
YLS7R: TP_steer_octal_Y_g0_YLS.1, TP_steer_octal_Y_g1_YLS.1, TP_steer_octal_Y_g2_YLS.1, TP_steer_octal_Y_g3_YLS.1, TP_steer_octal_Y_g4_YLS.1, TP_steer_octal_Y_g5_YLS.1, TP_steer_octal_Y_g6_YLS.1, TP_steer_octal_Y_g7_YLS.1

Notes on the sheet:
decode_X_FWD -> decode_block.kicad_sch (X FWD)
decode_Y_FWD -> decode_block.kicad_sch (Y FWD)
Tune points: CCS_*_TRIM, VDRIVE, INH_POL_SEL, PIO_STROBE (design_choices bring-up; not ICD freeze)
decode_X_REV -> decode_block.kicad_sch (X REV)
decode_Y_REV -> decode_block.kicad_sch (Y REV)
