fractalclockwork/core-memory-redux/kicad/driver_64x64/magnetic_plane.kicad_sch

## KiCad design kicad/driver_64x64/magnetic_plane.kicad_sch (2026-10-05)

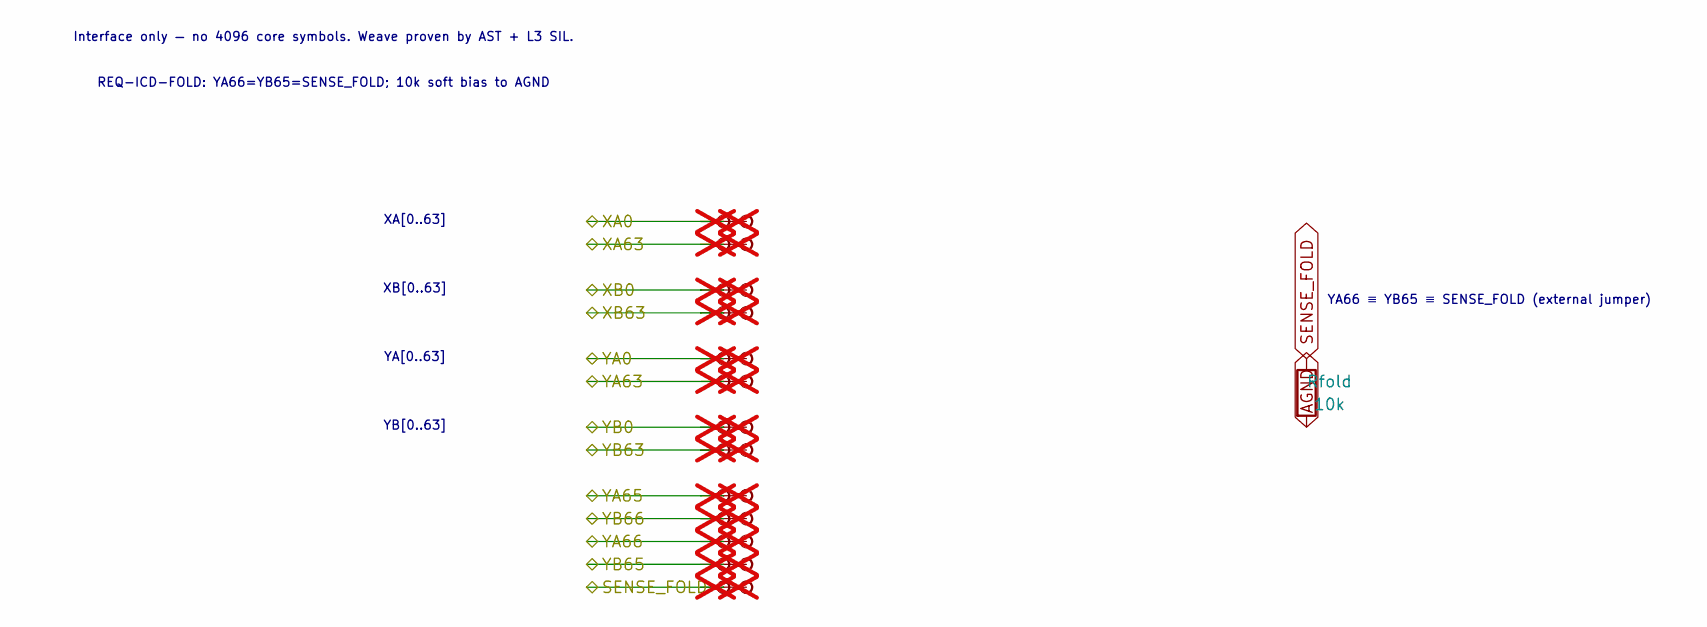
[picture p29: schematic magnetic_plane.kicad_sch]

Parts:
Rfold: 10k
TP_SENSE_FOLD: Stub; not fitted
TP_SENSE_FOLDb: Stub; not fitted
TP_XA0, TP_XA0b, TP_XA63, TP_XA63b: Stub; not fitted
TP_XB0, TP_XB0b, TP_XB63, TP_XB63b: Stub; not fitted
TP_YA0, TP_YA0b, TP_YA63, TP_YA63b, TP_YA65, TP_YA65b, TP_YA66, TP_YA66b: Stub; not fitted
TP_YB0, TP_YB0b, TP_YB63, TP_YB63b, TP_YB65, TP_YB65b, TP_YB66, TP_YB66b: Stub; not fitted

Connections:
AGND: Rfold.2
SENSE_FOLD: Rfold.1, TP_SENSE_FOLD.1, TP_SENSE_FOLDb.1
XA0: TP_XA0.1, TP_XA0b.1
XA63: TP_XA63.1, TP_XA63b.1
XB0: TP_XB0.1, TP_XB0b.1
XB63: TP_XB63.1, TP_XB63b.1
YA0: TP_YA0.1, TP_YA0b.1
YA63: TP_YA63.1, TP_YA63b.1
YA65: TP_YA65.1, TP_YA65b.1
YA66: TP_YA66.1, TP_YA66b.1
YB0: TP_YB0.1, TP_YB0b.1
YB63: TP_YB63.1, TP_YB63b.1
YB65: TP_YB65.1, TP_YB65b.1
YB66: TP_YB66.1, TP_YB66b.1

Notes on the sheet:
Interface only — no 4096 core symbols. Weave proven by AST + L3 SIL.
REQ-ICD-FOLD: YA66=YB65=SENSE_FOLD; 10k soft bias to AGND
XA[0..63]
XB[0..63]
YA[0..63]
YB[0..63]
YA66 ≡ YB65 ≡ SENSE_FOLD (external jumper)
