fractalclockwork/core-memory-redux/kicad/driver_64x64/steer_octal_X_g1.kicad_sch

## KiCad design kicad/driver_64x64/steer_octal_X_g1.kicad_sch (2026-10-05)

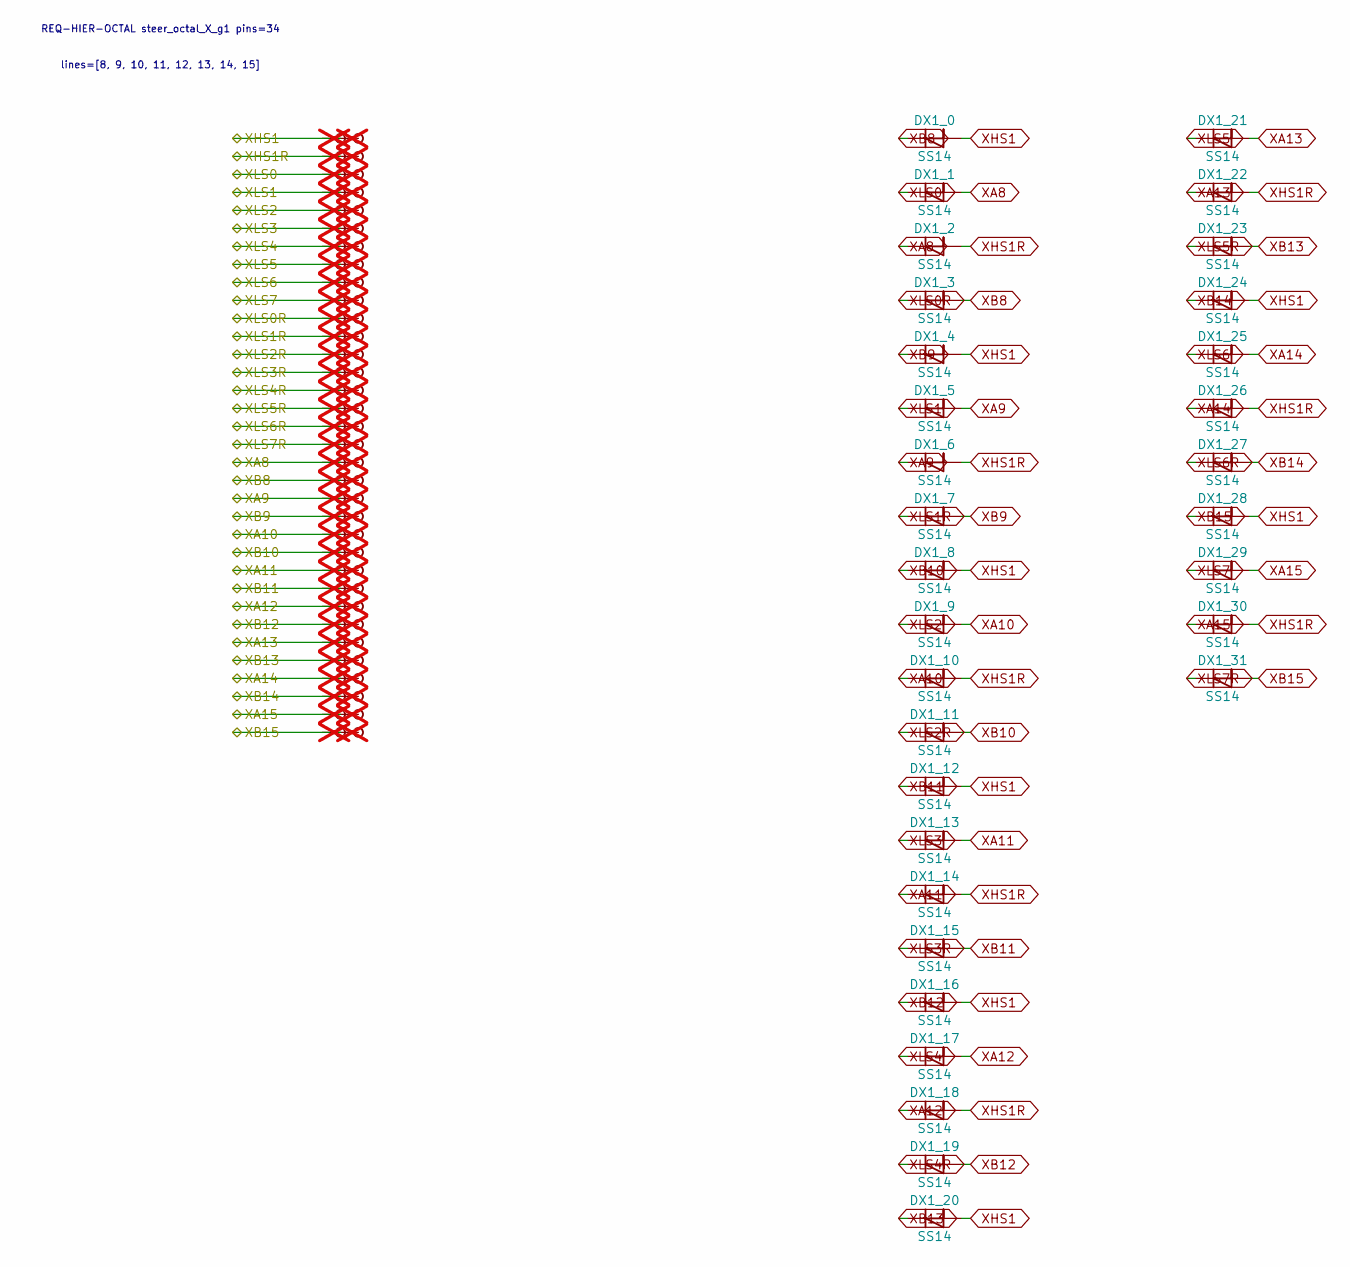
[picture p31: schematic steer_octal_X_g1.kicad_sch]

Parts:
DX1_0, DX1_1, DX1_2, DX1_3, DX1_4, DX1_5, DX1_6, DX1_7, DX1_8, DX1_9, DX1_10, DX1_11, DX1_12, DX1_13, DX1_14, DX1_15, DX1_16, DX1_17, DX1_18, DX1_19, DX1_20, DX1_21, DX1_22, DX1_23, DX1_24, DX1_25, DX1_26, DX1_27, DX1_28, DX1_29, DX1_30, DX1_31: SS14; D_SMA
TP_XA8, TP_XA8b, TP_XA9, TP_XA9b, TP_XA10, TP_XA10b, TP_XA11, TP_XA11b, TP_XA12, TP_XA12b, TP_XA13, TP_XA13b, TP_XA14, TP_XA14b, TP_XA15, TP_XA15b: Stub; not fitted
TP_XB8, TP_XB8b, TP_XB9, TP_XB9b, TP_XB10, TP_XB10b, TP_XB11, TP_XB11b, TP_XB12, TP_XB12b, TP_XB13, TP_XB13b, TP_XB14, TP_XB14b, TP_XB15, TP_XB15b: Stub; not fitted
TP_XHS1, TP_XHS1R, TP_XHS1Rb, TP_XHS1b: Stub; not fitted
TP_XLS0, TP_XLS0R, TP_XLS0Rb, TP_XLS0b, TP_XLS1, TP_XLS1R, TP_XLS1Rb, TP_XLS1b, TP_XLS2, TP_XLS2R, TP_XLS2Rb, TP_XLS2b, TP_XLS3, TP_XLS3R, TP_XLS3Rb, TP_XLS3b, TP_XLS4, TP_XLS4R, TP_XLS4Rb, TP_XLS4b, TP_XLS5, TP_XLS5R, TP_XLS5Rb, TP_XLS5b, TP_XLS6, TP_XLS6R, TP_XLS6Rb, TP_XLS6b, TP_XLS7, TP_XLS7R, TP_XLS7Rb, TP_XLS7b: Stub; not fitted

Connections:
XA8: DX1_1.2 (A), DX1_2.1 (K), TP_XA8.1, TP_XA8b.1
XA9: DX1_5.2 (A), DX1_6.1 (K), TP_XA9.1, TP_XA9b.1
XA10: DX1_9.2 (A), DX1_10.1 (K), TP_XA10.1, TP_XA10b.1
XA11: DX1_13.2 (A), DX1_14.1 (K), TP_XA11.1, TP_XA11b.1
XA12: DX1_17.2 (A), DX1_18.1 (K), TP_XA12.1, TP_XA12b.1
XA13: DX1_21.2 (A), DX1_22.1 (K), TP_XA13.1, TP_XA13b.1
XA14: DX1_25.2 (A), DX1_26.1 (K), TP_XA14.1, TP_XA14b.1
XA15: DX1_29.2 (A), DX1_30.1 (K), TP_XA15.1, TP_XA15b.1
XB8: DX1_0.1 (K), DX1_3.2 (A), TP_XB8.1, TP_XB8b.1
XB9: DX1_4.1 (K), DX1_7.2 (A), TP_XB9.1, TP_XB9b.1
XB10: DX1_8.1 (K), DX1_11.2 (A), TP_XB10.1, TP_XB10b.1
XB11: DX1_12.1 (K), DX1_15.2 (A), TP_XB11.1, TP_XB11b.1
XB12: DX1_16.1 (K), DX1_19.2 (A), TP_XB12.1, TP_XB12b.1
XB13: DX1_20.1 (K), DX1_23.2 (A), TP_XB13.1, TP_XB13b.1
XB14: DX1_24.1 (K), DX1_27.2 (A), TP_XB14.1, TP_XB14b.1
XB15: DX1_28.1 (K), DX1_31.2 (A), TP_XB15.1, TP_XB15b.1
XHS1: DX1_0.2 (A), DX1_4.2 (A), DX1_8.2 (A), DX1_12.2 (A), DX1_16.2 (A), DX1_20.2 (A), DX1_24.2 (A), DX1_28.2 (A), TP_XHS1.1, TP_XHS1b.1
XHS1R: DX1_2.2 (A), DX1_6.2 (A), DX1_10.2 (A), DX1_14.2 (A), DX1_18.2 (A), DX1_22.2 (A), DX1_26.2 (A), DX1_30.2 (A), TP_XHS1R.1, TP_XHS1Rb.1
XLS0: DX1_1.1 (K), TP_XLS0.1, TP_XLS0b.1
XLS0R: DX1_3.1 (K), TP_XLS0R.1, TP_XLS0Rb.1
XLS1: DX1_5.1 (K), TP_XLS1.1, TP_XLS1b.1
XLS1R: DX1_7.1 (K), TP_XLS1R.1, TP_XLS1Rb.1
XLS2: DX1_9.1 (K), TP_XLS2.1, TP_XLS2b.1
XLS2R: DX1_11.1 (K), TP_XLS2R.1, TP_XLS2Rb.1
XLS3: DX1_13.1 (K), TP_XLS3.1, TP_XLS3b.1
XLS3R: DX1_15.1 (K), TP_XLS3R.1, TP_XLS3Rb.1
XLS4: DX1_17.1 (K), TP_XLS4.1, TP_XLS4b.1
XLS4R: DX1_19.1 (K), TP_XLS4R.1, TP_XLS4Rb.1
XLS5: DX1_21.1 (K), TP_XLS5.1, TP_XLS5b.1
XLS5R: DX1_23.1 (K), TP_XLS5R.1, TP_XLS5Rb.1
XLS6: DX1_25.1 (K), TP_XLS6.1, TP_XLS6b.1
XLS6R: DX1_27.1 (K), TP_XLS6R.1, TP_XLS6Rb.1
XLS7: DX1_29.1 (K), TP_XLS7.1, TP_XLS7b.1
XLS7R: DX1_31.1 (K), TP_XLS7R.1, TP_XLS7Rb.1

Notes on the sheet:
REQ-HIER-OCTAL steer_octal_X_g1 pins=34
lines=[8, 9, 10, 11, 12, 13, 14, 15]
