fractalclockwork/core-memory-redux/kicad/driver_64x64/steer_octal_X_g2.kicad_sch

## KiCad design kicad/driver_64x64/steer_octal_X_g2.kicad_sch (2026-10-05)

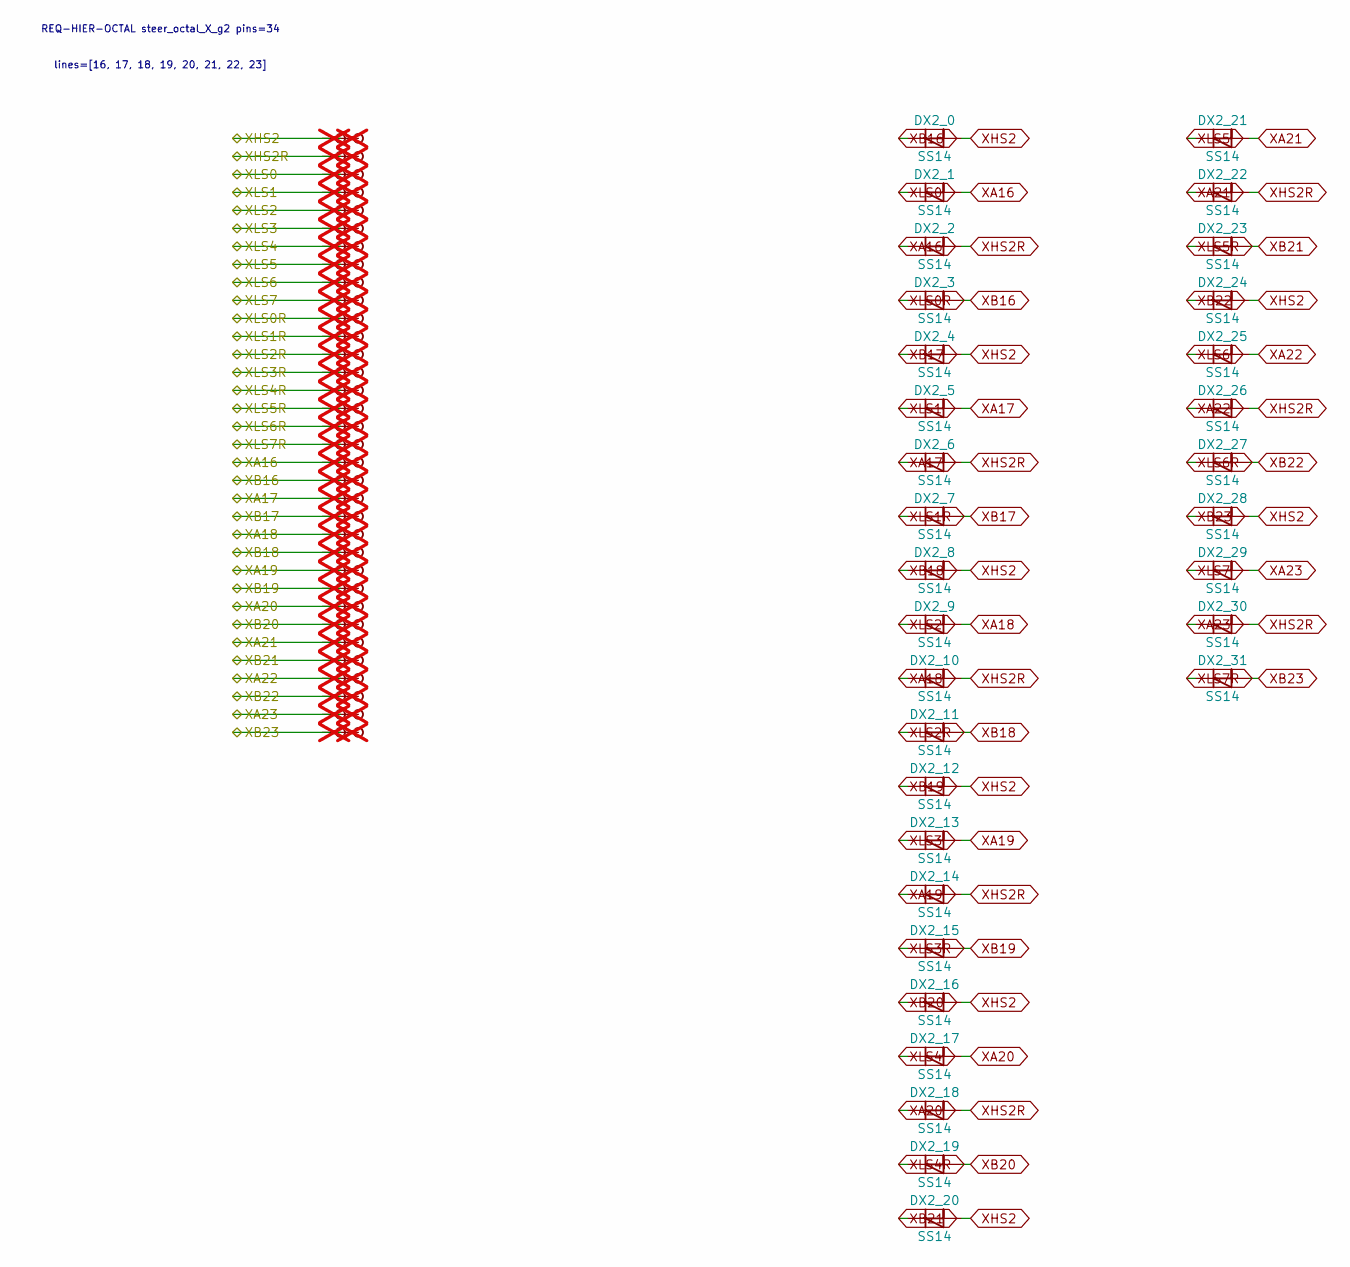
[picture p32: schematic steer_octal_X_g2.kicad_sch]

Parts:
DX2_0, DX2_1, DX2_2, DX2_3, DX2_4, DX2_5, DX2_6, DX2_7, DX2_8, DX2_9, DX2_10, DX2_11, DX2_12, DX2_13, DX2_14, DX2_15, DX2_16, DX2_17, DX2_18, DX2_19, DX2_20, DX2_21, DX2_22, DX2_23, DX2_24, DX2_25, DX2_26, DX2_27, DX2_28, DX2_29, DX2_30, DX2_31: SS14; D_SMA
TP_XA16, TP_XA16b, TP_XA17, TP_XA17b, TP_XA18, TP_XA18b, TP_XA19, TP_XA19b, TP_XA20, TP_XA20b, TP_XA21, TP_XA21b, TP_XA22, TP_XA22b, TP_XA23, TP_XA23b: Stub; not fitted
TP_XB16, TP_XB16b, TP_XB17, TP_XB17b, TP_XB18, TP_XB18b, TP_XB19, TP_XB19b, TP_XB20, TP_XB20b, TP_XB21, TP_XB21b, TP_XB22, TP_XB22b, TP_XB23, TP_XB23b: Stub; not fitted
TP_XHS2, TP_XHS2R, TP_XHS2Rb, TP_XHS2b: Stub; not fitted
TP_XLS0, TP_XLS0R, TP_XLS0Rb, TP_XLS0b, TP_XLS1, TP_XLS1R, TP_XLS1Rb, TP_XLS1b, TP_XLS2, TP_XLS2R, TP_XLS2Rb, TP_XLS2b, TP_XLS3, TP_XLS3R, TP_XLS3Rb, TP_XLS3b, TP_XLS4, TP_XLS4R, TP_XLS4Rb, TP_XLS4b, TP_XLS5, TP_XLS5R, TP_XLS5Rb, TP_XLS5b, TP_XLS6, TP_XLS6R, TP_XLS6Rb, TP_XLS6b, TP_XLS7, TP_XLS7R, TP_XLS7Rb, TP_XLS7b: Stub; not fitted

Connections:
XA16: DX2_1.2 (A), DX2_2.1 (K), TP_XA16.1, TP_XA16b.1
XA17: DX2_5.2 (A), DX2_6.1 (K), TP_XA17.1, TP_XA17b.1
XA18: DX2_9.2 (A), DX2_10.1 (K), TP_XA18.1, TP_XA18b.1
XA19: DX2_13.2 (A), DX2_14.1 (K), TP_XA19.1, TP_XA19b.1
XA20: DX2_17.2 (A), DX2_18.1 (K), TP_XA20.1, TP_XA20b.1
XA21: DX2_21.2 (A), DX2_22.1 (K), TP_XA21.1, TP_XA21b.1
XA22: DX2_25.2 (A), DX2_26.1 (K), TP_XA22.1, TP_XA22b.1
XA23: DX2_29.2 (A), DX2_30.1 (K), TP_XA23.1, TP_XA23b.1
XB16: DX2_0.1 (K), DX2_3.2 (A), TP_XB16.1, TP_XB16b.1
XB17: DX2_4.1 (K), DX2_7.2 (A), TP_XB17.1, TP_XB17b.1
XB18: DX2_8.1 (K), DX2_11.2 (A), TP_XB18.1, TP_XB18b.1
XB19: DX2_12.1 (K), DX2_15.2 (A), TP_XB19.1, TP_XB19b.1
XB20: DX2_16.1 (K), DX2_19.2 (A), TP_XB20.1, TP_XB20b.1
XB21: DX2_20.1 (K), DX2_23.2 (A), TP_XB21.1, TP_XB21b.1
XB22: DX2_24.1 (K), DX2_27.2 (A), TP_XB22.1, TP_XB22b.1
XB23: DX2_28.1 (K), DX2_31.2 (A), TP_XB23.1, TP_XB23b.1
XHS2: DX2_0.2 (A), DX2_4.2 (A), DX2_8.2 (A), DX2_12.2 (A), DX2_16.2 (A), DX2_20.2 (A), DX2_24.2 (A), DX2_28.2 (A), TP_XHS2.1, TP_XHS2b.1
XHS2R: DX2_2.2 (A), DX2_6.2 (A), DX2_10.2 (A), DX2_14.2 (A), DX2_18.2 (A), DX2_22.2 (A), DX2_26.2 (A), DX2_30.2 (A), TP_XHS2R.1, TP_XHS2Rb.1
XLS0: DX2_1.1 (K), TP_XLS0.1, TP_XLS0b.1
XLS0R: DX2_3.1 (K), TP_XLS0R.1, TP_XLS0Rb.1
XLS1: DX2_5.1 (K), TP_XLS1.1, TP_XLS1b.1
XLS1R: DX2_7.1 (K), TP_XLS1R.1, TP_XLS1Rb.1
XLS2: DX2_9.1 (K), TP_XLS2.1, TP_XLS2b.1
XLS2R: DX2_11.1 (K), TP_XLS2R.1, TP_XLS2Rb.1
XLS3: DX2_13.1 (K), TP_XLS3.1, TP_XLS3b.1
XLS3R: DX2_15.1 (K), TP_XLS3R.1, TP_XLS3Rb.1
XLS4: DX2_17.1 (K), TP_XLS4.1, TP_XLS4b.1
XLS4R: DX2_19.1 (K), TP_XLS4R.1, TP_XLS4Rb.1
XLS5: DX2_21.1 (K), TP_XLS5.1, TP_XLS5b.1
XLS5R: DX2_23.1 (K), TP_XLS5R.1, TP_XLS5Rb.1
XLS6: DX2_25.1 (K), TP_XLS6.1, TP_XLS6b.1
XLS6R: DX2_27.1 (K), TP_XLS6R.1, TP_XLS6Rb.1
XLS7: DX2_29.1 (K), TP_XLS7.1, TP_XLS7b.1
XLS7R: DX2_31.1 (K), TP_XLS7R.1, TP_XLS7Rb.1

Notes on the sheet:
REQ-HIER-OCTAL steer_octal_X_g2 pins=34
lines=[16, 17, 18, 19, 20, 21, 22, 23]
