fractalclockwork/core-memory-redux/kicad/driver_64x64/steer_octal_X_g3.kicad_sch

## KiCad design kicad/driver_64x64/steer_octal_X_g3.kicad_sch (2026-10-05)

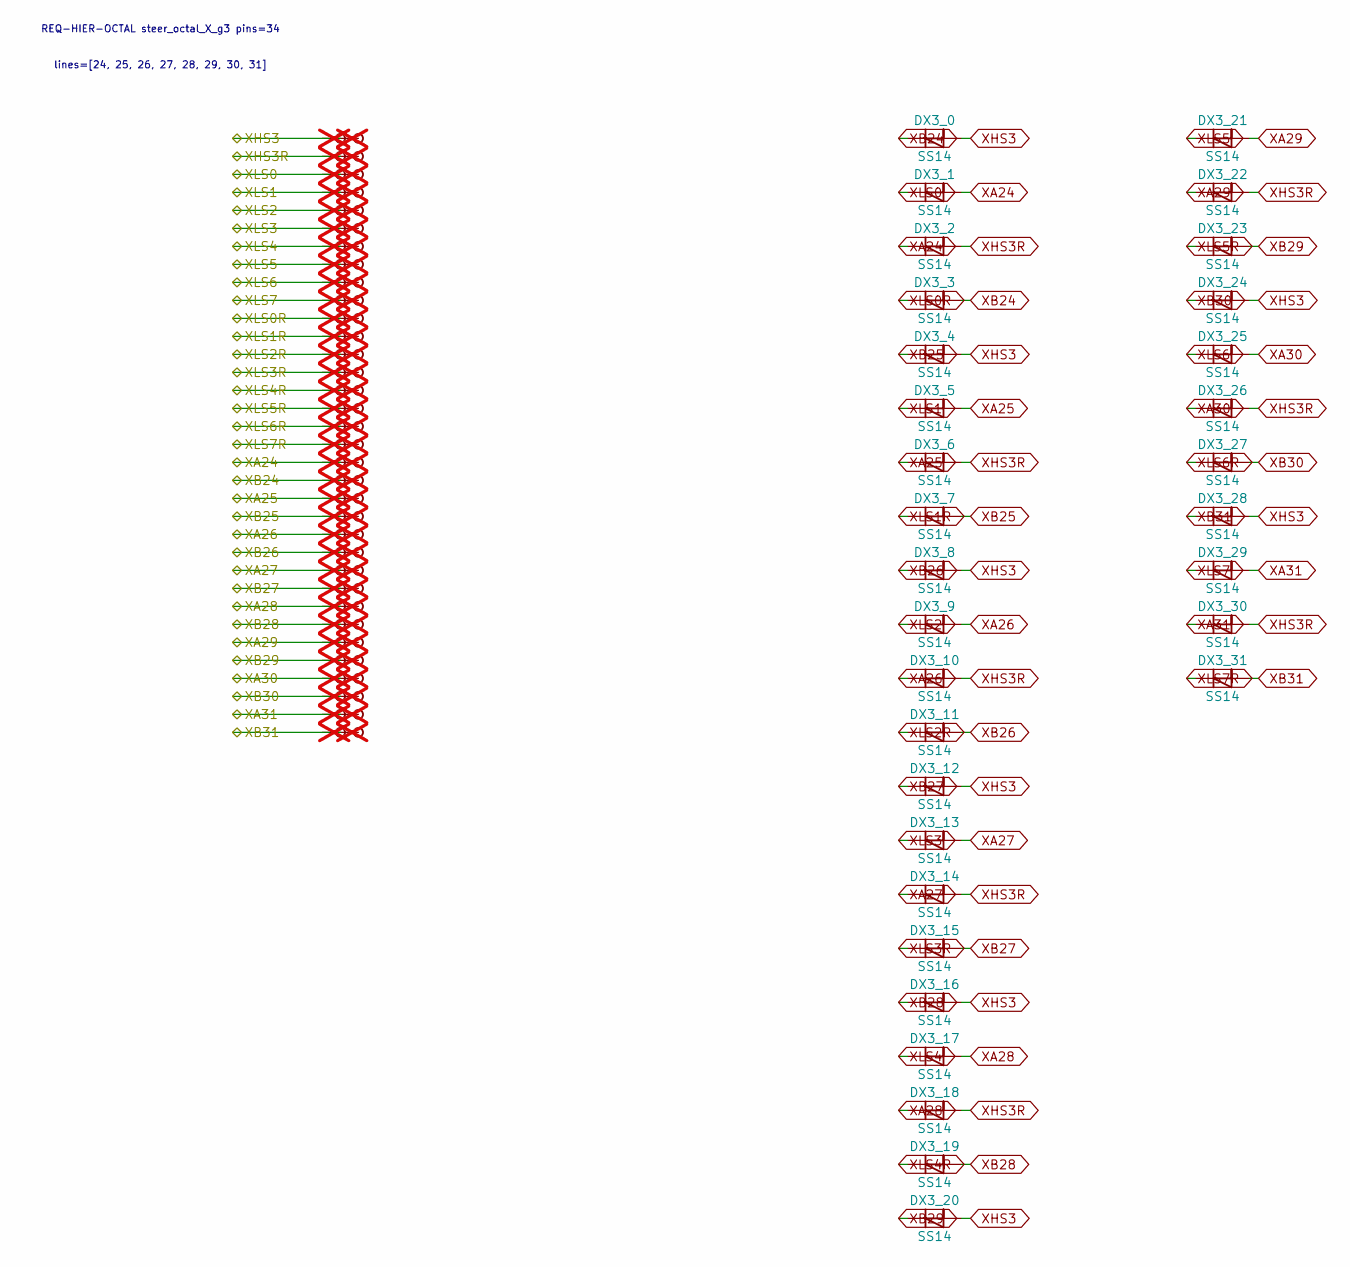
[picture p33: schematic steer_octal_X_g3.kicad_sch]

Parts:
DX3_0, DX3_1, DX3_2, DX3_3, DX3_4, DX3_5, DX3_6, DX3_7, DX3_8, DX3_9, DX3_10, DX3_11, DX3_12, DX3_13, DX3_14, DX3_15, DX3_16, DX3_17, DX3_18, DX3_19, DX3_20, DX3_21, DX3_22, DX3_23, DX3_24, DX3_25, DX3_26, DX3_27, DX3_28, DX3_29, DX3_30, DX3_31: SS14; D_SMA
TP_XA24, TP_XA24b, TP_XA25, TP_XA25b, TP_XA26, TP_XA26b, TP_XA27, TP_XA27b, TP_XA28, TP_XA28b, TP_XA29, TP_XA29b, TP_XA30, TP_XA30b, TP_XA31, TP_XA31b: Stub; not fitted
TP_XB24, TP_XB24b, TP_XB25, TP_XB25b, TP_XB26, TP_XB26b, TP_XB27, TP_XB27b, TP_XB28, TP_XB28b, TP_XB29, TP_XB29b, TP_XB30, TP_XB30b, TP_XB31, TP_XB31b: Stub; not fitted
TP_XHS3, TP_XHS3R, TP_XHS3Rb, TP_XHS3b: Stub; not fitted
TP_XLS0, TP_XLS0R, TP_XLS0Rb, TP_XLS0b, TP_XLS1, TP_XLS1R, TP_XLS1Rb, TP_XLS1b, TP_XLS2, TP_XLS2R, TP_XLS2Rb, TP_XLS2b, TP_XLS3, TP_XLS3R, TP_XLS3Rb, TP_XLS3b, TP_XLS4, TP_XLS4R, TP_XLS4Rb, TP_XLS4b, TP_XLS5, TP_XLS5R, TP_XLS5Rb, TP_XLS5b, TP_XLS6, TP_XLS6R, TP_XLS6Rb, TP_XLS6b, TP_XLS7, TP_XLS7R, TP_XLS7Rb, TP_XLS7b: Stub; not fitted

Connections:
XA24: DX3_1.2 (A), DX3_2.1 (K), TP_XA24.1, TP_XA24b.1
XA25: DX3_5.2 (A), DX3_6.1 (K), TP_XA25.1, TP_XA25b.1
XA26: DX3_9.2 (A), DX3_10.1 (K), TP_XA26.1, TP_XA26b.1
XA27: DX3_13.2 (A), DX3_14.1 (K), TP_XA27.1, TP_XA27b.1
XA28: DX3_17.2 (A), DX3_18.1 (K), TP_XA28.1, TP_XA28b.1
XA29: DX3_21.2 (A), DX3_22.1 (K), TP_XA29.1, TP_XA29b.1
XA30: DX3_25.2 (A), DX3_26.1 (K), TP_XA30.1, TP_XA30b.1
XA31: DX3_29.2 (A), DX3_30.1 (K), TP_XA31.1, TP_XA31b.1
XB24: DX3_0.1 (K), DX3_3.2 (A), TP_XB24.1, TP_XB24b.1
XB25: DX3_4.1 (K), DX3_7.2 (A), TP_XB25.1, TP_XB25b.1
XB26: DX3_8.1 (K), DX3_11.2 (A), TP_XB26.1, TP_XB26b.1
XB27: DX3_12.1 (K), DX3_15.2 (A), TP_XB27.1, TP_XB27b.1
XB28: DX3_16.1 (K), DX3_19.2 (A), TP_XB28.1, TP_XB28b.1
XB29: DX3_20.1 (K), DX3_23.2 (A), TP_XB29.1, TP_XB29b.1
XB30: DX3_24.1 (K), DX3_27.2 (A), TP_XB30.1, TP_XB30b.1
XB31: DX3_28.1 (K), DX3_31.2 (A), TP_XB31.1, TP_XB31b.1
XHS3: DX3_0.2 (A), DX3_4.2 (A), DX3_8.2 (A), DX3_12.2 (A), DX3_16.2 (A), DX3_20.2 (A), DX3_24.2 (A), DX3_28.2 (A), TP_XHS3.1, TP_XHS3b.1
XHS3R: DX3_2.2 (A), DX3_6.2 (A), DX3_10.2 (A), DX3_14.2 (A), DX3_18.2 (A), DX3_22.2 (A), DX3_26.2 (A), DX3_30.2 (A), TP_XHS3R.1, TP_XHS3Rb.1
XLS0: DX3_1.1 (K), TP_XLS0.1, TP_XLS0b.1
XLS0R: DX3_3.1 (K), TP_XLS0R.1, TP_XLS0Rb.1
XLS1: DX3_5.1 (K), TP_XLS1.1, TP_XLS1b.1
XLS1R: DX3_7.1 (K), TP_XLS1R.1, TP_XLS1Rb.1
XLS2: DX3_9.1 (K), TP_XLS2.1, TP_XLS2b.1
XLS2R: DX3_11.1 (K), TP_XLS2R.1, TP_XLS2Rb.1
XLS3: DX3_13.1 (K), TP_XLS3.1, TP_XLS3b.1
XLS3R: DX3_15.1 (K), TP_XLS3R.1, TP_XLS3Rb.1
XLS4: DX3_17.1 (K), TP_XLS4.1, TP_XLS4b.1
XLS4R: DX3_19.1 (K), TP_XLS4R.1, TP_XLS4Rb.1
XLS5: DX3_21.1 (K), TP_XLS5.1, TP_XLS5b.1
XLS5R: DX3_23.1 (K), TP_XLS5R.1, TP_XLS5Rb.1
XLS6: DX3_25.1 (K), TP_XLS6.1, TP_XLS6b.1
XLS6R: DX3_27.1 (K), TP_XLS6R.1, TP_XLS6Rb.1
XLS7: DX3_29.1 (K), TP_XLS7.1, TP_XLS7b.1
XLS7R: DX3_31.1 (K), TP_XLS7R.1, TP_XLS7Rb.1

Notes on the sheet:
REQ-HIER-OCTAL steer_octal_X_g3 pins=34
lines=[24, 25, 26, 27, 28, 29, 30, 31]
