fractalclockwork/core-memory-redux/kicad/driver_64x64/steer_octal_X_g4.kicad_sch

## KiCad design kicad/driver_64x64/steer_octal_X_g4.kicad_sch (2026-10-05)

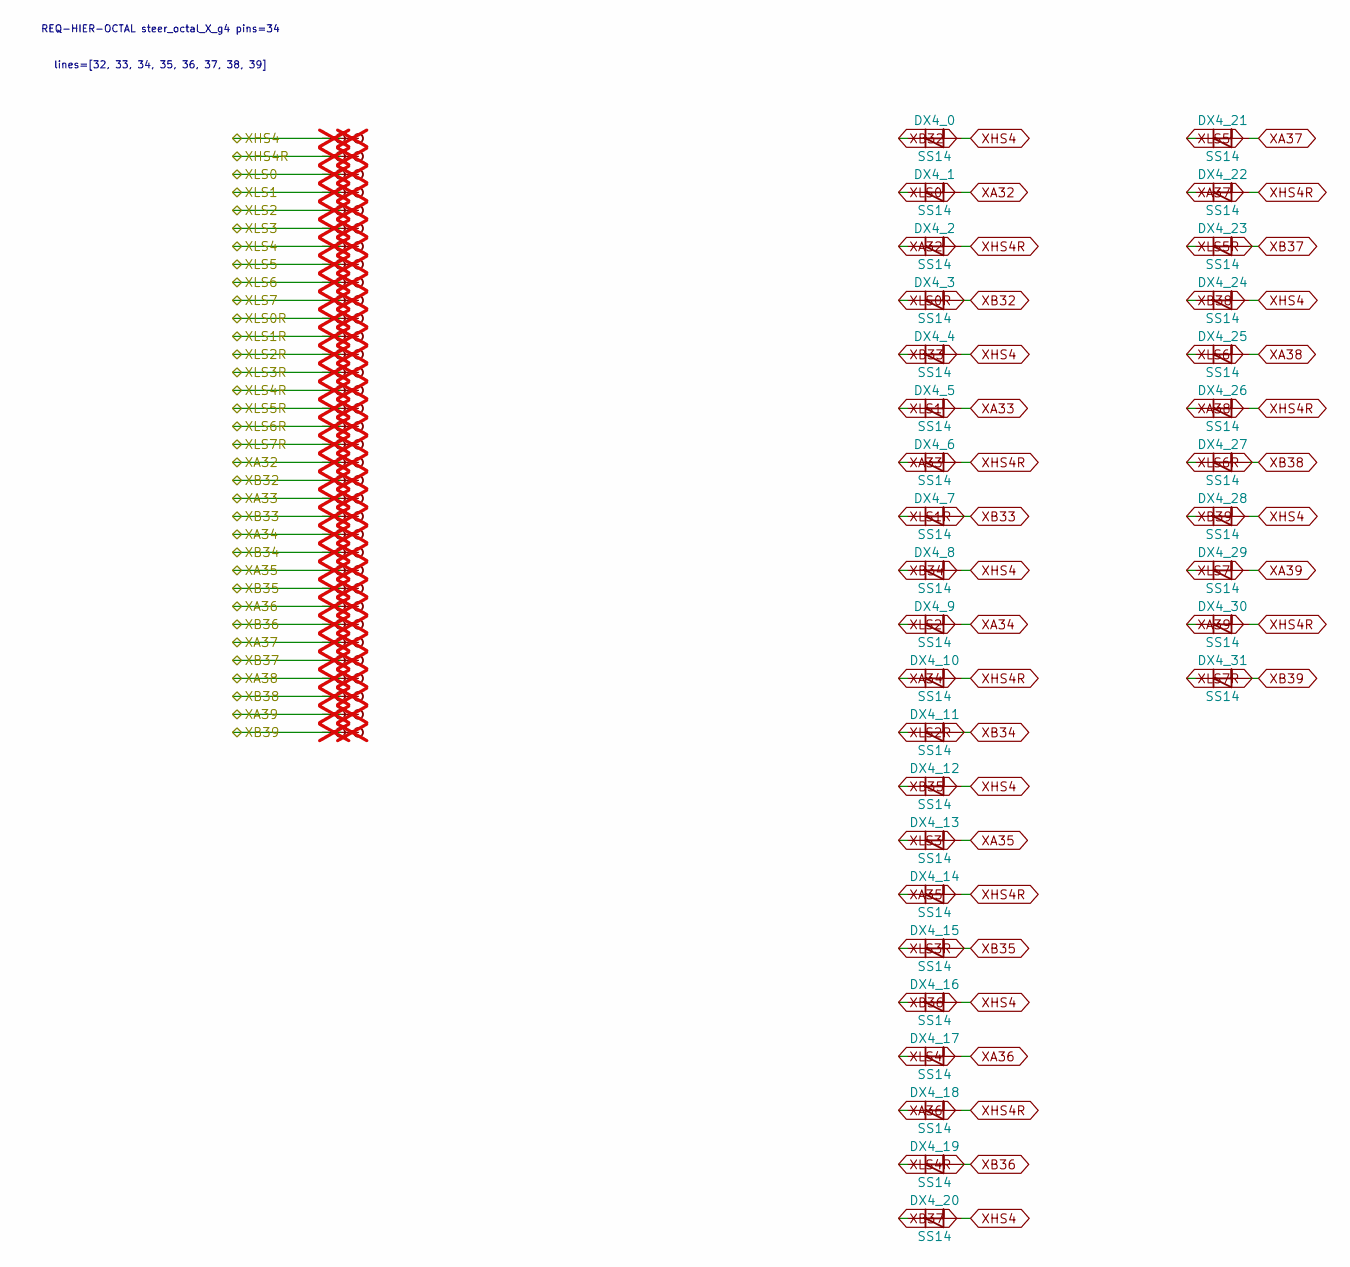
[picture p34: schematic steer_octal_X_g4.kicad_sch]

Parts:
DX4_0, DX4_1, DX4_2, DX4_3, DX4_4, DX4_5, DX4_6, DX4_7, DX4_8, DX4_9, DX4_10, DX4_11, DX4_12, DX4_13, DX4_14, DX4_15, DX4_16, DX4_17, DX4_18, DX4_19, DX4_20, DX4_21, DX4_22, DX4_23, DX4_24, DX4_25, DX4_26, DX4_27, DX4_28, DX4_29, DX4_30, DX4_31: SS14; D_SMA
TP_XA32, TP_XA32b, TP_XA33, TP_XA33b, TP_XA34, TP_XA34b, TP_XA35, TP_XA35b, TP_XA36, TP_XA36b, TP_XA37, TP_XA37b, TP_XA38, TP_XA38b, TP_XA39, TP_XA39b: Stub; not fitted
TP_XB32, TP_XB32b, TP_XB33, TP_XB33b, TP_XB34, TP_XB34b, TP_XB35, TP_XB35b, TP_XB36, TP_XB36b, TP_XB37, TP_XB37b, TP_XB38, TP_XB38b, TP_XB39, TP_XB39b: Stub; not fitted
TP_XHS4, TP_XHS4R, TP_XHS4Rb, TP_XHS4b: Stub; not fitted
TP_XLS0, TP_XLS0R, TP_XLS0Rb, TP_XLS0b, TP_XLS1, TP_XLS1R, TP_XLS1Rb, TP_XLS1b, TP_XLS2, TP_XLS2R, TP_XLS2Rb, TP_XLS2b, TP_XLS3, TP_XLS3R, TP_XLS3Rb, TP_XLS3b, TP_XLS4, TP_XLS4R, TP_XLS4Rb, TP_XLS4b, TP_XLS5, TP_XLS5R, TP_XLS5Rb, TP_XLS5b, TP_XLS6, TP_XLS6R, TP_XLS6Rb, TP_XLS6b, TP_XLS7, TP_XLS7R, TP_XLS7Rb, TP_XLS7b: Stub; not fitted

Connections:
XA32: DX4_1.2 (A), DX4_2.1 (K), TP_XA32.1, TP_XA32b.1
XA33: DX4_5.2 (A), DX4_6.1 (K), TP_XA33.1, TP_XA33b.1
XA34: DX4_9.2 (A), DX4_10.1 (K), TP_XA34.1, TP_XA34b.1
XA35: DX4_13.2 (A), DX4_14.1 (K), TP_XA35.1, TP_XA35b.1
XA36: DX4_17.2 (A), DX4_18.1 (K), TP_XA36.1, TP_XA36b.1
XA37: DX4_21.2 (A), DX4_22.1 (K), TP_XA37.1, TP_XA37b.1
XA38: DX4_25.2 (A), DX4_26.1 (K), TP_XA38.1, TP_XA38b.1
XA39: DX4_29.2 (A), DX4_30.1 (K), TP_XA39.1, TP_XA39b.1
XB32: DX4_0.1 (K), DX4_3.2 (A), TP_XB32.1, TP_XB32b.1
XB33: DX4_4.1 (K), DX4_7.2 (A), TP_XB33.1, TP_XB33b.1
XB34: DX4_8.1 (K), DX4_11.2 (A), TP_XB34.1, TP_XB34b.1
XB35: DX4_12.1 (K), DX4_15.2 (A), TP_XB35.1, TP_XB35b.1
XB36: DX4_16.1 (K), DX4_19.2 (A), TP_XB36.1, TP_XB36b.1
XB37: DX4_20.1 (K), DX4_23.2 (A), TP_XB37.1, TP_XB37b.1
XB38: DX4_24.1 (K), DX4_27.2 (A), TP_XB38.1, TP_XB38b.1
XB39: DX4_28.1 (K), DX4_31.2 (A), TP_XB39.1, TP_XB39b.1
XHS4: DX4_0.2 (A), DX4_4.2 (A), DX4_8.2 (A), DX4_12.2 (A), DX4_16.2 (A), DX4_20.2 (A), DX4_24.2 (A), DX4_28.2 (A), TP_XHS4.1, TP_XHS4b.1
XHS4R: DX4_2.2 (A), DX4_6.2 (A), DX4_10.2 (A), DX4_14.2 (A), DX4_18.2 (A), DX4_22.2 (A), DX4_26.2 (A), DX4_30.2 (A), TP_XHS4R.1, TP_XHS4Rb.1
XLS0: DX4_1.1 (K), TP_XLS0.1, TP_XLS0b.1
XLS0R: DX4_3.1 (K), TP_XLS0R.1, TP_XLS0Rb.1
XLS1: DX4_5.1 (K), TP_XLS1.1, TP_XLS1b.1
XLS1R: DX4_7.1 (K), TP_XLS1R.1, TP_XLS1Rb.1
XLS2: DX4_9.1 (K), TP_XLS2.1, TP_XLS2b.1
XLS2R: DX4_11.1 (K), TP_XLS2R.1, TP_XLS2Rb.1
XLS3: DX4_13.1 (K), TP_XLS3.1, TP_XLS3b.1
XLS3R: DX4_15.1 (K), TP_XLS3R.1, TP_XLS3Rb.1
XLS4: DX4_17.1 (K), TP_XLS4.1, TP_XLS4b.1
XLS4R: DX4_19.1 (K), TP_XLS4R.1, TP_XLS4Rb.1
XLS5: DX4_21.1 (K), TP_XLS5.1, TP_XLS5b.1
XLS5R: DX4_23.1 (K), TP_XLS5R.1, TP_XLS5Rb.1
XLS6: DX4_25.1 (K), TP_XLS6.1, TP_XLS6b.1
XLS6R: DX4_27.1 (K), TP_XLS6R.1, TP_XLS6Rb.1
XLS7: DX4_29.1 (K), TP_XLS7.1, TP_XLS7b.1
XLS7R: DX4_31.1 (K), TP_XLS7R.1, TP_XLS7Rb.1

Notes on the sheet:
REQ-HIER-OCTAL steer_octal_X_g4 pins=34
lines=[32, 33, 34, 35, 36, 37, 38, 39]
