fractalclockwork/core-memory-redux/kicad/driver_64x64/steer_octal_X_g5.kicad_sch

## KiCad design kicad/driver_64x64/steer_octal_X_g5.kicad_sch (2026-10-05)

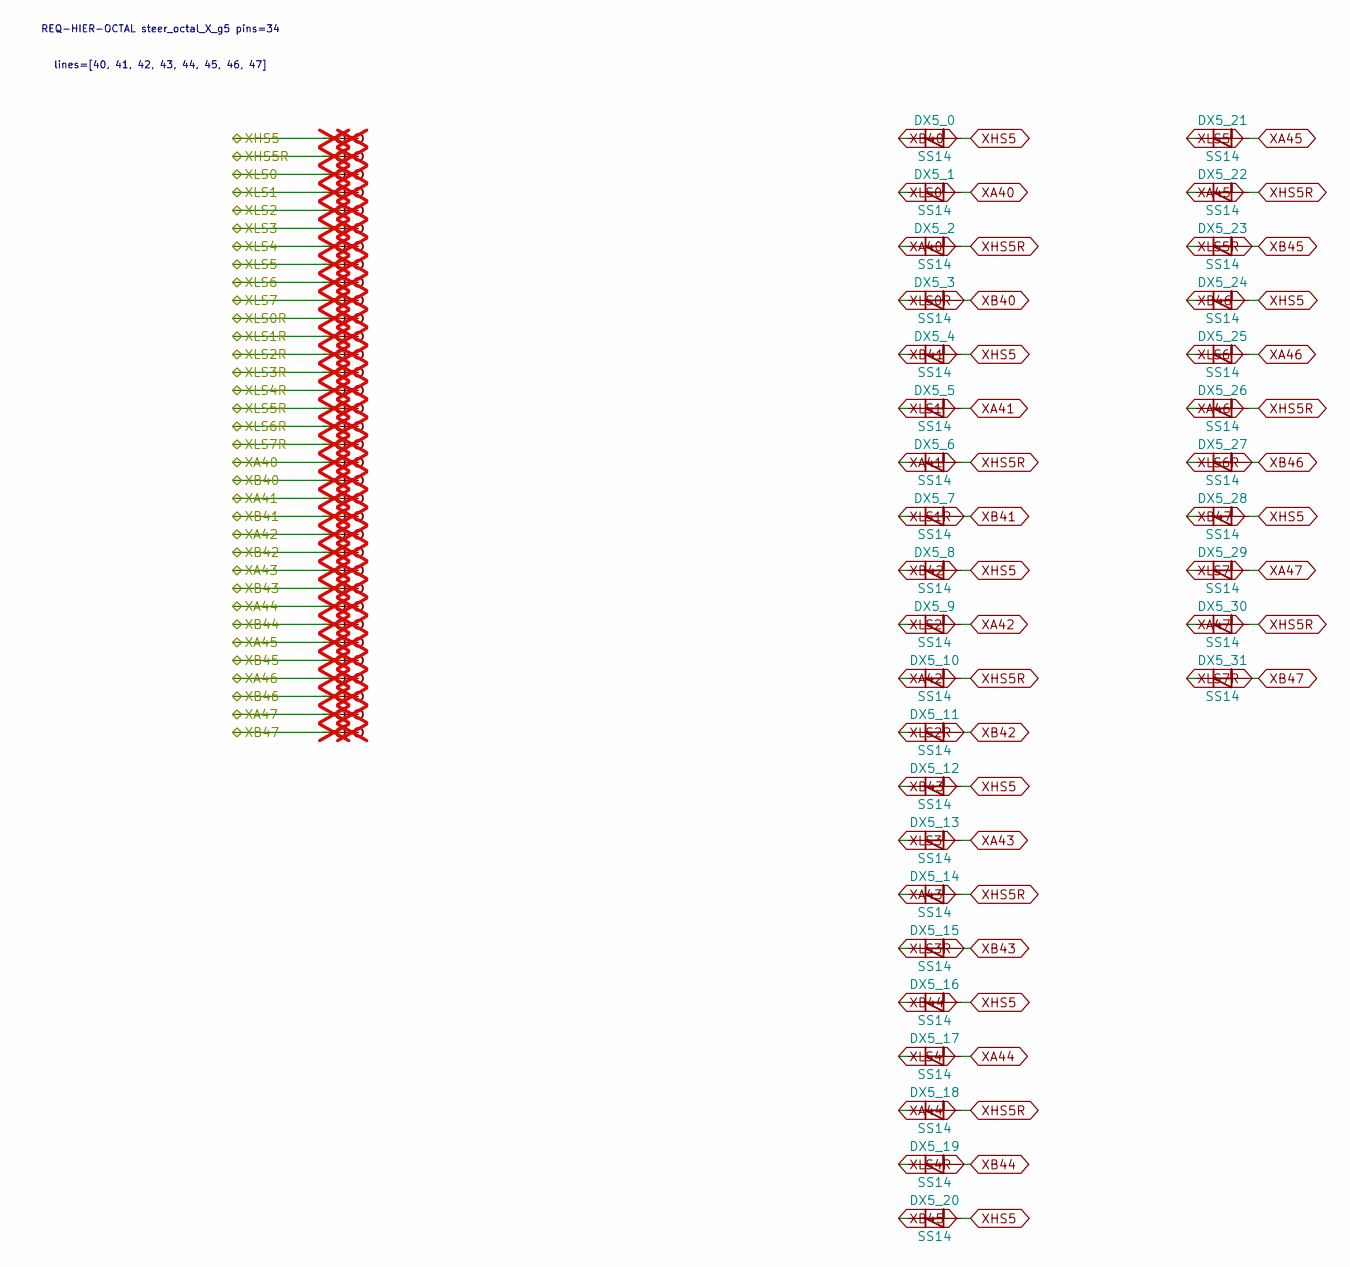
[picture p35: schematic steer_octal_X_g5.kicad_sch]

Parts:
DX5_0, DX5_1, DX5_2, DX5_3, DX5_4, DX5_5, DX5_6, DX5_7, DX5_8, DX5_9, DX5_10, DX5_11, DX5_12, DX5_13, DX5_14, DX5_15, DX5_16, DX5_17, DX5_18, DX5_19, DX5_20, DX5_21, DX5_22, DX5_23, DX5_24, DX5_25, DX5_26, DX5_27, DX5_28, DX5_29, DX5_30, DX5_31: SS14; D_SMA
TP_XA40, TP_XA40b, TP_XA41, TP_XA41b, TP_XA42, TP_XA42b, TP_XA43, TP_XA43b, TP_XA44, TP_XA44b, TP_XA45, TP_XA45b, TP_XA46, TP_XA46b, TP_XA47, TP_XA47b: Stub; not fitted
TP_XB40, TP_XB40b, TP_XB41, TP_XB41b, TP_XB42, TP_XB42b, TP_XB43, TP_XB43b, TP_XB44, TP_XB44b, TP_XB45, TP_XB45b, TP_XB46, TP_XB46b, TP_XB47, TP_XB47b: Stub; not fitted
TP_XHS5, TP_XHS5R, TP_XHS5Rb, TP_XHS5b: Stub; not fitted
TP_XLS0, TP_XLS0R, TP_XLS0Rb, TP_XLS0b, TP_XLS1, TP_XLS1R, TP_XLS1Rb, TP_XLS1b, TP_XLS2, TP_XLS2R, TP_XLS2Rb, TP_XLS2b, TP_XLS3, TP_XLS3R, TP_XLS3Rb, TP_XLS3b, TP_XLS4, TP_XLS4R, TP_XLS4Rb, TP_XLS4b, TP_XLS5, TP_XLS5R, TP_XLS5Rb, TP_XLS5b, TP_XLS6, TP_XLS6R, TP_XLS6Rb, TP_XLS6b, TP_XLS7, TP_XLS7R, TP_XLS7Rb, TP_XLS7b: Stub; not fitted

Connections:
XA40: DX5_1.2 (A), DX5_2.1 (K), TP_XA40.1, TP_XA40b.1
XA41: DX5_5.2 (A), DX5_6.1 (K), TP_XA41.1, TP_XA41b.1
XA42: DX5_9.2 (A), DX5_10.1 (K), TP_XA42.1, TP_XA42b.1
XA43: DX5_13.2 (A), DX5_14.1 (K), TP_XA43.1, TP_XA43b.1
XA44: DX5_17.2 (A), DX5_18.1 (K), TP_XA44.1, TP_XA44b.1
XA45: DX5_21.2 (A), DX5_22.1 (K), TP_XA45.1, TP_XA45b.1
XA46: DX5_25.2 (A), DX5_26.1 (K), TP_XA46.1, TP_XA46b.1
XA47: DX5_29.2 (A), DX5_30.1 (K), TP_XA47.1, TP_XA47b.1
XB40: DX5_0.1 (K), DX5_3.2 (A), TP_XB40.1, TP_XB40b.1
XB41: DX5_4.1 (K), DX5_7.2 (A), TP_XB41.1, TP_XB41b.1
XB42: DX5_8.1 (K), DX5_11.2 (A), TP_XB42.1, TP_XB42b.1
XB43: DX5_12.1 (K), DX5_15.2 (A), TP_XB43.1, TP_XB43b.1
XB44: DX5_16.1 (K), DX5_19.2 (A), TP_XB44.1, TP_XB44b.1
XB45: DX5_20.1 (K), DX5_23.2 (A), TP_XB45.1, TP_XB45b.1
XB46: DX5_24.1 (K), DX5_27.2 (A), TP_XB46.1, TP_XB46b.1
XB47: DX5_28.1 (K), DX5_31.2 (A), TP_XB47.1, TP_XB47b.1
XHS5: DX5_0.2 (A), DX5_4.2 (A), DX5_8.2 (A), DX5_12.2 (A), DX5_16.2 (A), DX5_20.2 (A), DX5_24.2 (A), DX5_28.2 (A), TP_XHS5.1, TP_XHS5b.1
XHS5R: DX5_2.2 (A), DX5_6.2 (A), DX5_10.2 (A), DX5_14.2 (A), DX5_18.2 (A), DX5_22.2 (A), DX5_26.2 (A), DX5_30.2 (A), TP_XHS5R.1, TP_XHS5Rb.1
XLS0: DX5_1.1 (K), TP_XLS0.1, TP_XLS0b.1
XLS0R: DX5_3.1 (K), TP_XLS0R.1, TP_XLS0Rb.1
XLS1: DX5_5.1 (K), TP_XLS1.1, TP_XLS1b.1
XLS1R: DX5_7.1 (K), TP_XLS1R.1, TP_XLS1Rb.1
XLS2: DX5_9.1 (K), TP_XLS2.1, TP_XLS2b.1
XLS2R: DX5_11.1 (K), TP_XLS2R.1, TP_XLS2Rb.1
XLS3: DX5_13.1 (K), TP_XLS3.1, TP_XLS3b.1
XLS3R: DX5_15.1 (K), TP_XLS3R.1, TP_XLS3Rb.1
XLS4: DX5_17.1 (K), TP_XLS4.1, TP_XLS4b.1
XLS4R: DX5_19.1 (K), TP_XLS4R.1, TP_XLS4Rb.1
XLS5: DX5_21.1 (K), TP_XLS5.1, TP_XLS5b.1
XLS5R: DX5_23.1 (K), TP_XLS5R.1, TP_XLS5Rb.1
XLS6: DX5_25.1 (K), TP_XLS6.1, TP_XLS6b.1
XLS6R: DX5_27.1 (K), TP_XLS6R.1, TP_XLS6Rb.1
XLS7: DX5_29.1 (K), TP_XLS7.1, TP_XLS7b.1
XLS7R: DX5_31.1 (K), TP_XLS7R.1, TP_XLS7Rb.1

Notes on the sheet:
REQ-HIER-OCTAL steer_octal_X_g5 pins=34
lines=[40, 41, 42, 43, 44, 45, 46, 47]
