fractalclockwork/core-memory-redux/kicad/driver_64x64/steer_octal_X_g6.kicad_sch

## KiCad design kicad/driver_64x64/steer_octal_X_g6.kicad_sch (2026-10-05)

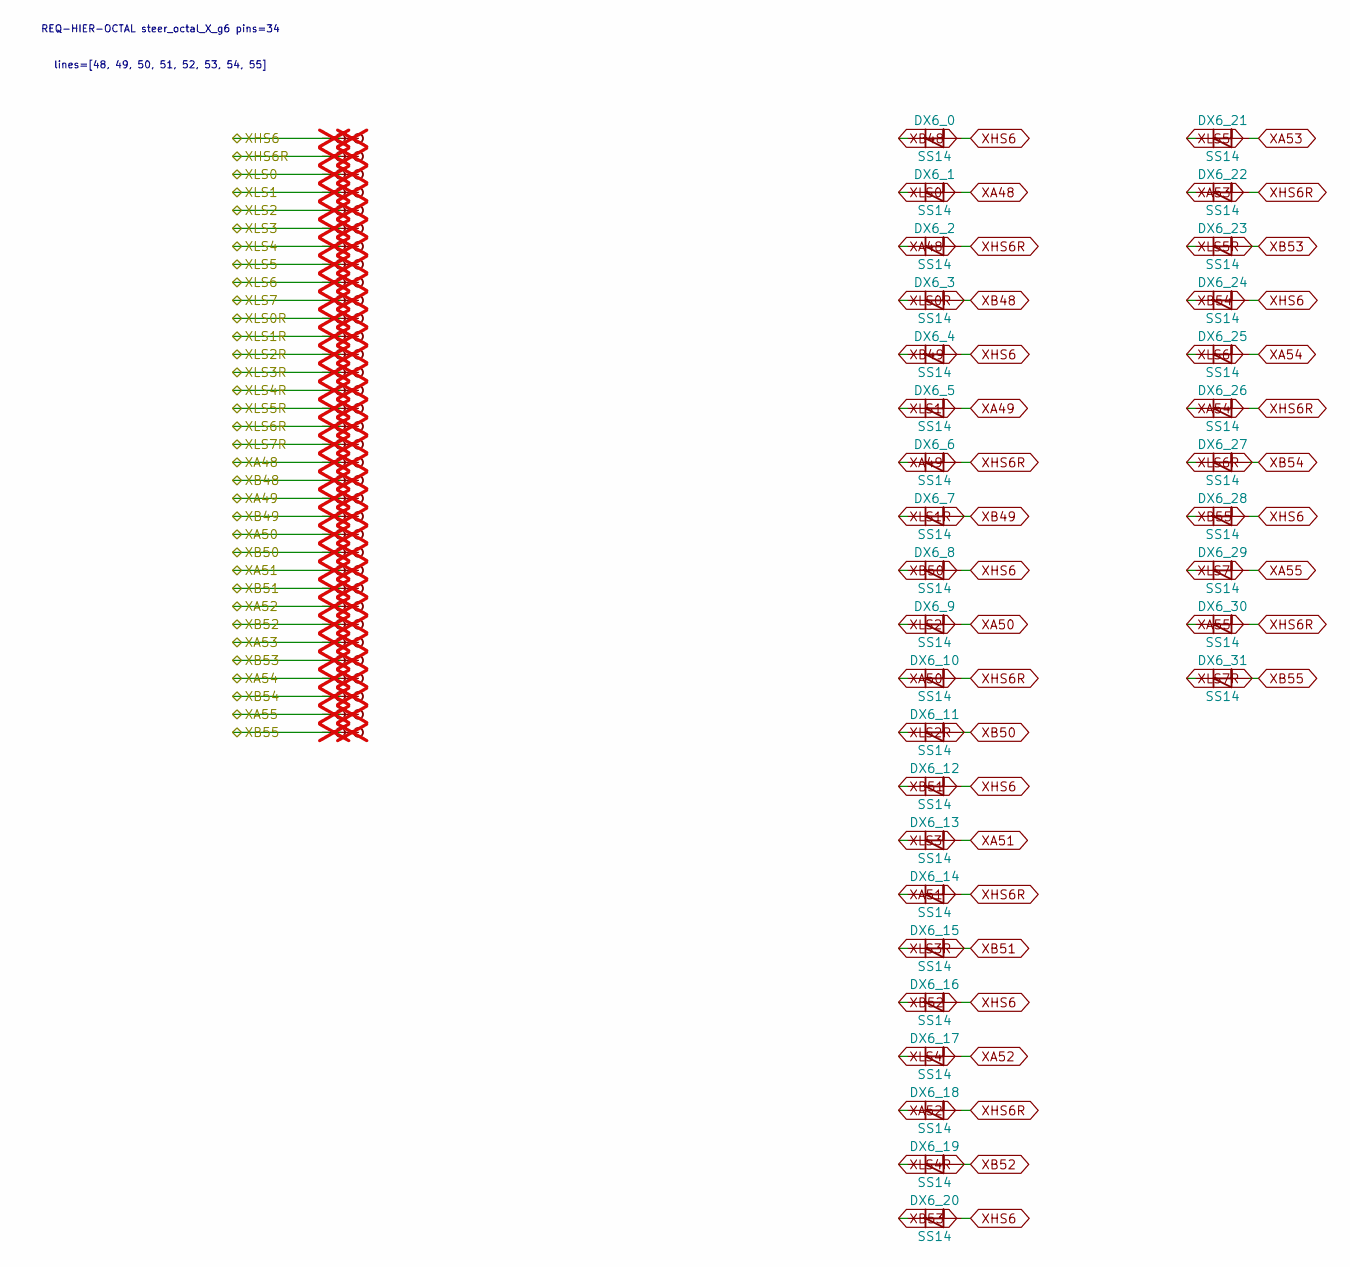
[picture p36: schematic steer_octal_X_g6.kicad_sch]

Parts:
DX6_0, DX6_1, DX6_2, DX6_3, DX6_4, DX6_5, DX6_6, DX6_7, DX6_8, DX6_9, DX6_10, DX6_11, DX6_12, DX6_13, DX6_14, DX6_15, DX6_16, DX6_17, DX6_18, DX6_19, DX6_20, DX6_21, DX6_22, DX6_23, DX6_24, DX6_25, DX6_26, DX6_27, DX6_28, DX6_29, DX6_30, DX6_31: SS14; D_SMA
TP_XA48, TP_XA48b, TP_XA49, TP_XA49b, TP_XA50, TP_XA50b, TP_XA51, TP_XA51b, TP_XA52, TP_XA52b, TP_XA53, TP_XA53b, TP_XA54, TP_XA54b, TP_XA55, TP_XA55b: Stub; not fitted
TP_XB48, TP_XB48b, TP_XB49, TP_XB49b, TP_XB50, TP_XB50b, TP_XB51, TP_XB51b, TP_XB52, TP_XB52b, TP_XB53, TP_XB53b, TP_XB54, TP_XB54b, TP_XB55, TP_XB55b: Stub; not fitted
TP_XHS6, TP_XHS6R, TP_XHS6Rb, TP_XHS6b: Stub; not fitted
TP_XLS0, TP_XLS0R, TP_XLS0Rb, TP_XLS0b, TP_XLS1, TP_XLS1R, TP_XLS1Rb, TP_XLS1b, TP_XLS2, TP_XLS2R, TP_XLS2Rb, TP_XLS2b, TP_XLS3, TP_XLS3R, TP_XLS3Rb, TP_XLS3b, TP_XLS4, TP_XLS4R, TP_XLS4Rb, TP_XLS4b, TP_XLS5, TP_XLS5R, TP_XLS5Rb, TP_XLS5b, TP_XLS6, TP_XLS6R, TP_XLS6Rb, TP_XLS6b, TP_XLS7, TP_XLS7R, TP_XLS7Rb, TP_XLS7b: Stub; not fitted

Connections:
XA48: DX6_1.2 (A), DX6_2.1 (K), TP_XA48.1, TP_XA48b.1
XA49: DX6_5.2 (A), DX6_6.1 (K), TP_XA49.1, TP_XA49b.1
XA50: DX6_9.2 (A), DX6_10.1 (K), TP_XA50.1, TP_XA50b.1
XA51: DX6_13.2 (A), DX6_14.1 (K), TP_XA51.1, TP_XA51b.1
XA52: DX6_17.2 (A), DX6_18.1 (K), TP_XA52.1, TP_XA52b.1
XA53: DX6_21.2 (A), DX6_22.1 (K), TP_XA53.1, TP_XA53b.1
XA54: DX6_25.2 (A), DX6_26.1 (K), TP_XA54.1, TP_XA54b.1
XA55: DX6_29.2 (A), DX6_30.1 (K), TP_XA55.1, TP_XA55b.1
XB48: DX6_0.1 (K), DX6_3.2 (A), TP_XB48.1, TP_XB48b.1
XB49: DX6_4.1 (K), DX6_7.2 (A), TP_XB49.1, TP_XB49b.1
XB50: DX6_8.1 (K), DX6_11.2 (A), TP_XB50.1, TP_XB50b.1
XB51: DX6_12.1 (K), DX6_15.2 (A), TP_XB51.1, TP_XB51b.1
XB52: DX6_16.1 (K), DX6_19.2 (A), TP_XB52.1, TP_XB52b.1
XB53: DX6_20.1 (K), DX6_23.2 (A), TP_XB53.1, TP_XB53b.1
XB54: DX6_24.1 (K), DX6_27.2 (A), TP_XB54.1, TP_XB54b.1
XB55: DX6_28.1 (K), DX6_31.2 (A), TP_XB55.1, TP_XB55b.1
XHS6: DX6_0.2 (A), DX6_4.2 (A), DX6_8.2 (A), DX6_12.2 (A), DX6_16.2 (A), DX6_20.2 (A), DX6_24.2 (A), DX6_28.2 (A), TP_XHS6.1, TP_XHS6b.1
XHS6R: DX6_2.2 (A), DX6_6.2 (A), DX6_10.2 (A), DX6_14.2 (A), DX6_18.2 (A), DX6_22.2 (A), DX6_26.2 (A), DX6_30.2 (A), TP_XHS6R.1, TP_XHS6Rb.1
XLS0: DX6_1.1 (K), TP_XLS0.1, TP_XLS0b.1
XLS0R: DX6_3.1 (K), TP_XLS0R.1, TP_XLS0Rb.1
XLS1: DX6_5.1 (K), TP_XLS1.1, TP_XLS1b.1
XLS1R: DX6_7.1 (K), TP_XLS1R.1, TP_XLS1Rb.1
XLS2: DX6_9.1 (K), TP_XLS2.1, TP_XLS2b.1
XLS2R: DX6_11.1 (K), TP_XLS2R.1, TP_XLS2Rb.1
XLS3: DX6_13.1 (K), TP_XLS3.1, TP_XLS3b.1
XLS3R: DX6_15.1 (K), TP_XLS3R.1, TP_XLS3Rb.1
XLS4: DX6_17.1 (K), TP_XLS4.1, TP_XLS4b.1
XLS4R: DX6_19.1 (K), TP_XLS4R.1, TP_XLS4Rb.1
XLS5: DX6_21.1 (K), TP_XLS5.1, TP_XLS5b.1
XLS5R: DX6_23.1 (K), TP_XLS5R.1, TP_XLS5Rb.1
XLS6: DX6_25.1 (K), TP_XLS6.1, TP_XLS6b.1
XLS6R: DX6_27.1 (K), TP_XLS6R.1, TP_XLS6Rb.1
XLS7: DX6_29.1 (K), TP_XLS7.1, TP_XLS7b.1
XLS7R: DX6_31.1 (K), TP_XLS7R.1, TP_XLS7Rb.1

Notes on the sheet:
REQ-HIER-OCTAL steer_octal_X_g6 pins=34
lines=[48, 49, 50, 51, 52, 53, 54, 55]
