fractalclockwork/core-memory-redux/kicad/driver_64x64/steer_octal_X_g7.kicad_sch

## KiCad design kicad/driver_64x64/steer_octal_X_g7.kicad_sch (2026-10-05)

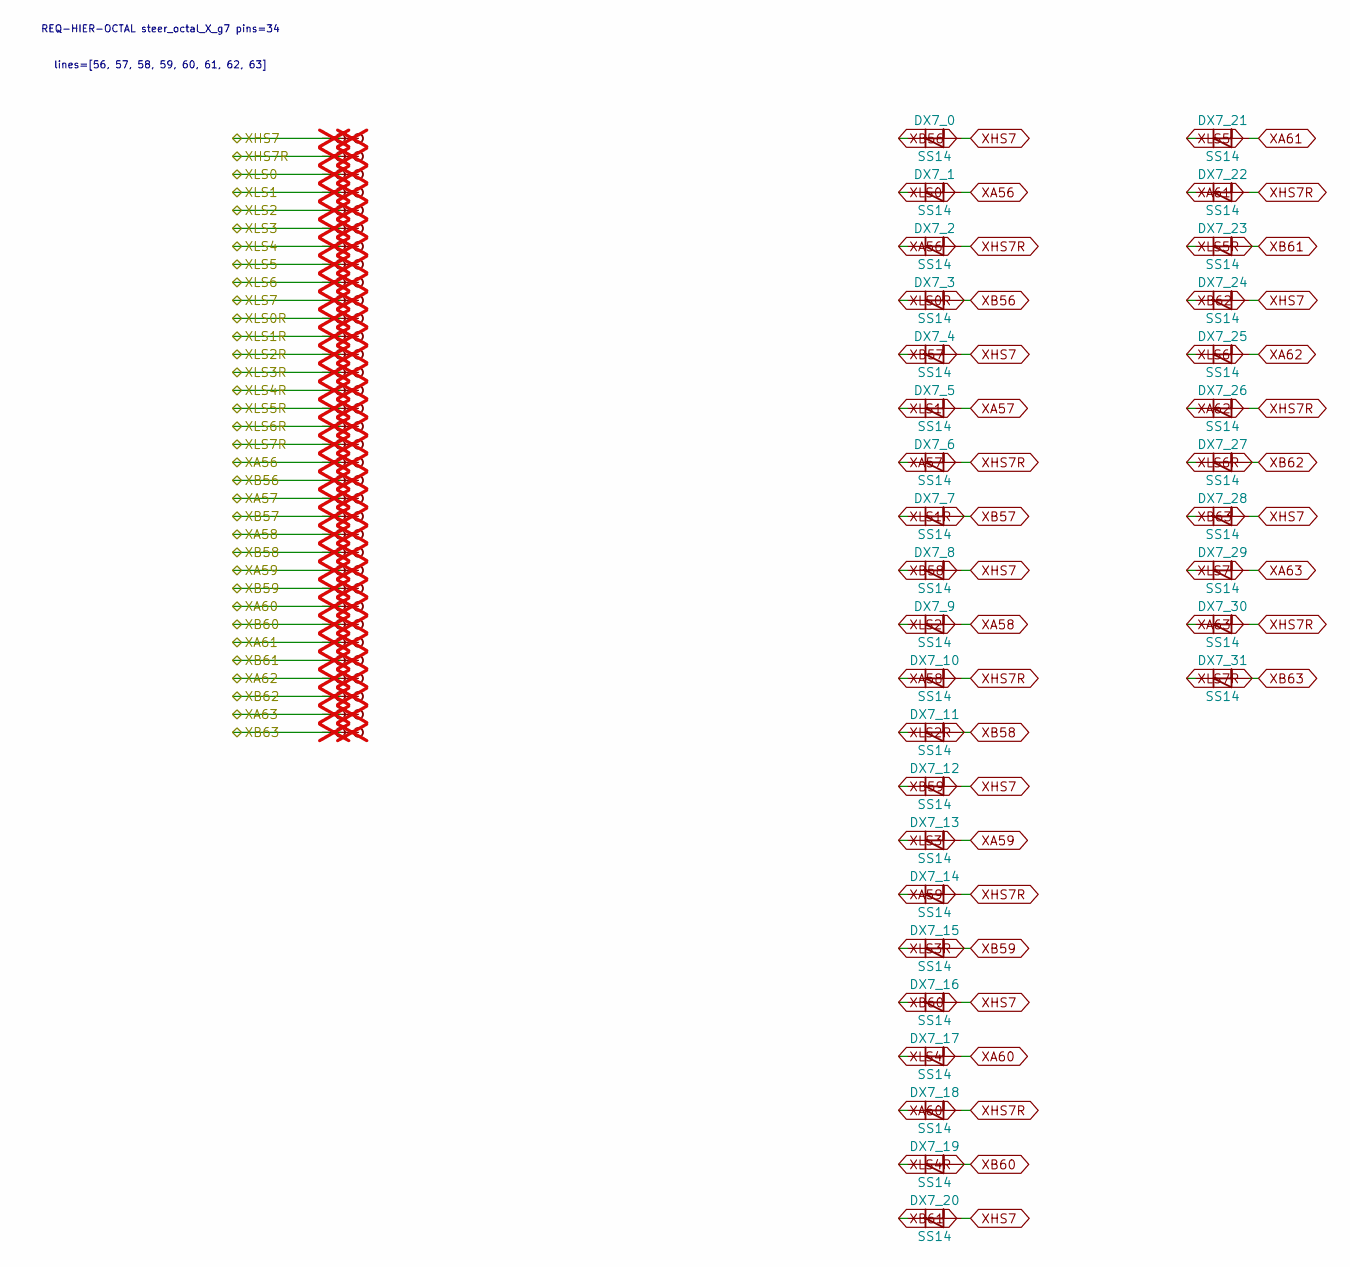
[picture p37: schematic steer_octal_X_g7.kicad_sch]

Parts:
DX7_0, DX7_1, DX7_2, DX7_3, DX7_4, DX7_5, DX7_6, DX7_7, DX7_8, DX7_9, DX7_10, DX7_11, DX7_12, DX7_13, DX7_14, DX7_15, DX7_16, DX7_17, DX7_18, DX7_19, DX7_20, DX7_21, DX7_22, DX7_23, DX7_24, DX7_25, DX7_26, DX7_27, DX7_28, DX7_29, DX7_30, DX7_31: SS14; D_SMA
TP_XA56, TP_XA56b, TP_XA57, TP_XA57b, TP_XA58, TP_XA58b, TP_XA59, TP_XA59b, TP_XA60, TP_XA60b, TP_XA61, TP_XA61b, TP_XA62, TP_XA62b, TP_XA63, TP_XA63b: Stub; not fitted
TP_XB56, TP_XB56b, TP_XB57, TP_XB57b, TP_XB58, TP_XB58b, TP_XB59, TP_XB59b, TP_XB60, TP_XB60b, TP_XB61, TP_XB61b, TP_XB62, TP_XB62b, TP_XB63, TP_XB63b: Stub; not fitted
TP_XHS7, TP_XHS7R, TP_XHS7Rb, TP_XHS7b: Stub; not fitted
TP_XLS0, TP_XLS0R, TP_XLS0Rb, TP_XLS0b, TP_XLS1, TP_XLS1R, TP_XLS1Rb, TP_XLS1b, TP_XLS2, TP_XLS2R, TP_XLS2Rb, TP_XLS2b, TP_XLS3, TP_XLS3R, TP_XLS3Rb, TP_XLS3b, TP_XLS4, TP_XLS4R, TP_XLS4Rb, TP_XLS4b, TP_XLS5, TP_XLS5R, TP_XLS5Rb, TP_XLS5b, TP_XLS6, TP_XLS6R, TP_XLS6Rb, TP_XLS6b, TP_XLS7, TP_XLS7R, TP_XLS7Rb, TP_XLS7b: Stub; not fitted

Connections:
XA56: DX7_1.2 (A), DX7_2.1 (K), TP_XA56.1, TP_XA56b.1
XA57: DX7_5.2 (A), DX7_6.1 (K), TP_XA57.1, TP_XA57b.1
XA58: DX7_9.2 (A), DX7_10.1 (K), TP_XA58.1, TP_XA58b.1
XA59: DX7_13.2 (A), DX7_14.1 (K), TP_XA59.1, TP_XA59b.1
XA60: DX7_17.2 (A), DX7_18.1 (K), TP_XA60.1, TP_XA60b.1
XA61: DX7_21.2 (A), DX7_22.1 (K), TP_XA61.1, TP_XA61b.1
XA62: DX7_25.2 (A), DX7_26.1 (K), TP_XA62.1, TP_XA62b.1
XA63: DX7_29.2 (A), DX7_30.1 (K), TP_XA63.1, TP_XA63b.1
XB56: DX7_0.1 (K), DX7_3.2 (A), TP_XB56.1, TP_XB56b.1
XB57: DX7_4.1 (K), DX7_7.2 (A), TP_XB57.1, TP_XB57b.1
XB58: DX7_8.1 (K), DX7_11.2 (A), TP_XB58.1, TP_XB58b.1
XB59: DX7_12.1 (K), DX7_15.2 (A), TP_XB59.1, TP_XB59b.1
XB60: DX7_16.1 (K), DX7_19.2 (A), TP_XB60.1, TP_XB60b.1
XB61: DX7_20.1 (K), DX7_23.2 (A), TP_XB61.1, TP_XB61b.1
XB62: DX7_24.1 (K), DX7_27.2 (A), TP_XB62.1, TP_XB62b.1
XB63: DX7_28.1 (K), DX7_31.2 (A), TP_XB63.1, TP_XB63b.1
XHS7: DX7_0.2 (A), DX7_4.2 (A), DX7_8.2 (A), DX7_12.2 (A), DX7_16.2 (A), DX7_20.2 (A), DX7_24.2 (A), DX7_28.2 (A), TP_XHS7.1, TP_XHS7b.1
XHS7R: DX7_2.2 (A), DX7_6.2 (A), DX7_10.2 (A), DX7_14.2 (A), DX7_18.2 (A), DX7_22.2 (A), DX7_26.2 (A), DX7_30.2 (A), TP_XHS7R.1, TP_XHS7Rb.1
XLS0: DX7_1.1 (K), TP_XLS0.1, TP_XLS0b.1
XLS0R: DX7_3.1 (K), TP_XLS0R.1, TP_XLS0Rb.1
XLS1: DX7_5.1 (K), TP_XLS1.1, TP_XLS1b.1
XLS1R: DX7_7.1 (K), TP_XLS1R.1, TP_XLS1Rb.1
XLS2: DX7_9.1 (K), TP_XLS2.1, TP_XLS2b.1
XLS2R: DX7_11.1 (K), TP_XLS2R.1, TP_XLS2Rb.1
XLS3: DX7_13.1 (K), TP_XLS3.1, TP_XLS3b.1
XLS3R: DX7_15.1 (K), TP_XLS3R.1, TP_XLS3Rb.1
XLS4: DX7_17.1 (K), TP_XLS4.1, TP_XLS4b.1
XLS4R: DX7_19.1 (K), TP_XLS4R.1, TP_XLS4Rb.1
XLS5: DX7_21.1 (K), TP_XLS5.1, TP_XLS5b.1
XLS5R: DX7_23.1 (K), TP_XLS5R.1, TP_XLS5Rb.1
XLS6: DX7_25.1 (K), TP_XLS6.1, TP_XLS6b.1
XLS6R: DX7_27.1 (K), TP_XLS6R.1, TP_XLS6Rb.1
XLS7: DX7_29.1 (K), TP_XLS7.1, TP_XLS7b.1
XLS7R: DX7_31.1 (K), TP_XLS7R.1, TP_XLS7Rb.1

Notes on the sheet:
REQ-HIER-OCTAL steer_octal_X_g7 pins=34
lines=[56, 57, 58, 59, 60, 61, 62, 63]
