fractalclockwork/core-memory-redux/kicad/driver_64x64/steer_octal_Y_g1.kicad_sch

## KiCad design kicad/driver_64x64/steer_octal_Y_g1.kicad_sch (2026-10-05)

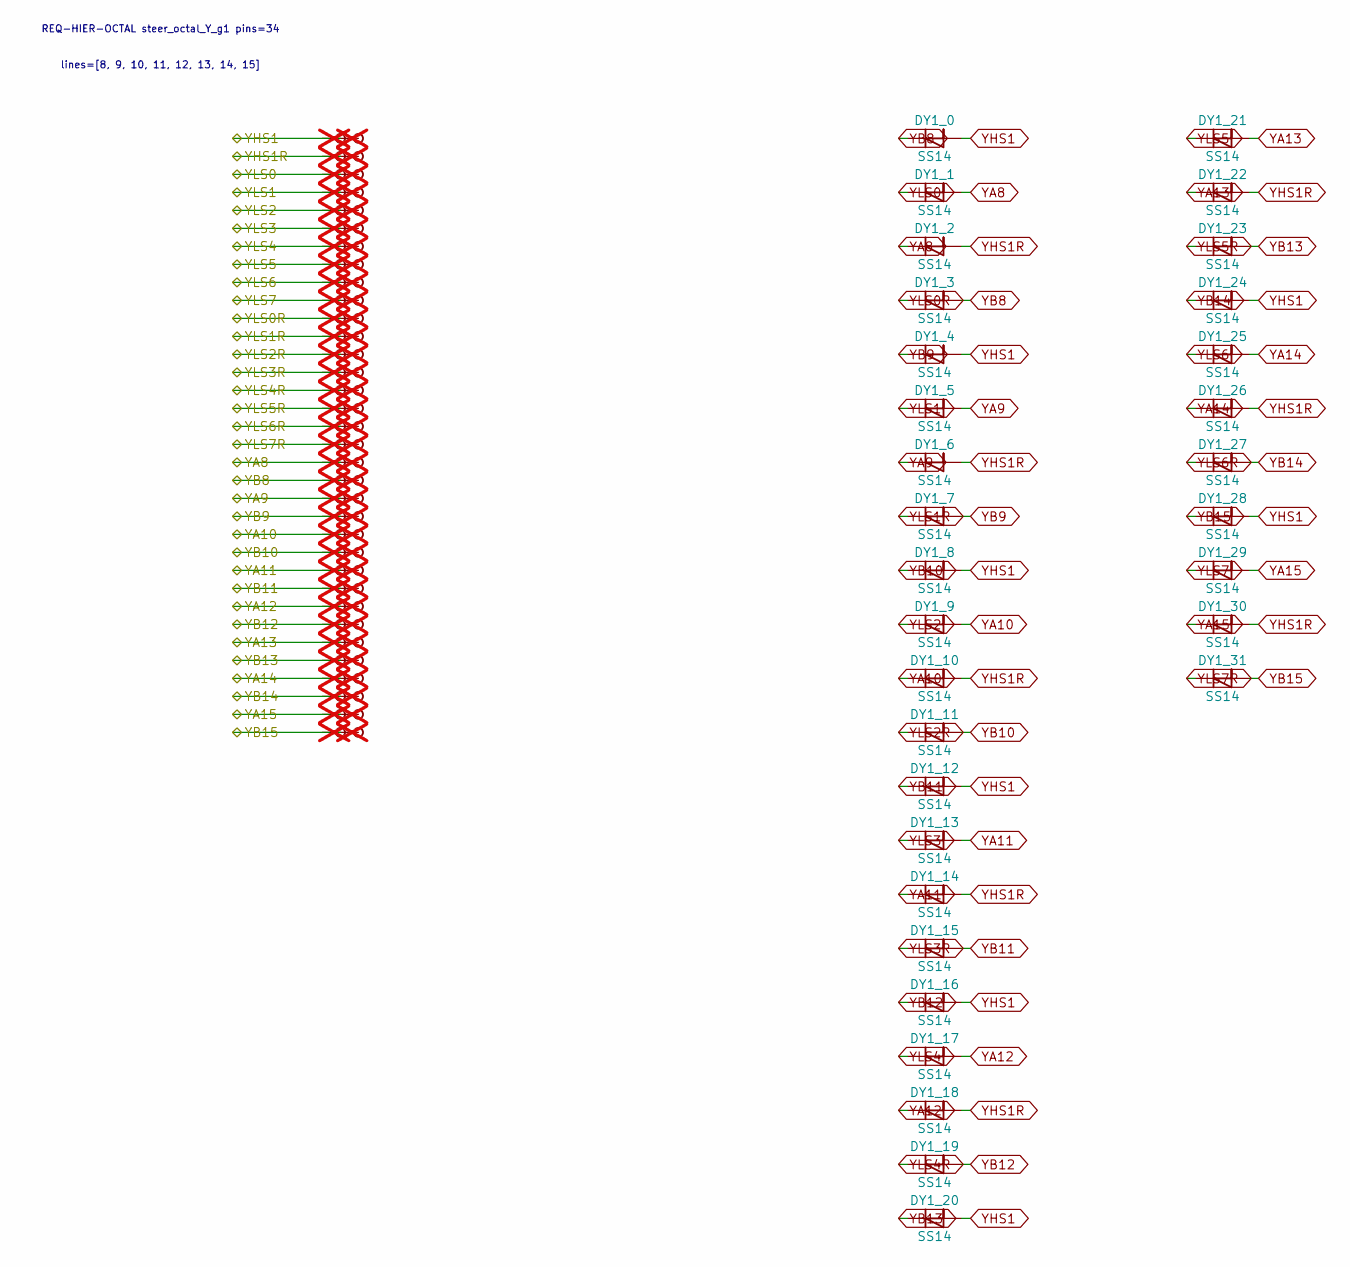
[picture p39: schematic steer_octal_Y_g1.kicad_sch]

Parts:
DY1_0, DY1_1, DY1_2, DY1_3, DY1_4, DY1_5, DY1_6, DY1_7, DY1_8, DY1_9, DY1_10, DY1_11, DY1_12, DY1_13, DY1_14, DY1_15, DY1_16, DY1_17, DY1_18, DY1_19, DY1_20, DY1_21, DY1_22, DY1_23, DY1_24, DY1_25, DY1_26, DY1_27, DY1_28, DY1_29, DY1_30, DY1_31: SS14; D_SMA
TP_YA8, TP_YA8b, TP_YA9, TP_YA9b, TP_YA10, TP_YA10b, TP_YA11, TP_YA11b, TP_YA12, TP_YA12b, TP_YA13, TP_YA13b, TP_YA14, TP_YA14b, TP_YA15, TP_YA15b: Stub; not fitted
TP_YB8, TP_YB8b, TP_YB9, TP_YB9b, TP_YB10, TP_YB10b, TP_YB11, TP_YB11b, TP_YB12, TP_YB12b, TP_YB13, TP_YB13b, TP_YB14, TP_YB14b, TP_YB15, TP_YB15b: Stub; not fitted
TP_YHS1, TP_YHS1R, TP_YHS1Rb, TP_YHS1b: Stub; not fitted
TP_YLS0, TP_YLS0R, TP_YLS0Rb, TP_YLS0b, TP_YLS1, TP_YLS1R, TP_YLS1Rb, TP_YLS1b, TP_YLS2, TP_YLS2R, TP_YLS2Rb, TP_YLS2b, TP_YLS3, TP_YLS3R, TP_YLS3Rb, TP_YLS3b, TP_YLS4, TP_YLS4R, TP_YLS4Rb, TP_YLS4b, TP_YLS5, TP_YLS5R, TP_YLS5Rb, TP_YLS5b, TP_YLS6, TP_YLS6R, TP_YLS6Rb, TP_YLS6b, TP_YLS7, TP_YLS7R, TP_YLS7Rb, TP_YLS7b: Stub; not fitted

Connections:
YA8: DY1_1.2 (A), DY1_2.1 (K), TP_YA8.1, TP_YA8b.1
YA9: DY1_5.2 (A), DY1_6.1 (K), TP_YA9.1, TP_YA9b.1
YA10: DY1_9.2 (A), DY1_10.1 (K), TP_YA10.1, TP_YA10b.1
YA11: DY1_13.2 (A), DY1_14.1 (K), TP_YA11.1, TP_YA11b.1
YA12: DY1_17.2 (A), DY1_18.1 (K), TP_YA12.1, TP_YA12b.1
YA13: DY1_21.2 (A), DY1_22.1 (K), TP_YA13.1, TP_YA13b.1
YA14: DY1_25.2 (A), DY1_26.1 (K), TP_YA14.1, TP_YA14b.1
YA15: DY1_29.2 (A), DY1_30.1 (K), TP_YA15.1, TP_YA15b.1
YB8: DY1_0.1 (K), DY1_3.2 (A), TP_YB8.1, TP_YB8b.1
YB9: DY1_4.1 (K), DY1_7.2 (A), TP_YB9.1, TP_YB9b.1
YB10: DY1_8.1 (K), DY1_11.2 (A), TP_YB10.1, TP_YB10b.1
YB11: DY1_12.1 (K), DY1_15.2 (A), TP_YB11.1, TP_YB11b.1
YB12: DY1_16.1 (K), DY1_19.2 (A), TP_YB12.1, TP_YB12b.1
YB13: DY1_20.1 (K), DY1_23.2 (A), TP_YB13.1, TP_YB13b.1
YB14: DY1_24.1 (K), DY1_27.2 (A), TP_YB14.1, TP_YB14b.1
YB15: DY1_28.1 (K), DY1_31.2 (A), TP_YB15.1, TP_YB15b.1
YHS1: DY1_0.2 (A), DY1_4.2 (A), DY1_8.2 (A), DY1_12.2 (A), DY1_16.2 (A), DY1_20.2 (A), DY1_24.2 (A), DY1_28.2 (A), TP_YHS1.1, TP_YHS1b.1
YHS1R: DY1_2.2 (A), DY1_6.2 (A), DY1_10.2 (A), DY1_14.2 (A), DY1_18.2 (A), DY1_22.2 (A), DY1_26.2 (A), DY1_30.2 (A), TP_YHS1R.1, TP_YHS1Rb.1
YLS0: DY1_1.1 (K), TP_YLS0.1, TP_YLS0b.1
YLS0R: DY1_3.1 (K), TP_YLS0R.1, TP_YLS0Rb.1
YLS1: DY1_5.1 (K), TP_YLS1.1, TP_YLS1b.1
YLS1R: DY1_7.1 (K), TP_YLS1R.1, TP_YLS1Rb.1
YLS2: DY1_9.1 (K), TP_YLS2.1, TP_YLS2b.1
YLS2R: DY1_11.1 (K), TP_YLS2R.1, TP_YLS2Rb.1
YLS3: DY1_13.1 (K), TP_YLS3.1, TP_YLS3b.1
YLS3R: DY1_15.1 (K), TP_YLS3R.1, TP_YLS3Rb.1
YLS4: DY1_17.1 (K), TP_YLS4.1, TP_YLS4b.1
YLS4R: DY1_19.1 (K), TP_YLS4R.1, TP_YLS4Rb.1
YLS5: DY1_21.1 (K), TP_YLS5.1, TP_YLS5b.1
YLS5R: DY1_23.1 (K), TP_YLS5R.1, TP_YLS5Rb.1
YLS6: DY1_25.1 (K), TP_YLS6.1, TP_YLS6b.1
YLS6R: DY1_27.1 (K), TP_YLS6R.1, TP_YLS6Rb.1
YLS7: DY1_29.1 (K), TP_YLS7.1, TP_YLS7b.1
YLS7R: DY1_31.1 (K), TP_YLS7R.1, TP_YLS7Rb.1

Notes on the sheet:
REQ-HIER-OCTAL steer_octal_Y_g1 pins=34
lines=[8, 9, 10, 11, 12, 13, 14, 15]
