fractalclockwork/core-memory-redux/kicad/driver_64x64/steer_octal_Y_g2.kicad_sch

## KiCad design kicad/driver_64x64/steer_octal_Y_g2.kicad_sch (2026-10-05)

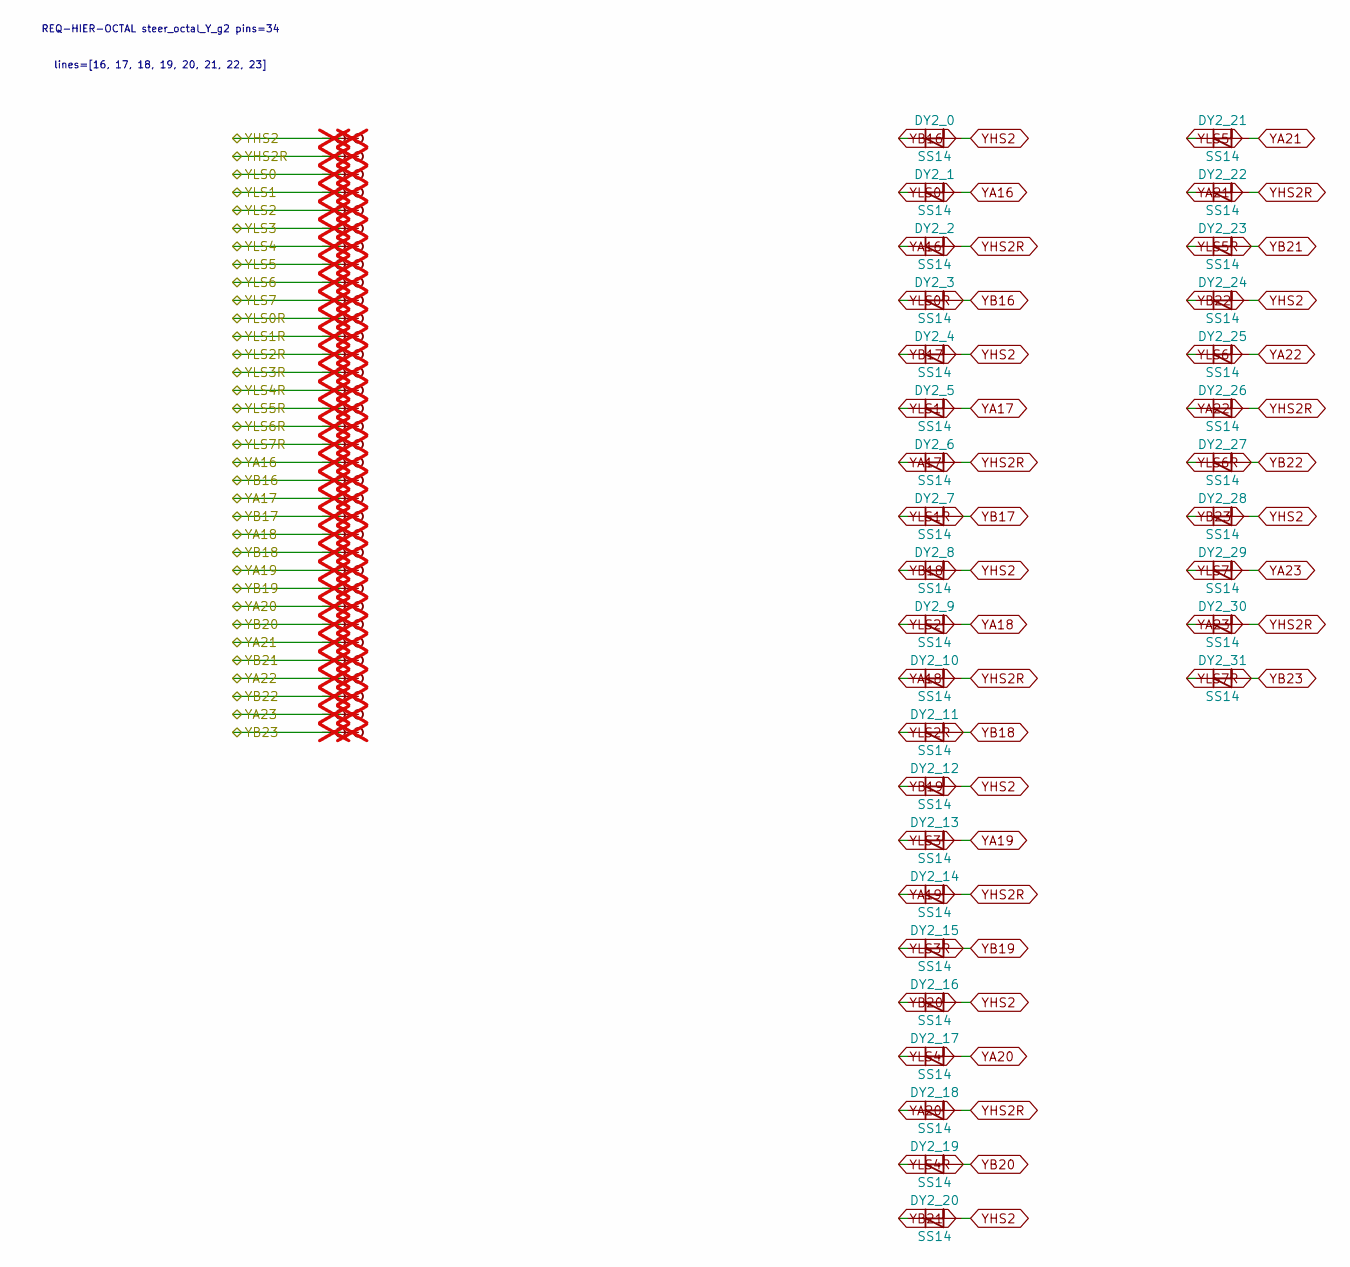
[picture p40: schematic steer_octal_Y_g2.kicad_sch]

Parts:
DY2_0, DY2_1, DY2_2, DY2_3, DY2_4, DY2_5, DY2_6, DY2_7, DY2_8, DY2_9, DY2_10, DY2_11, DY2_12, DY2_13, DY2_14, DY2_15, DY2_16, DY2_17, DY2_18, DY2_19, DY2_20, DY2_21, DY2_22, DY2_23, DY2_24, DY2_25, DY2_26, DY2_27, DY2_28, DY2_29, DY2_30, DY2_31: SS14; D_SMA
TP_YA16, TP_YA16b, TP_YA17, TP_YA17b, TP_YA18, TP_YA18b, TP_YA19, TP_YA19b, TP_YA20, TP_YA20b, TP_YA21, TP_YA21b, TP_YA22, TP_YA22b, TP_YA23, TP_YA23b: Stub; not fitted
TP_YB16, TP_YB16b, TP_YB17, TP_YB17b, TP_YB18, TP_YB18b, TP_YB19, TP_YB19b, TP_YB20, TP_YB20b, TP_YB21, TP_YB21b, TP_YB22, TP_YB22b, TP_YB23, TP_YB23b: Stub; not fitted
TP_YHS2, TP_YHS2R, TP_YHS2Rb, TP_YHS2b: Stub; not fitted
TP_YLS0, TP_YLS0R, TP_YLS0Rb, TP_YLS0b, TP_YLS1, TP_YLS1R, TP_YLS1Rb, TP_YLS1b, TP_YLS2, TP_YLS2R, TP_YLS2Rb, TP_YLS2b, TP_YLS3, TP_YLS3R, TP_YLS3Rb, TP_YLS3b, TP_YLS4, TP_YLS4R, TP_YLS4Rb, TP_YLS4b, TP_YLS5, TP_YLS5R, TP_YLS5Rb, TP_YLS5b, TP_YLS6, TP_YLS6R, TP_YLS6Rb, TP_YLS6b, TP_YLS7, TP_YLS7R, TP_YLS7Rb, TP_YLS7b: Stub; not fitted

Connections:
YA16: DY2_1.2 (A), DY2_2.1 (K), TP_YA16.1, TP_YA16b.1
YA17: DY2_5.2 (A), DY2_6.1 (K), TP_YA17.1, TP_YA17b.1
YA18: DY2_9.2 (A), DY2_10.1 (K), TP_YA18.1, TP_YA18b.1
YA19: DY2_13.2 (A), DY2_14.1 (K), TP_YA19.1, TP_YA19b.1
YA20: DY2_17.2 (A), DY2_18.1 (K), TP_YA20.1, TP_YA20b.1
YA21: DY2_21.2 (A), DY2_22.1 (K), TP_YA21.1, TP_YA21b.1
YA22: DY2_25.2 (A), DY2_26.1 (K), TP_YA22.1, TP_YA22b.1
YA23: DY2_29.2 (A), DY2_30.1 (K), TP_YA23.1, TP_YA23b.1
YB16: DY2_0.1 (K), DY2_3.2 (A), TP_YB16.1, TP_YB16b.1
YB17: DY2_4.1 (K), DY2_7.2 (A), TP_YB17.1, TP_YB17b.1
YB18: DY2_8.1 (K), DY2_11.2 (A), TP_YB18.1, TP_YB18b.1
YB19: DY2_12.1 (K), DY2_15.2 (A), TP_YB19.1, TP_YB19b.1
YB20: DY2_16.1 (K), DY2_19.2 (A), TP_YB20.1, TP_YB20b.1
YB21: DY2_20.1 (K), DY2_23.2 (A), TP_YB21.1, TP_YB21b.1
YB22: DY2_24.1 (K), DY2_27.2 (A), TP_YB22.1, TP_YB22b.1
YB23: DY2_28.1 (K), DY2_31.2 (A), TP_YB23.1, TP_YB23b.1
YHS2: DY2_0.2 (A), DY2_4.2 (A), DY2_8.2 (A), DY2_12.2 (A), DY2_16.2 (A), DY2_20.2 (A), DY2_24.2 (A), DY2_28.2 (A), TP_YHS2.1, TP_YHS2b.1
YHS2R: DY2_2.2 (A), DY2_6.2 (A), DY2_10.2 (A), DY2_14.2 (A), DY2_18.2 (A), DY2_22.2 (A), DY2_26.2 (A), DY2_30.2 (A), TP_YHS2R.1, TP_YHS2Rb.1
YLS0: DY2_1.1 (K), TP_YLS0.1, TP_YLS0b.1
YLS0R: DY2_3.1 (K), TP_YLS0R.1, TP_YLS0Rb.1
YLS1: DY2_5.1 (K), TP_YLS1.1, TP_YLS1b.1
YLS1R: DY2_7.1 (K), TP_YLS1R.1, TP_YLS1Rb.1
YLS2: DY2_9.1 (K), TP_YLS2.1, TP_YLS2b.1
YLS2R: DY2_11.1 (K), TP_YLS2R.1, TP_YLS2Rb.1
YLS3: DY2_13.1 (K), TP_YLS3.1, TP_YLS3b.1
YLS3R: DY2_15.1 (K), TP_YLS3R.1, TP_YLS3Rb.1
YLS4: DY2_17.1 (K), TP_YLS4.1, TP_YLS4b.1
YLS4R: DY2_19.1 (K), TP_YLS4R.1, TP_YLS4Rb.1
YLS5: DY2_21.1 (K), TP_YLS5.1, TP_YLS5b.1
YLS5R: DY2_23.1 (K), TP_YLS5R.1, TP_YLS5Rb.1
YLS6: DY2_25.1 (K), TP_YLS6.1, TP_YLS6b.1
YLS6R: DY2_27.1 (K), TP_YLS6R.1, TP_YLS6Rb.1
YLS7: DY2_29.1 (K), TP_YLS7.1, TP_YLS7b.1
YLS7R: DY2_31.1 (K), TP_YLS7R.1, TP_YLS7Rb.1

Notes on the sheet:
REQ-HIER-OCTAL steer_octal_Y_g2 pins=34
lines=[16, 17, 18, 19, 20, 21, 22, 23]
