fractalclockwork/core-memory-redux/kicad/driver_64x64/steer_octal_Y_g3.kicad_sch

## KiCad design kicad/driver_64x64/steer_octal_Y_g3.kicad_sch (2026-10-05)

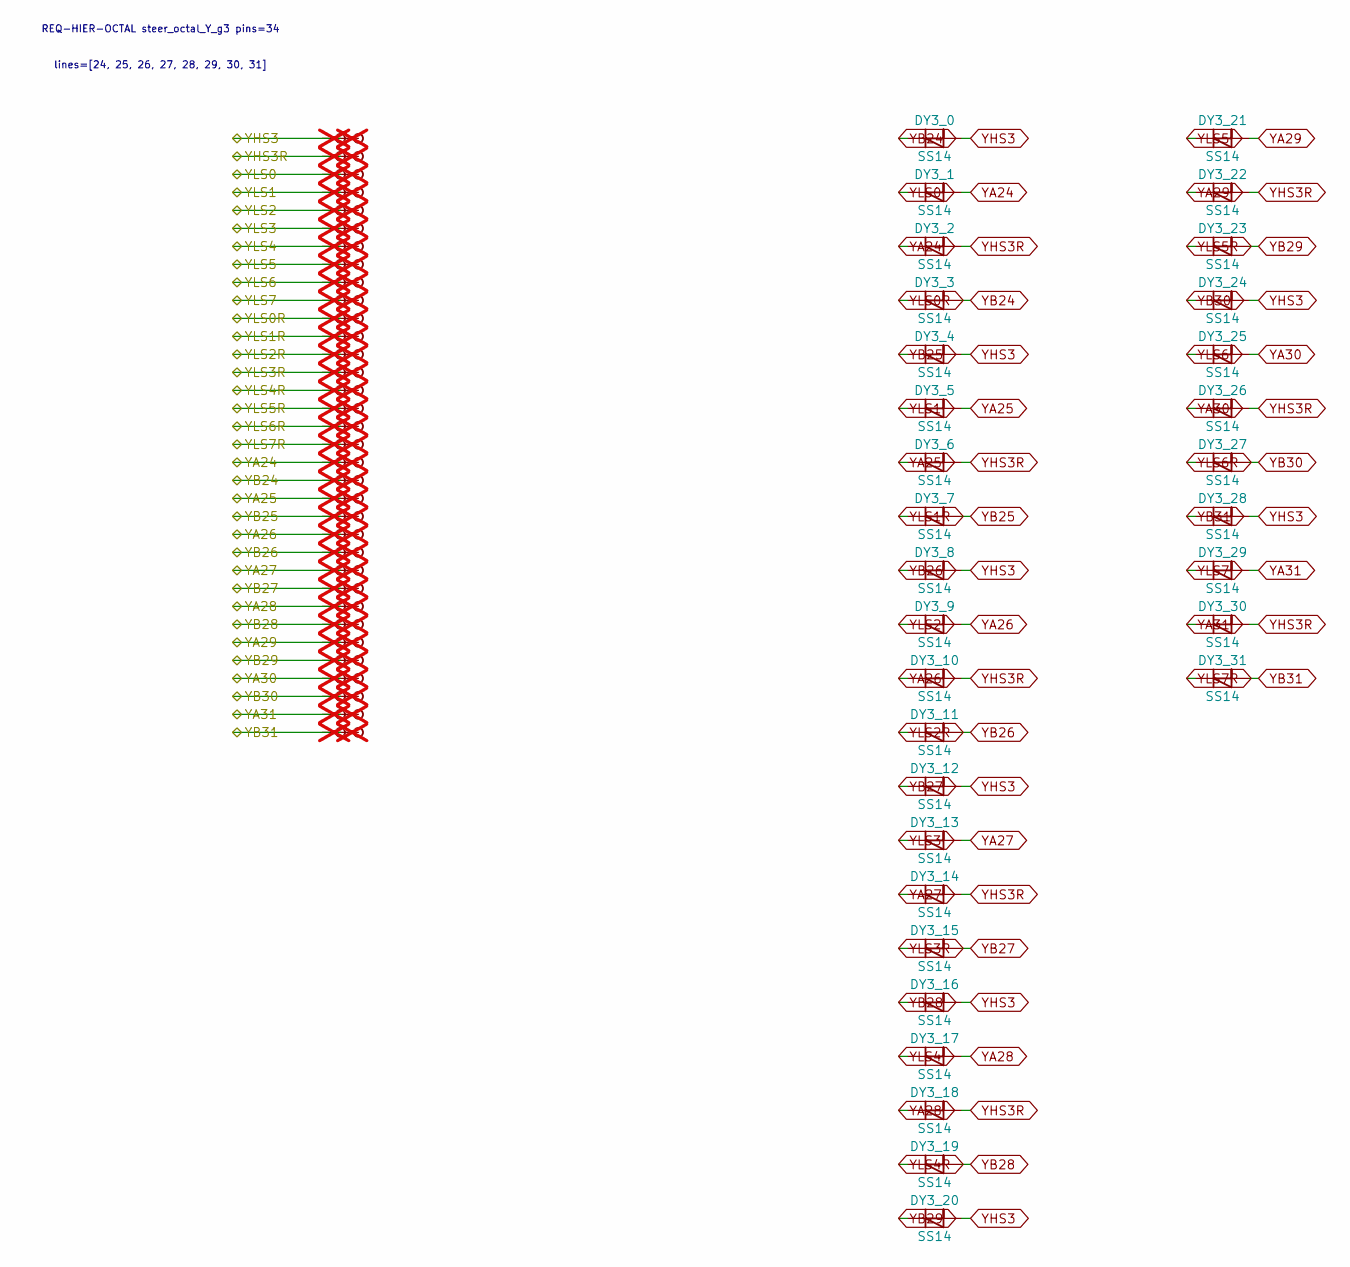
[picture p41: schematic steer_octal_Y_g3.kicad_sch]

Parts:
DY3_0, DY3_1, DY3_2, DY3_3, DY3_4, DY3_5, DY3_6, DY3_7, DY3_8, DY3_9, DY3_10, DY3_11, DY3_12, DY3_13, DY3_14, DY3_15, DY3_16, DY3_17, DY3_18, DY3_19, DY3_20, DY3_21, DY3_22, DY3_23, DY3_24, DY3_25, DY3_26, DY3_27, DY3_28, DY3_29, DY3_30, DY3_31: SS14; D_SMA
TP_YA24, TP_YA24b, TP_YA25, TP_YA25b, TP_YA26, TP_YA26b, TP_YA27, TP_YA27b, TP_YA28, TP_YA28b, TP_YA29, TP_YA29b, TP_YA30, TP_YA30b, TP_YA31, TP_YA31b: Stub; not fitted
TP_YB24, TP_YB24b, TP_YB25, TP_YB25b, TP_YB26, TP_YB26b, TP_YB27, TP_YB27b, TP_YB28, TP_YB28b, TP_YB29, TP_YB29b, TP_YB30, TP_YB30b, TP_YB31, TP_YB31b: Stub; not fitted
TP_YHS3, TP_YHS3R, TP_YHS3Rb, TP_YHS3b: Stub; not fitted
TP_YLS0, TP_YLS0R, TP_YLS0Rb, TP_YLS0b, TP_YLS1, TP_YLS1R, TP_YLS1Rb, TP_YLS1b, TP_YLS2, TP_YLS2R, TP_YLS2Rb, TP_YLS2b, TP_YLS3, TP_YLS3R, TP_YLS3Rb, TP_YLS3b, TP_YLS4, TP_YLS4R, TP_YLS4Rb, TP_YLS4b, TP_YLS5, TP_YLS5R, TP_YLS5Rb, TP_YLS5b, TP_YLS6, TP_YLS6R, TP_YLS6Rb, TP_YLS6b, TP_YLS7, TP_YLS7R, TP_YLS7Rb, TP_YLS7b: Stub; not fitted

Connections:
YA24: DY3_1.2 (A), DY3_2.1 (K), TP_YA24.1, TP_YA24b.1
YA25: DY3_5.2 (A), DY3_6.1 (K), TP_YA25.1, TP_YA25b.1
YA26: DY3_9.2 (A), DY3_10.1 (K), TP_YA26.1, TP_YA26b.1
YA27: DY3_13.2 (A), DY3_14.1 (K), TP_YA27.1, TP_YA27b.1
YA28: DY3_17.2 (A), DY3_18.1 (K), TP_YA28.1, TP_YA28b.1
YA29: DY3_21.2 (A), DY3_22.1 (K), TP_YA29.1, TP_YA29b.1
YA30: DY3_25.2 (A), DY3_26.1 (K), TP_YA30.1, TP_YA30b.1
YA31: DY3_29.2 (A), DY3_30.1 (K), TP_YA31.1, TP_YA31b.1
YB24: DY3_0.1 (K), DY3_3.2 (A), TP_YB24.1, TP_YB24b.1
YB25: DY3_4.1 (K), DY3_7.2 (A), TP_YB25.1, TP_YB25b.1
YB26: DY3_8.1 (K), DY3_11.2 (A), TP_YB26.1, TP_YB26b.1
YB27: DY3_12.1 (K), DY3_15.2 (A), TP_YB27.1, TP_YB27b.1
YB28: DY3_16.1 (K), DY3_19.2 (A), TP_YB28.1, TP_YB28b.1
YB29: DY3_20.1 (K), DY3_23.2 (A), TP_YB29.1, TP_YB29b.1
YB30: DY3_24.1 (K), DY3_27.2 (A), TP_YB30.1, TP_YB30b.1
YB31: DY3_28.1 (K), DY3_31.2 (A), TP_YB31.1, TP_YB31b.1
YHS3: DY3_0.2 (A), DY3_4.2 (A), DY3_8.2 (A), DY3_12.2 (A), DY3_16.2 (A), DY3_20.2 (A), DY3_24.2 (A), DY3_28.2 (A), TP_YHS3.1, TP_YHS3b.1
YHS3R: DY3_2.2 (A), DY3_6.2 (A), DY3_10.2 (A), DY3_14.2 (A), DY3_18.2 (A), DY3_22.2 (A), DY3_26.2 (A), DY3_30.2 (A), TP_YHS3R.1, TP_YHS3Rb.1
YLS0: DY3_1.1 (K), TP_YLS0.1, TP_YLS0b.1
YLS0R: DY3_3.1 (K), TP_YLS0R.1, TP_YLS0Rb.1
YLS1: DY3_5.1 (K), TP_YLS1.1, TP_YLS1b.1
YLS1R: DY3_7.1 (K), TP_YLS1R.1, TP_YLS1Rb.1
YLS2: DY3_9.1 (K), TP_YLS2.1, TP_YLS2b.1
YLS2R: DY3_11.1 (K), TP_YLS2R.1, TP_YLS2Rb.1
YLS3: DY3_13.1 (K), TP_YLS3.1, TP_YLS3b.1
YLS3R: DY3_15.1 (K), TP_YLS3R.1, TP_YLS3Rb.1
YLS4: DY3_17.1 (K), TP_YLS4.1, TP_YLS4b.1
YLS4R: DY3_19.1 (K), TP_YLS4R.1, TP_YLS4Rb.1
YLS5: DY3_21.1 (K), TP_YLS5.1, TP_YLS5b.1
YLS5R: DY3_23.1 (K), TP_YLS5R.1, TP_YLS5Rb.1
YLS6: DY3_25.1 (K), TP_YLS6.1, TP_YLS6b.1
YLS6R: DY3_27.1 (K), TP_YLS6R.1, TP_YLS6Rb.1
YLS7: DY3_29.1 (K), TP_YLS7.1, TP_YLS7b.1
YLS7R: DY3_31.1 (K), TP_YLS7R.1, TP_YLS7Rb.1

Notes on the sheet:
REQ-HIER-OCTAL steer_octal_Y_g3 pins=34
lines=[24, 25, 26, 27, 28, 29, 30, 31]
