fractalclockwork/core-memory-redux/kicad/driver_64x64/steer_octal_Y_g4.kicad_sch

## KiCad design kicad/driver_64x64/steer_octal_Y_g4.kicad_sch (2026-10-05)

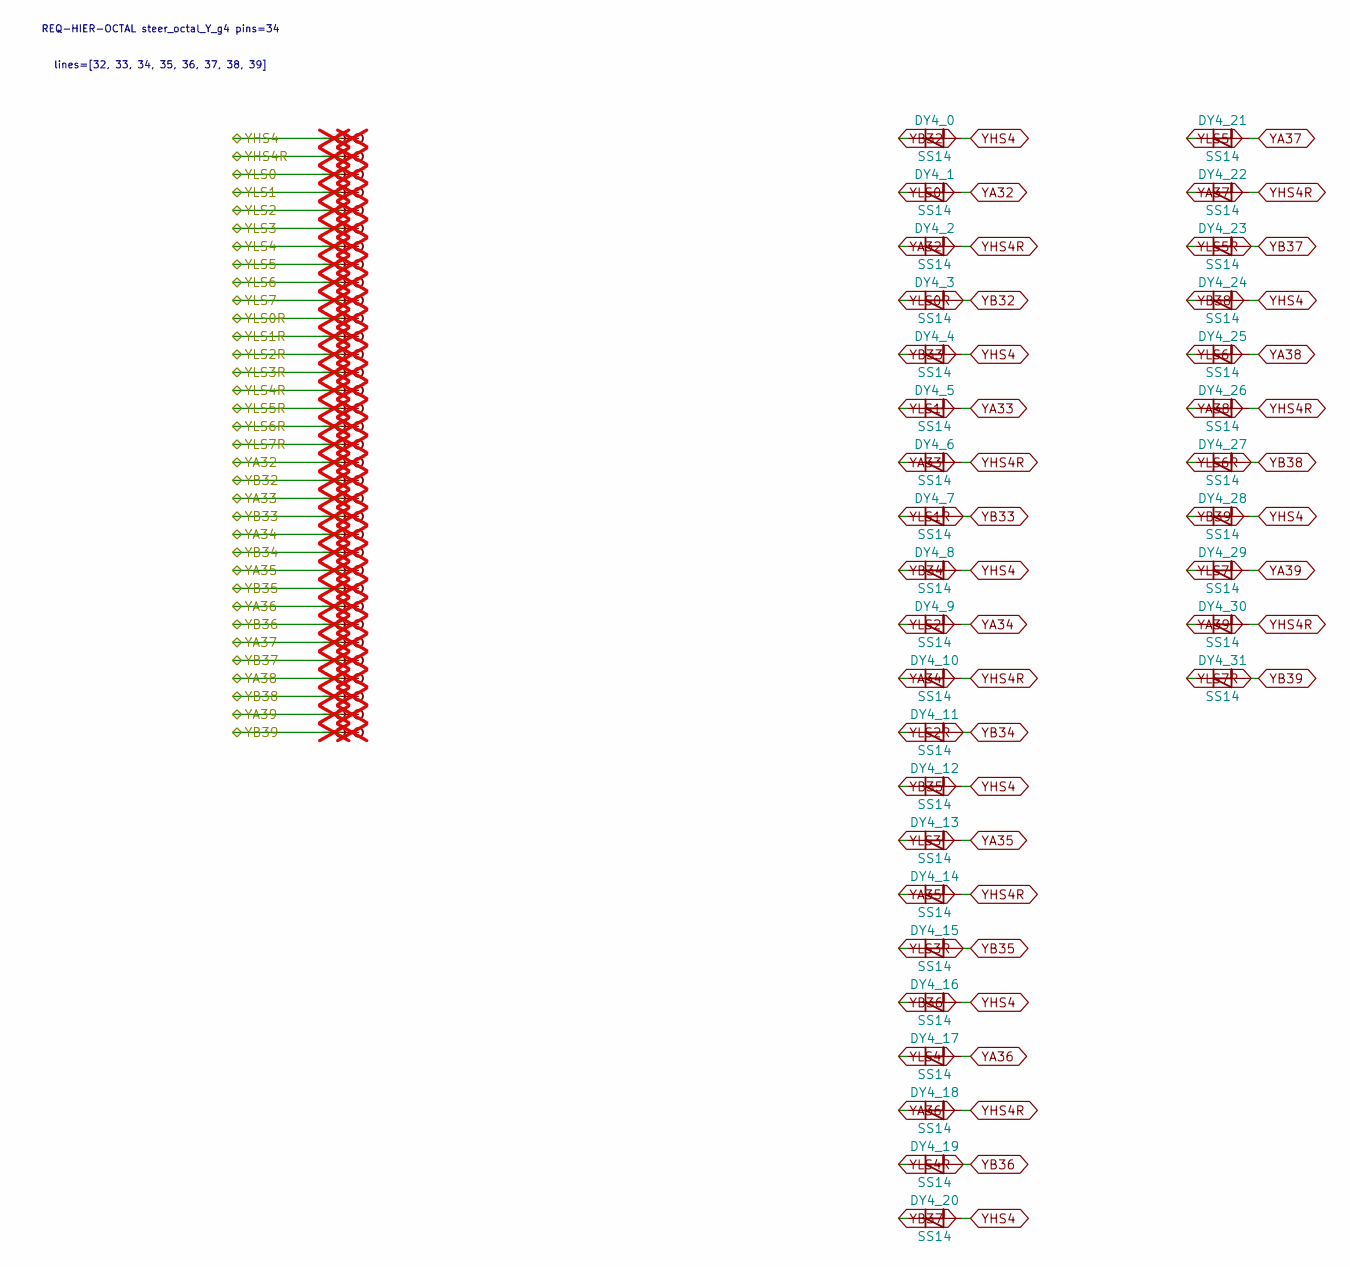
[picture p42: schematic steer_octal_Y_g4.kicad_sch]

Parts:
DY4_0, DY4_1, DY4_2, DY4_3, DY4_4, DY4_5, DY4_6, DY4_7, DY4_8, DY4_9, DY4_10, DY4_11, DY4_12, DY4_13, DY4_14, DY4_15, DY4_16, DY4_17, DY4_18, DY4_19, DY4_20, DY4_21, DY4_22, DY4_23, DY4_24, DY4_25, DY4_26, DY4_27, DY4_28, DY4_29, DY4_30, DY4_31: SS14; D_SMA
TP_YA32, TP_YA32b, TP_YA33, TP_YA33b, TP_YA34, TP_YA34b, TP_YA35, TP_YA35b, TP_YA36, TP_YA36b, TP_YA37, TP_YA37b, TP_YA38, TP_YA38b, TP_YA39, TP_YA39b: Stub; not fitted
TP_YB32, TP_YB32b, TP_YB33, TP_YB33b, TP_YB34, TP_YB34b, TP_YB35, TP_YB35b, TP_YB36, TP_YB36b, TP_YB37, TP_YB37b, TP_YB38, TP_YB38b, TP_YB39, TP_YB39b: Stub; not fitted
TP_YHS4, TP_YHS4R, TP_YHS4Rb, TP_YHS4b: Stub; not fitted
TP_YLS0, TP_YLS0R, TP_YLS0Rb, TP_YLS0b, TP_YLS1, TP_YLS1R, TP_YLS1Rb, TP_YLS1b, TP_YLS2, TP_YLS2R, TP_YLS2Rb, TP_YLS2b, TP_YLS3, TP_YLS3R, TP_YLS3Rb, TP_YLS3b, TP_YLS4, TP_YLS4R, TP_YLS4Rb, TP_YLS4b, TP_YLS5, TP_YLS5R, TP_YLS5Rb, TP_YLS5b, TP_YLS6, TP_YLS6R, TP_YLS6Rb, TP_YLS6b, TP_YLS7, TP_YLS7R, TP_YLS7Rb, TP_YLS7b: Stub; not fitted

Connections:
YA32: DY4_1.2 (A), DY4_2.1 (K), TP_YA32.1, TP_YA32b.1
YA33: DY4_5.2 (A), DY4_6.1 (K), TP_YA33.1, TP_YA33b.1
YA34: DY4_9.2 (A), DY4_10.1 (K), TP_YA34.1, TP_YA34b.1
YA35: DY4_13.2 (A), DY4_14.1 (K), TP_YA35.1, TP_YA35b.1
YA36: DY4_17.2 (A), DY4_18.1 (K), TP_YA36.1, TP_YA36b.1
YA37: DY4_21.2 (A), DY4_22.1 (K), TP_YA37.1, TP_YA37b.1
YA38: DY4_25.2 (A), DY4_26.1 (K), TP_YA38.1, TP_YA38b.1
YA39: DY4_29.2 (A), DY4_30.1 (K), TP_YA39.1, TP_YA39b.1
YB32: DY4_0.1 (K), DY4_3.2 (A), TP_YB32.1, TP_YB32b.1
YB33: DY4_4.1 (K), DY4_7.2 (A), TP_YB33.1, TP_YB33b.1
YB34: DY4_8.1 (K), DY4_11.2 (A), TP_YB34.1, TP_YB34b.1
YB35: DY4_12.1 (K), DY4_15.2 (A), TP_YB35.1, TP_YB35b.1
YB36: DY4_16.1 (K), DY4_19.2 (A), TP_YB36.1, TP_YB36b.1
YB37: DY4_20.1 (K), DY4_23.2 (A), TP_YB37.1, TP_YB37b.1
YB38: DY4_24.1 (K), DY4_27.2 (A), TP_YB38.1, TP_YB38b.1
YB39: DY4_28.1 (K), DY4_31.2 (A), TP_YB39.1, TP_YB39b.1
YHS4: DY4_0.2 (A), DY4_4.2 (A), DY4_8.2 (A), DY4_12.2 (A), DY4_16.2 (A), DY4_20.2 (A), DY4_24.2 (A), DY4_28.2 (A), TP_YHS4.1, TP_YHS4b.1
YHS4R: DY4_2.2 (A), DY4_6.2 (A), DY4_10.2 (A), DY4_14.2 (A), DY4_18.2 (A), DY4_22.2 (A), DY4_26.2 (A), DY4_30.2 (A), TP_YHS4R.1, TP_YHS4Rb.1
YLS0: DY4_1.1 (K), TP_YLS0.1, TP_YLS0b.1
YLS0R: DY4_3.1 (K), TP_YLS0R.1, TP_YLS0Rb.1
YLS1: DY4_5.1 (K), TP_YLS1.1, TP_YLS1b.1
YLS1R: DY4_7.1 (K), TP_YLS1R.1, TP_YLS1Rb.1
YLS2: DY4_9.1 (K), TP_YLS2.1, TP_YLS2b.1
YLS2R: DY4_11.1 (K), TP_YLS2R.1, TP_YLS2Rb.1
YLS3: DY4_13.1 (K), TP_YLS3.1, TP_YLS3b.1
YLS3R: DY4_15.1 (K), TP_YLS3R.1, TP_YLS3Rb.1
YLS4: DY4_17.1 (K), TP_YLS4.1, TP_YLS4b.1
YLS4R: DY4_19.1 (K), TP_YLS4R.1, TP_YLS4Rb.1
YLS5: DY4_21.1 (K), TP_YLS5.1, TP_YLS5b.1
YLS5R: DY4_23.1 (K), TP_YLS5R.1, TP_YLS5Rb.1
YLS6: DY4_25.1 (K), TP_YLS6.1, TP_YLS6b.1
YLS6R: DY4_27.1 (K), TP_YLS6R.1, TP_YLS6Rb.1
YLS7: DY4_29.1 (K), TP_YLS7.1, TP_YLS7b.1
YLS7R: DY4_31.1 (K), TP_YLS7R.1, TP_YLS7Rb.1

Notes on the sheet:
REQ-HIER-OCTAL steer_octal_Y_g4 pins=34
lines=[32, 33, 34, 35, 36, 37, 38, 39]
