fractalclockwork/core-memory-redux/kicad/driver_64x64/steer_octal_Y_g5.kicad_sch

## KiCad design kicad/driver_64x64/steer_octal_Y_g5.kicad_sch (2026-10-05)

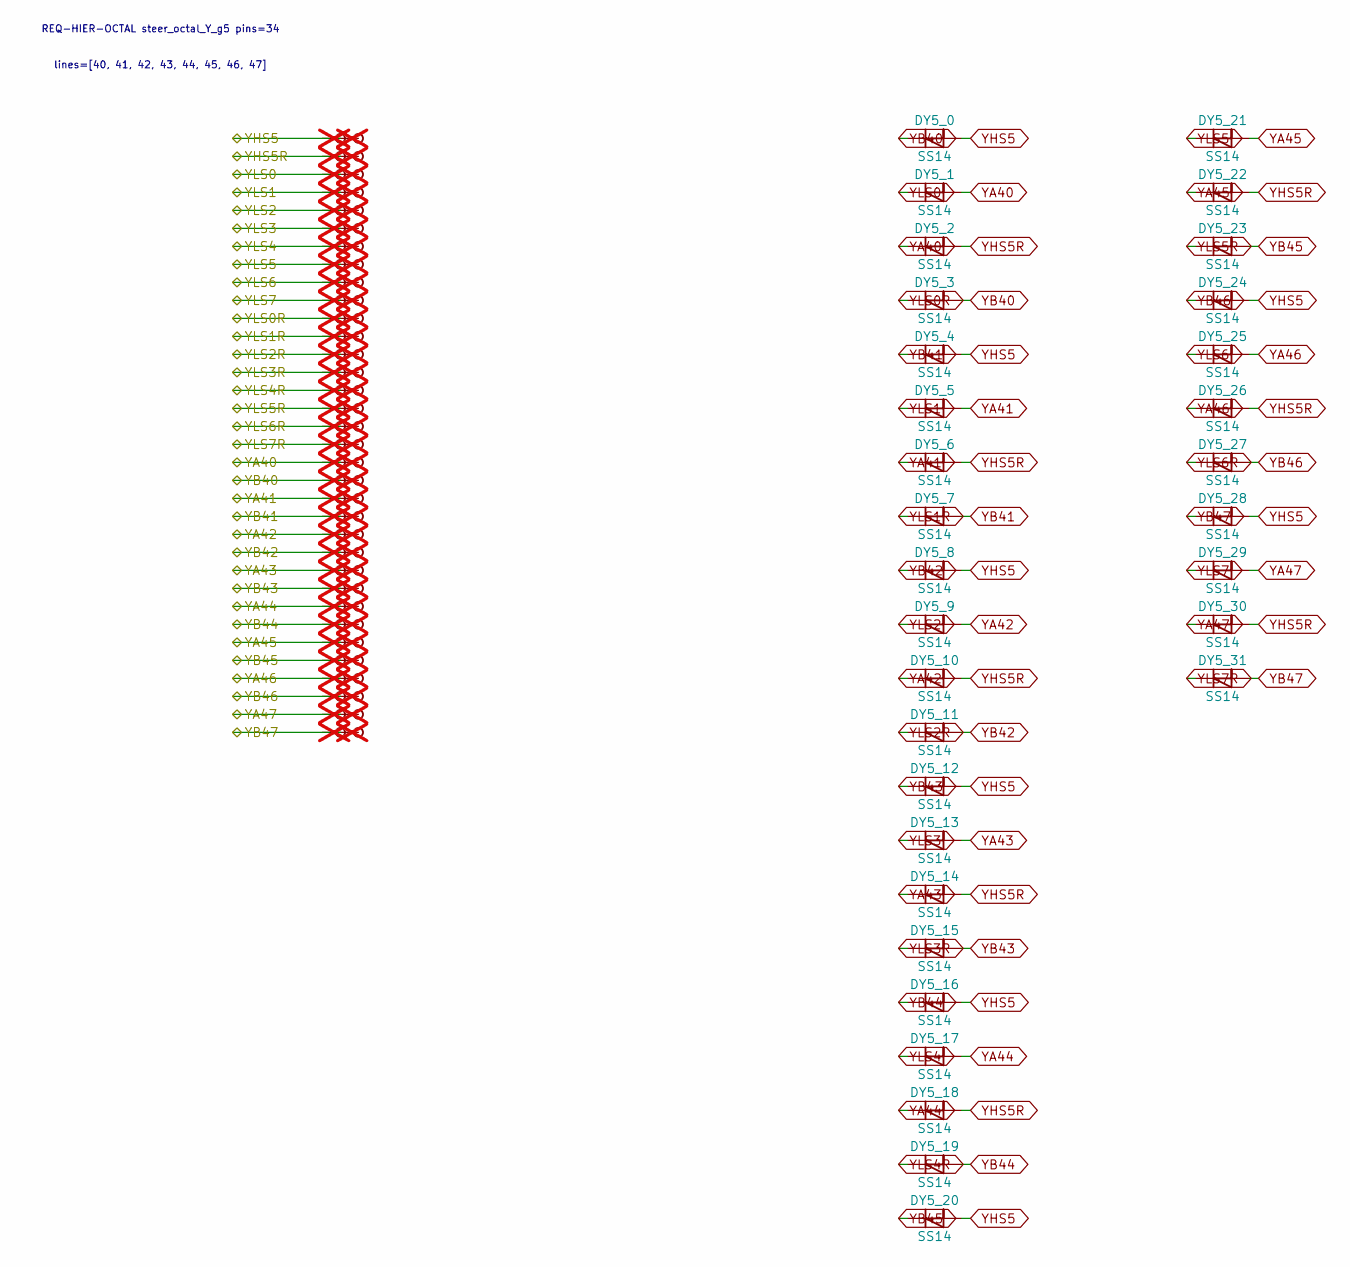
[picture p43: schematic steer_octal_Y_g5.kicad_sch]

Parts:
DY5_0, DY5_1, DY5_2, DY5_3, DY5_4, DY5_5, DY5_6, DY5_7, DY5_8, DY5_9, DY5_10, DY5_11, DY5_12, DY5_13, DY5_14, DY5_15, DY5_16, DY5_17, DY5_18, DY5_19, DY5_20, DY5_21, DY5_22, DY5_23, DY5_24, DY5_25, DY5_26, DY5_27, DY5_28, DY5_29, DY5_30, DY5_31: SS14; D_SMA
TP_YA40, TP_YA40b, TP_YA41, TP_YA41b, TP_YA42, TP_YA42b, TP_YA43, TP_YA43b, TP_YA44, TP_YA44b, TP_YA45, TP_YA45b, TP_YA46, TP_YA46b, TP_YA47, TP_YA47b: Stub; not fitted
TP_YB40, TP_YB40b, TP_YB41, TP_YB41b, TP_YB42, TP_YB42b, TP_YB43, TP_YB43b, TP_YB44, TP_YB44b, TP_YB45, TP_YB45b, TP_YB46, TP_YB46b, TP_YB47, TP_YB47b: Stub; not fitted
TP_YHS5, TP_YHS5R, TP_YHS5Rb, TP_YHS5b: Stub; not fitted
TP_YLS0, TP_YLS0R, TP_YLS0Rb, TP_YLS0b, TP_YLS1, TP_YLS1R, TP_YLS1Rb, TP_YLS1b, TP_YLS2, TP_YLS2R, TP_YLS2Rb, TP_YLS2b, TP_YLS3, TP_YLS3R, TP_YLS3Rb, TP_YLS3b, TP_YLS4, TP_YLS4R, TP_YLS4Rb, TP_YLS4b, TP_YLS5, TP_YLS5R, TP_YLS5Rb, TP_YLS5b, TP_YLS6, TP_YLS6R, TP_YLS6Rb, TP_YLS6b, TP_YLS7, TP_YLS7R, TP_YLS7Rb, TP_YLS7b: Stub; not fitted

Connections:
YA40: DY5_1.2 (A), DY5_2.1 (K), TP_YA40.1, TP_YA40b.1
YA41: DY5_5.2 (A), DY5_6.1 (K), TP_YA41.1, TP_YA41b.1
YA42: DY5_9.2 (A), DY5_10.1 (K), TP_YA42.1, TP_YA42b.1
YA43: DY5_13.2 (A), DY5_14.1 (K), TP_YA43.1, TP_YA43b.1
YA44: DY5_17.2 (A), DY5_18.1 (K), TP_YA44.1, TP_YA44b.1
YA45: DY5_21.2 (A), DY5_22.1 (K), TP_YA45.1, TP_YA45b.1
YA46: DY5_25.2 (A), DY5_26.1 (K), TP_YA46.1, TP_YA46b.1
YA47: DY5_29.2 (A), DY5_30.1 (K), TP_YA47.1, TP_YA47b.1
YB40: DY5_0.1 (K), DY5_3.2 (A), TP_YB40.1, TP_YB40b.1
YB41: DY5_4.1 (K), DY5_7.2 (A), TP_YB41.1, TP_YB41b.1
YB42: DY5_8.1 (K), DY5_11.2 (A), TP_YB42.1, TP_YB42b.1
YB43: DY5_12.1 (K), DY5_15.2 (A), TP_YB43.1, TP_YB43b.1
YB44: DY5_16.1 (K), DY5_19.2 (A), TP_YB44.1, TP_YB44b.1
YB45: DY5_20.1 (K), DY5_23.2 (A), TP_YB45.1, TP_YB45b.1
YB46: DY5_24.1 (K), DY5_27.2 (A), TP_YB46.1, TP_YB46b.1
YB47: DY5_28.1 (K), DY5_31.2 (A), TP_YB47.1, TP_YB47b.1
YHS5: DY5_0.2 (A), DY5_4.2 (A), DY5_8.2 (A), DY5_12.2 (A), DY5_16.2 (A), DY5_20.2 (A), DY5_24.2 (A), DY5_28.2 (A), TP_YHS5.1, TP_YHS5b.1
YHS5R: DY5_2.2 (A), DY5_6.2 (A), DY5_10.2 (A), DY5_14.2 (A), DY5_18.2 (A), DY5_22.2 (A), DY5_26.2 (A), DY5_30.2 (A), TP_YHS5R.1, TP_YHS5Rb.1
YLS0: DY5_1.1 (K), TP_YLS0.1, TP_YLS0b.1
YLS0R: DY5_3.1 (K), TP_YLS0R.1, TP_YLS0Rb.1
YLS1: DY5_5.1 (K), TP_YLS1.1, TP_YLS1b.1
YLS1R: DY5_7.1 (K), TP_YLS1R.1, TP_YLS1Rb.1
YLS2: DY5_9.1 (K), TP_YLS2.1, TP_YLS2b.1
YLS2R: DY5_11.1 (K), TP_YLS2R.1, TP_YLS2Rb.1
YLS3: DY5_13.1 (K), TP_YLS3.1, TP_YLS3b.1
YLS3R: DY5_15.1 (K), TP_YLS3R.1, TP_YLS3Rb.1
YLS4: DY5_17.1 (K), TP_YLS4.1, TP_YLS4b.1
YLS4R: DY5_19.1 (K), TP_YLS4R.1, TP_YLS4Rb.1
YLS5: DY5_21.1 (K), TP_YLS5.1, TP_YLS5b.1
YLS5R: DY5_23.1 (K), TP_YLS5R.1, TP_YLS5Rb.1
YLS6: DY5_25.1 (K), TP_YLS6.1, TP_YLS6b.1
YLS6R: DY5_27.1 (K), TP_YLS6R.1, TP_YLS6Rb.1
YLS7: DY5_29.1 (K), TP_YLS7.1, TP_YLS7b.1
YLS7R: DY5_31.1 (K), TP_YLS7R.1, TP_YLS7Rb.1

Notes on the sheet:
REQ-HIER-OCTAL steer_octal_Y_g5 pins=34
lines=[40, 41, 42, 43, 44, 45, 46, 47]
