fractalclockwork/core-memory-redux/kicad/driver_64x64/steer_octal_Y_g6.kicad_sch

## KiCad design kicad/driver_64x64/steer_octal_Y_g6.kicad_sch (2026-10-05)

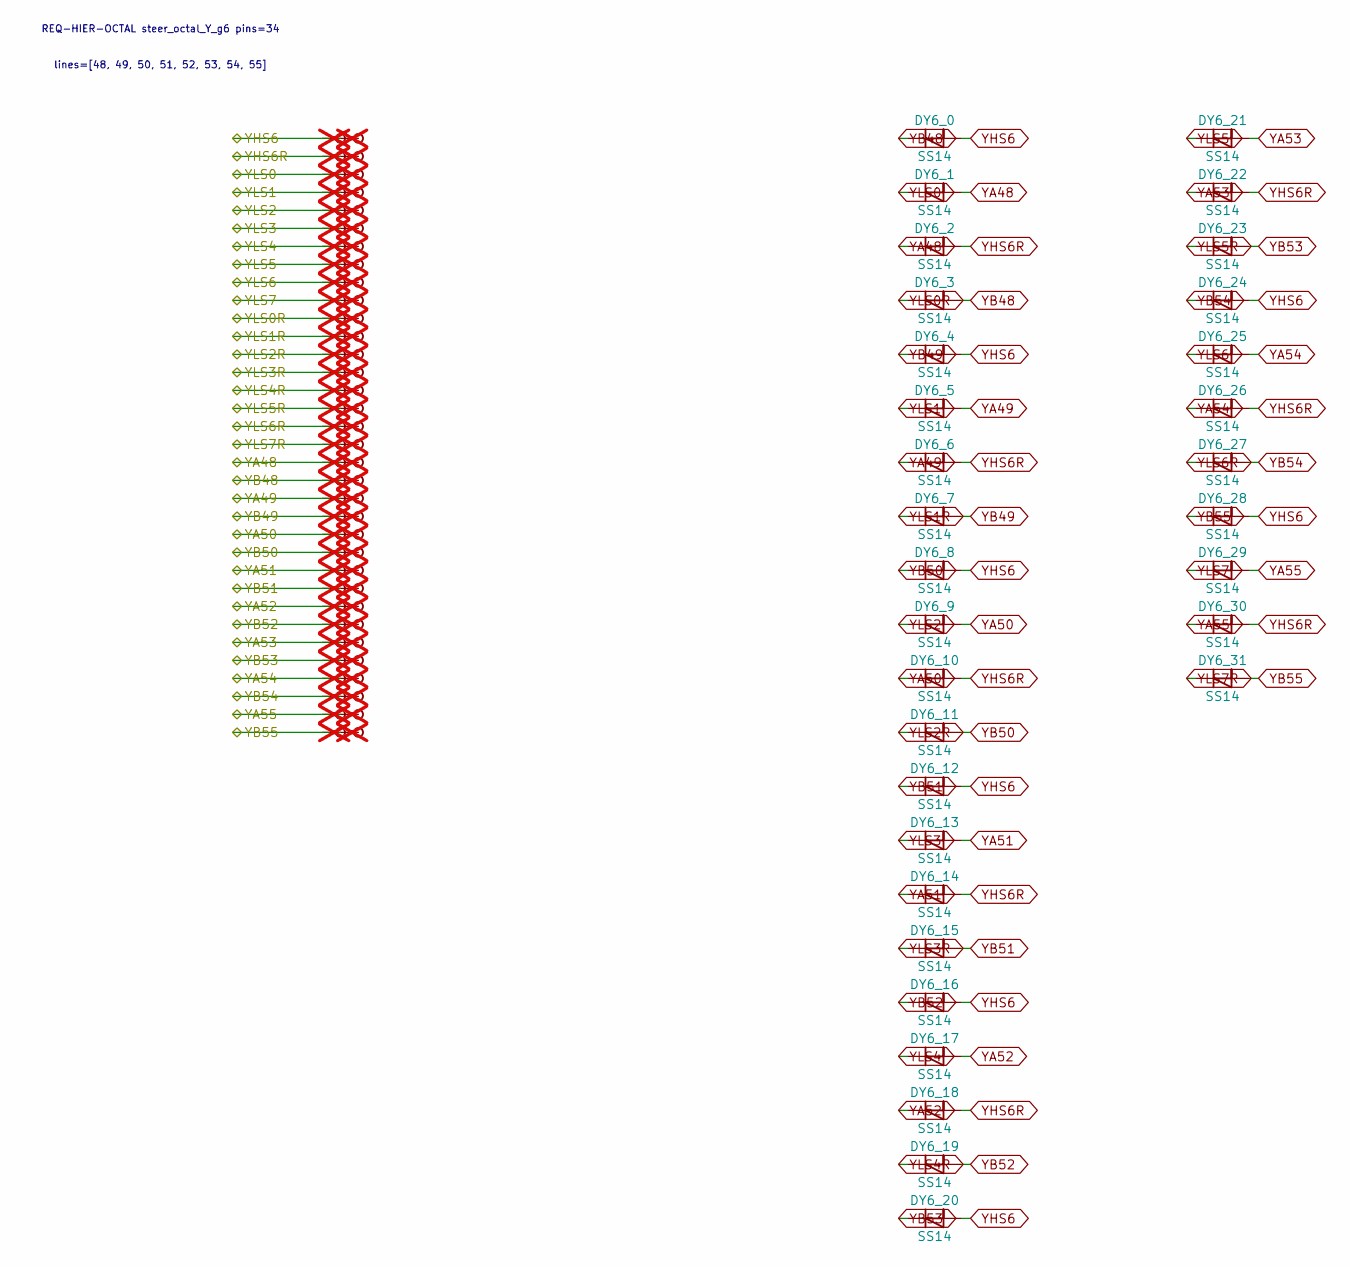
[picture p44: schematic steer_octal_Y_g6.kicad_sch]

Parts:
DY6_0, DY6_1, DY6_2, DY6_3, DY6_4, DY6_5, DY6_6, DY6_7, DY6_8, DY6_9, DY6_10, DY6_11, DY6_12, DY6_13, DY6_14, DY6_15, DY6_16, DY6_17, DY6_18, DY6_19, DY6_20, DY6_21, DY6_22, DY6_23, DY6_24, DY6_25, DY6_26, DY6_27, DY6_28, DY6_29, DY6_30, DY6_31: SS14; D_SMA
TP_YA48, TP_YA48b, TP_YA49, TP_YA49b, TP_YA50, TP_YA50b, TP_YA51, TP_YA51b, TP_YA52, TP_YA52b, TP_YA53, TP_YA53b, TP_YA54, TP_YA54b, TP_YA55, TP_YA55b: Stub; not fitted
TP_YB48, TP_YB48b, TP_YB49, TP_YB49b, TP_YB50, TP_YB50b, TP_YB51, TP_YB51b, TP_YB52, TP_YB52b, TP_YB53, TP_YB53b, TP_YB54, TP_YB54b, TP_YB55, TP_YB55b: Stub; not fitted
TP_YHS6, TP_YHS6R, TP_YHS6Rb, TP_YHS6b: Stub; not fitted
TP_YLS0, TP_YLS0R, TP_YLS0Rb, TP_YLS0b, TP_YLS1, TP_YLS1R, TP_YLS1Rb, TP_YLS1b, TP_YLS2, TP_YLS2R, TP_YLS2Rb, TP_YLS2b, TP_YLS3, TP_YLS3R, TP_YLS3Rb, TP_YLS3b, TP_YLS4, TP_YLS4R, TP_YLS4Rb, TP_YLS4b, TP_YLS5, TP_YLS5R, TP_YLS5Rb, TP_YLS5b, TP_YLS6, TP_YLS6R, TP_YLS6Rb, TP_YLS6b, TP_YLS7, TP_YLS7R, TP_YLS7Rb, TP_YLS7b: Stub; not fitted

Connections:
YA48: DY6_1.2 (A), DY6_2.1 (K), TP_YA48.1, TP_YA48b.1
YA49: DY6_5.2 (A), DY6_6.1 (K), TP_YA49.1, TP_YA49b.1
YA50: DY6_9.2 (A), DY6_10.1 (K), TP_YA50.1, TP_YA50b.1
YA51: DY6_13.2 (A), DY6_14.1 (K), TP_YA51.1, TP_YA51b.1
YA52: DY6_17.2 (A), DY6_18.1 (K), TP_YA52.1, TP_YA52b.1
YA53: DY6_21.2 (A), DY6_22.1 (K), TP_YA53.1, TP_YA53b.1
YA54: DY6_25.2 (A), DY6_26.1 (K), TP_YA54.1, TP_YA54b.1
YA55: DY6_29.2 (A), DY6_30.1 (K), TP_YA55.1, TP_YA55b.1
YB48: DY6_0.1 (K), DY6_3.2 (A), TP_YB48.1, TP_YB48b.1
YB49: DY6_4.1 (K), DY6_7.2 (A), TP_YB49.1, TP_YB49b.1
YB50: DY6_8.1 (K), DY6_11.2 (A), TP_YB50.1, TP_YB50b.1
YB51: DY6_12.1 (K), DY6_15.2 (A), TP_YB51.1, TP_YB51b.1
YB52: DY6_16.1 (K), DY6_19.2 (A), TP_YB52.1, TP_YB52b.1
YB53: DY6_20.1 (K), DY6_23.2 (A), TP_YB53.1, TP_YB53b.1
YB54: DY6_24.1 (K), DY6_27.2 (A), TP_YB54.1, TP_YB54b.1
YB55: DY6_28.1 (K), DY6_31.2 (A), TP_YB55.1, TP_YB55b.1
YHS6: DY6_0.2 (A), DY6_4.2 (A), DY6_8.2 (A), DY6_12.2 (A), DY6_16.2 (A), DY6_20.2 (A), DY6_24.2 (A), DY6_28.2 (A), TP_YHS6.1, TP_YHS6b.1
YHS6R: DY6_2.2 (A), DY6_6.2 (A), DY6_10.2 (A), DY6_14.2 (A), DY6_18.2 (A), DY6_22.2 (A), DY6_26.2 (A), DY6_30.2 (A), TP_YHS6R.1, TP_YHS6Rb.1
YLS0: DY6_1.1 (K), TP_YLS0.1, TP_YLS0b.1
YLS0R: DY6_3.1 (K), TP_YLS0R.1, TP_YLS0Rb.1
YLS1: DY6_5.1 (K), TP_YLS1.1, TP_YLS1b.1
YLS1R: DY6_7.1 (K), TP_YLS1R.1, TP_YLS1Rb.1
YLS2: DY6_9.1 (K), TP_YLS2.1, TP_YLS2b.1
YLS2R: DY6_11.1 (K), TP_YLS2R.1, TP_YLS2Rb.1
YLS3: DY6_13.1 (K), TP_YLS3.1, TP_YLS3b.1
YLS3R: DY6_15.1 (K), TP_YLS3R.1, TP_YLS3Rb.1
YLS4: DY6_17.1 (K), TP_YLS4.1, TP_YLS4b.1
YLS4R: DY6_19.1 (K), TP_YLS4R.1, TP_YLS4Rb.1
YLS5: DY6_21.1 (K), TP_YLS5.1, TP_YLS5b.1
YLS5R: DY6_23.1 (K), TP_YLS5R.1, TP_YLS5Rb.1
YLS6: DY6_25.1 (K), TP_YLS6.1, TP_YLS6b.1
YLS6R: DY6_27.1 (K), TP_YLS6R.1, TP_YLS6Rb.1
YLS7: DY6_29.1 (K), TP_YLS7.1, TP_YLS7b.1
YLS7R: DY6_31.1 (K), TP_YLS7R.1, TP_YLS7Rb.1

Notes on the sheet:
REQ-HIER-OCTAL steer_octal_Y_g6 pins=34
lines=[48, 49, 50, 51, 52, 53, 54, 55]
