fractalclockwork/core-memory-redux/kicad/driver_64x64/steer_octal_Y_g7.kicad_sch

## KiCad design kicad/driver_64x64/steer_octal_Y_g7.kicad_sch (2026-10-05)

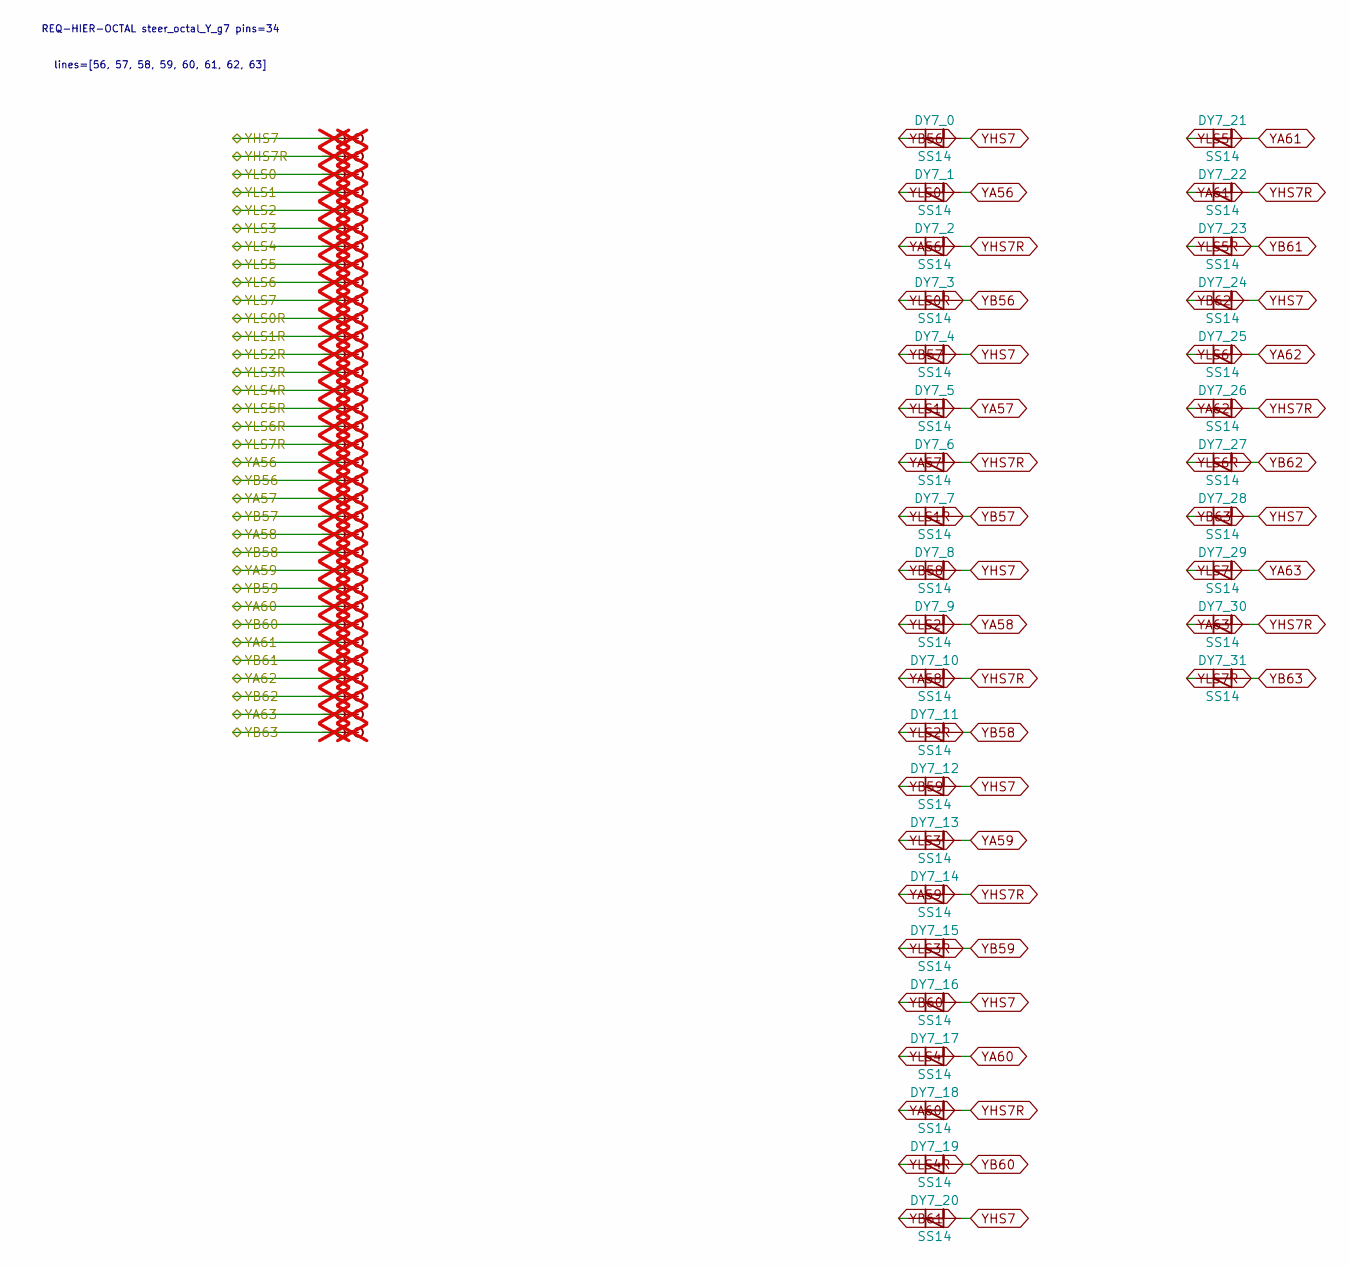
[picture p45: schematic steer_octal_Y_g7.kicad_sch]

Parts:
DY7_0, DY7_1, DY7_2, DY7_3, DY7_4, DY7_5, DY7_6, DY7_7, DY7_8, DY7_9, DY7_10, DY7_11, DY7_12, DY7_13, DY7_14, DY7_15, DY7_16, DY7_17, DY7_18, DY7_19, DY7_20, DY7_21, DY7_22, DY7_23, DY7_24, DY7_25, DY7_26, DY7_27, DY7_28, DY7_29, DY7_30, DY7_31: SS14; D_SMA
TP_YA56, TP_YA56b, TP_YA57, TP_YA57b, TP_YA58, TP_YA58b, TP_YA59, TP_YA59b, TP_YA60, TP_YA60b, TP_YA61, TP_YA61b, TP_YA62, TP_YA62b, TP_YA63, TP_YA63b: Stub; not fitted
TP_YB56, TP_YB56b, TP_YB57, TP_YB57b, TP_YB58, TP_YB58b, TP_YB59, TP_YB59b, TP_YB60, TP_YB60b, TP_YB61, TP_YB61b, TP_YB62, TP_YB62b, TP_YB63, TP_YB63b: Stub; not fitted
TP_YHS7, TP_YHS7R, TP_YHS7Rb, TP_YHS7b: Stub; not fitted
TP_YLS0, TP_YLS0R, TP_YLS0Rb, TP_YLS0b, TP_YLS1, TP_YLS1R, TP_YLS1Rb, TP_YLS1b, TP_YLS2, TP_YLS2R, TP_YLS2Rb, TP_YLS2b, TP_YLS3, TP_YLS3R, TP_YLS3Rb, TP_YLS3b, TP_YLS4, TP_YLS4R, TP_YLS4Rb, TP_YLS4b, TP_YLS5, TP_YLS5R, TP_YLS5Rb, TP_YLS5b, TP_YLS6, TP_YLS6R, TP_YLS6Rb, TP_YLS6b, TP_YLS7, TP_YLS7R, TP_YLS7Rb, TP_YLS7b: Stub; not fitted

Connections:
YA56: DY7_1.2 (A), DY7_2.1 (K), TP_YA56.1, TP_YA56b.1
YA57: DY7_5.2 (A), DY7_6.1 (K), TP_YA57.1, TP_YA57b.1
YA58: DY7_9.2 (A), DY7_10.1 (K), TP_YA58.1, TP_YA58b.1
YA59: DY7_13.2 (A), DY7_14.1 (K), TP_YA59.1, TP_YA59b.1
YA60: DY7_17.2 (A), DY7_18.1 (K), TP_YA60.1, TP_YA60b.1
YA61: DY7_21.2 (A), DY7_22.1 (K), TP_YA61.1, TP_YA61b.1
YA62: DY7_25.2 (A), DY7_26.1 (K), TP_YA62.1, TP_YA62b.1
YA63: DY7_29.2 (A), DY7_30.1 (K), TP_YA63.1, TP_YA63b.1
YB56: DY7_0.1 (K), DY7_3.2 (A), TP_YB56.1, TP_YB56b.1
YB57: DY7_4.1 (K), DY7_7.2 (A), TP_YB57.1, TP_YB57b.1
YB58: DY7_8.1 (K), DY7_11.2 (A), TP_YB58.1, TP_YB58b.1
YB59: DY7_12.1 (K), DY7_15.2 (A), TP_YB59.1, TP_YB59b.1
YB60: DY7_16.1 (K), DY7_19.2 (A), TP_YB60.1, TP_YB60b.1
YB61: DY7_20.1 (K), DY7_23.2 (A), TP_YB61.1, TP_YB61b.1
YB62: DY7_24.1 (K), DY7_27.2 (A), TP_YB62.1, TP_YB62b.1
YB63: DY7_28.1 (K), DY7_31.2 (A), TP_YB63.1, TP_YB63b.1
YHS7: DY7_0.2 (A), DY7_4.2 (A), DY7_8.2 (A), DY7_12.2 (A), DY7_16.2 (A), DY7_20.2 (A), DY7_24.2 (A), DY7_28.2 (A), TP_YHS7.1, TP_YHS7b.1
YHS7R: DY7_2.2 (A), DY7_6.2 (A), DY7_10.2 (A), DY7_14.2 (A), DY7_18.2 (A), DY7_22.2 (A), DY7_26.2 (A), DY7_30.2 (A), TP_YHS7R.1, TP_YHS7Rb.1
YLS0: DY7_1.1 (K), TP_YLS0.1, TP_YLS0b.1
YLS0R: DY7_3.1 (K), TP_YLS0R.1, TP_YLS0Rb.1
YLS1: DY7_5.1 (K), TP_YLS1.1, TP_YLS1b.1
YLS1R: DY7_7.1 (K), TP_YLS1R.1, TP_YLS1Rb.1
YLS2: DY7_9.1 (K), TP_YLS2.1, TP_YLS2b.1
YLS2R: DY7_11.1 (K), TP_YLS2R.1, TP_YLS2Rb.1
YLS3: DY7_13.1 (K), TP_YLS3.1, TP_YLS3b.1
YLS3R: DY7_15.1 (K), TP_YLS3R.1, TP_YLS3Rb.1
YLS4: DY7_17.1 (K), TP_YLS4.1, TP_YLS4b.1
YLS4R: DY7_19.1 (K), TP_YLS4R.1, TP_YLS4Rb.1
YLS5: DY7_21.1 (K), TP_YLS5.1, TP_YLS5b.1
YLS5R: DY7_23.1 (K), TP_YLS5R.1, TP_YLS5Rb.1
YLS6: DY7_25.1 (K), TP_YLS6.1, TP_YLS6b.1
YLS6R: DY7_27.1 (K), TP_YLS6R.1, TP_YLS6Rb.1
YLS7: DY7_29.1 (K), TP_YLS7.1, TP_YLS7b.1
YLS7R: DY7_31.1 (K), TP_YLS7R.1, TP_YLS7Rb.1

Notes on the sheet:
REQ-HIER-OCTAL steer_octal_Y_g7 pins=34
lines=[56, 57, 58, 59, 60, 61, 62, 63]
