fractalclockwork/core-memory-redux/kicad/pcb_axis_octal/pcb_axis_octal.kicad_sch

## KiCad design kicad/pcb_axis_octal/pcb_axis_octal.kicad_sch (2026-10-05)

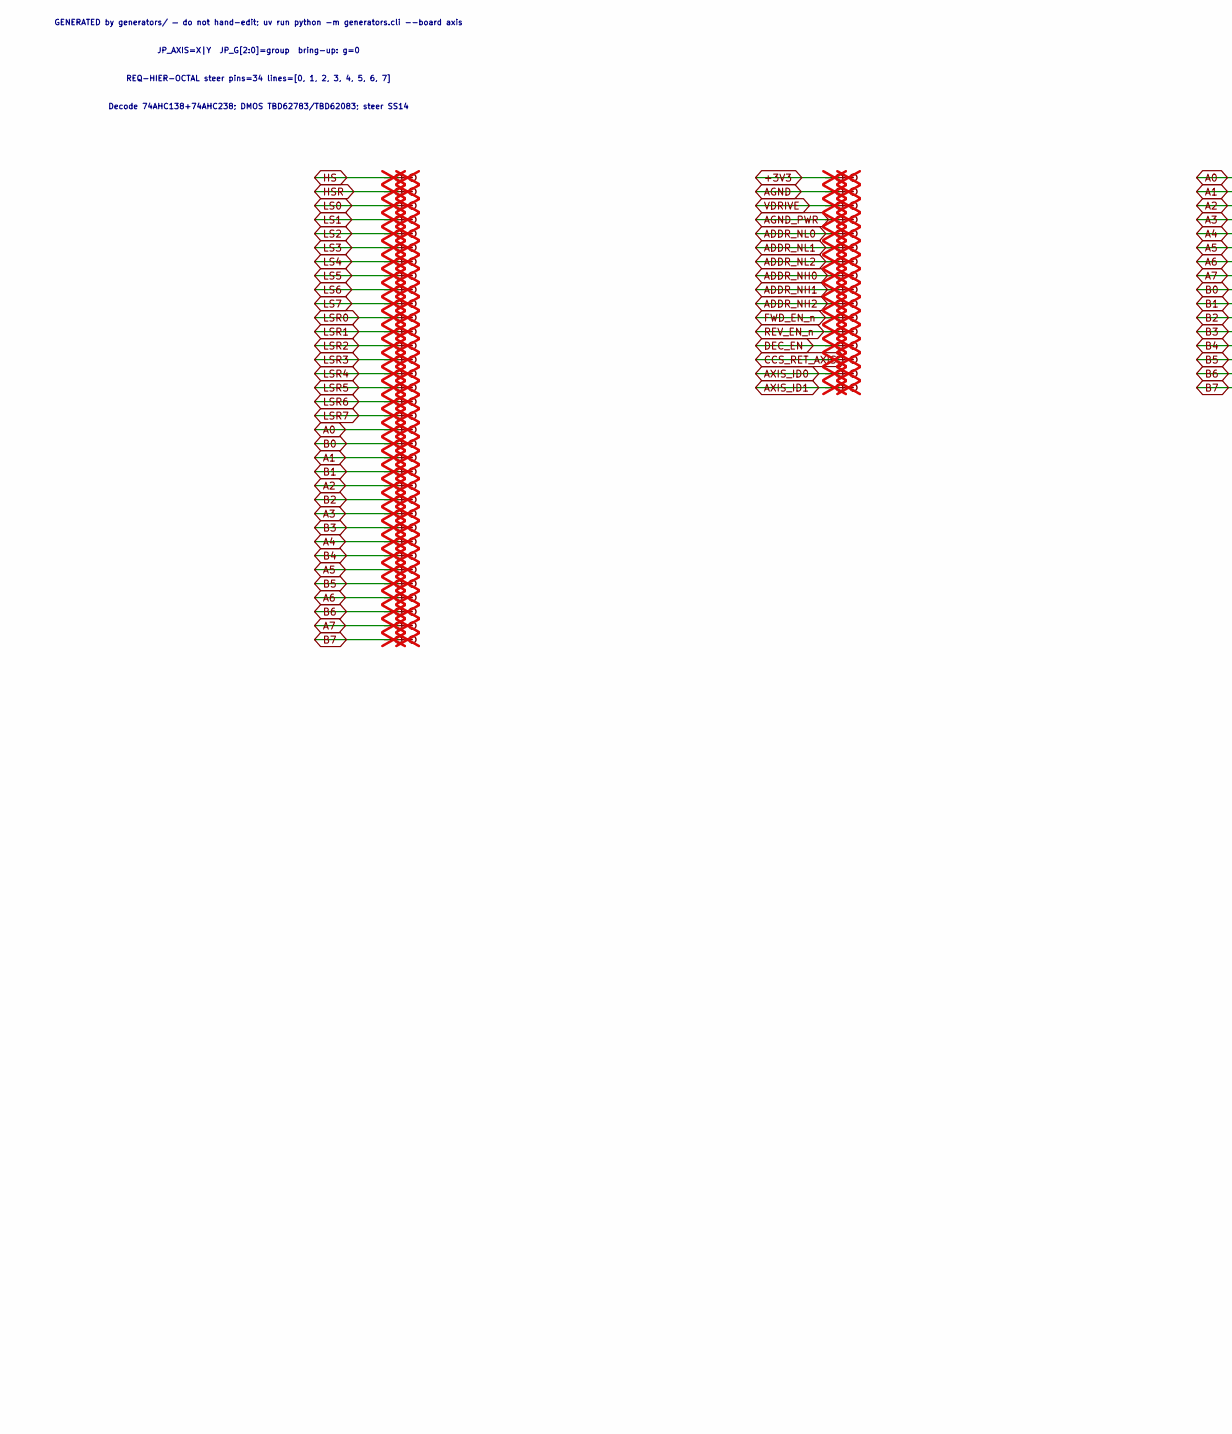
[picture p46: schematic pcb_axis_octal.kicad_sch, part in row 1, column 1]

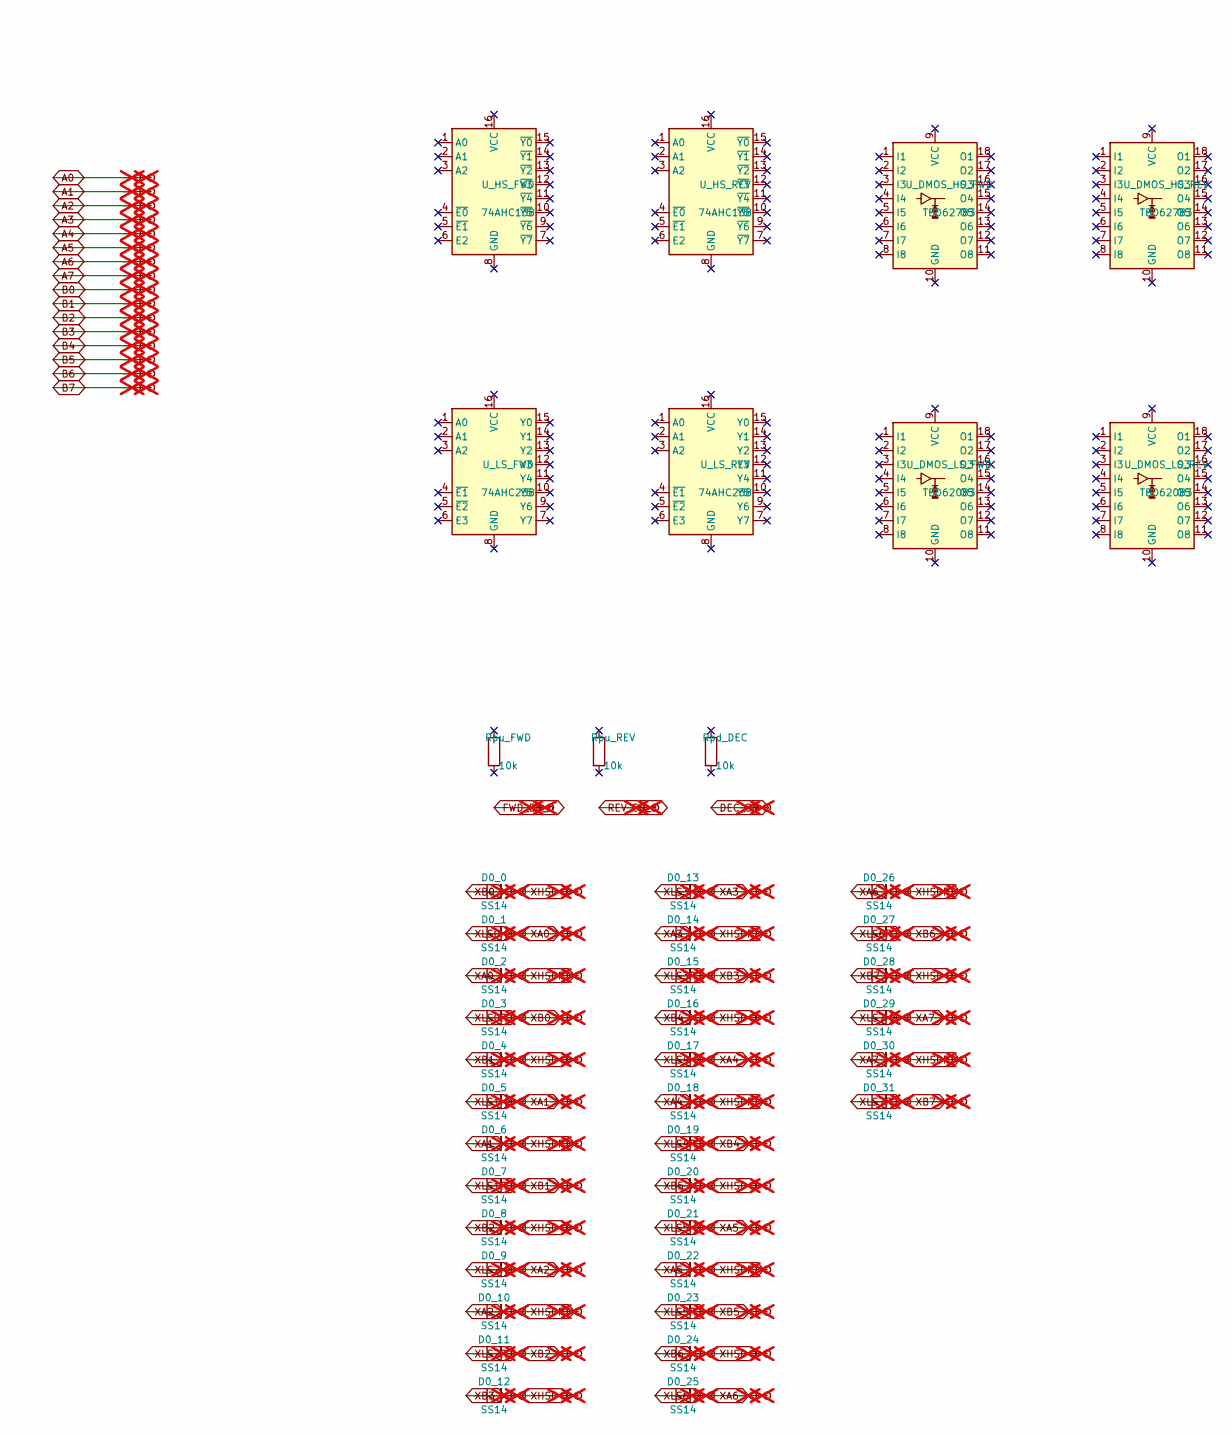
[picture p47: schematic pcb_axis_octal.kicad_sch, part in row 1, column 2]

Parts:
D0_0, D0_1, D0_2, D0_3, D0_4, D0_5, D0_6, D0_7, D0_8, D0_9, D0_10, D0_11, D0_12, D0_13, D0_14, D0_15, D0_16, D0_17, D0_18, D0_19, D0_20, D0_21, D0_22, D0_23, D0_24, D0_25, D0_26, D0_27, D0_28, D0_29, D0_30, D0_31: SS14; D_SMA
Rpd_DEC: 10k; R_0805_2012Metric
Rpu_FWD: 10k; R_0805_2012Metric
Rpu_REV: 10k; R_0805_2012Metric
TP_A0_20_32_81_28, TP_A0_20_32_81_28b, TP_A0_180_34_35_56, TP_A0_180_34_35_56b, TP_A1_20_32_86_36, TP_A1_20_32_86_36b, TP_A1_180_34_38_1, TP_A1_180_34_38_1b, TP_A2_20_32_91_44, TP_A2_20_32_91_44b, TP_A2_180_34_40_64, TP_A2_180_34_40_64b, TP_A3_20_32_96_52, TP_A3_20_32_96_52b, TP_A3_180_34_43_18, TP_A3_180_34_43_18b, TP_A4_20_32_101_6, TP_A4_20_32_101_6b, TP_A4_180_34_45_72, TP_A4_180_34_45_72b, TP_A5_20_32_106_68, TP_A5_20_32_106_68b, TP_A5_180_34_48_26, TP_A5_180_34_48_26b, TP_A6_20_32_111_76, TP_A6_20_32_111_76b, TP_A6_180_34_50_8, TP_A6_180_34_50_8b, TP_A7_20_32_116_84, TP_A7_20_32_116_84b, TP_A7_180_34_53_34, TP_A7_180_34_53_34b: Stub; not fitted
TP_ADDR_NH0_100_33_53_3, TP_ADDR_NH0_100_33_53_3b, TP_ADDR_NH1_100_33_55_8, TP_ADDR_NH1_100_33_55_8b, TP_ADDR_NH2_100_33_58_4, TP_ADDR_NH2_100_33_58_4b: Stub; not fitted
TP_ADDR_NL0_100_33_45_7, TP_ADDR_NL0_100_33_45_7b, TP_ADDR_NL1_100_33_48_2, TP_ADDR_NL1_100_33_48_2b, TP_ADDR_NL2_100_33_50_8, TP_ADDR_NL2_100_33_50_8b: Stub; not fitted
TP_AGND_100_33_38_1, TP_AGND_100_33_38_1b: Stub; not fitted
TP_AGND_PWR_100_33_43_1, TP_AGND_PWR_100_33_43_1b: Stub; not fitted
TP_AXIS_ID0_100_33_71_1, TP_AXIS_ID0_100_33_71_1b, TP_AXIS_ID1_100_33_73_6, TP_AXIS_ID1_100_33_73_6b: Stub; not fitted
TP_B0_20_32_83_82, TP_B0_20_32_83_82b, TP_B0_180_34_55_88, TP_B0_180_34_55_88b, TP_B1_20_32_88_9, TP_B1_20_32_88_9b, TP_B1_180_34_58_42, TP_B1_180_34_58_42b, TP_B2_20_32_93_98, TP_B2_20_32_93_98b, TP_B2_180_34_60_96, TP_B2_180_34_60_96b, TP_B3_20_32_99_06, TP_B3_20_32_99_06b, TP_B3_180_34_63_5, TP_B3_180_34_63_5b, TP_B4_20_32_104_14, TP_B4_20_32_104_14b, TP_B4_180_34_66_04, TP_B4_180_34_66_04b, TP_B5_20_32_109_22, TP_B5_20_32_109_22b, TP_B5_180_34_68_58, TP_B5_180_34_68_58b, TP_B6_20_32_114_3, TP_B6_20_32_114_3b, TP_B6_180_34_71_12, TP_B6_180_34_71_12b, TP_B7_20_32_119_38, TP_B7_20_32_119_38b, TP_B7_180_34_73_66, TP_B7_180_34_73_66b: Stub; not fitted
TP_CCS_RET_AXIS_100_33_, TP_CCS_RET_AXIS_100_33_b: Stub; not fitted
TP_DEC_EN_100_33_66_04, TP_DEC_EN_100_33_66_04b, TP_DEC_EN_299_72_149_, TP_DEC_EN_299_72_149_b: Stub; not fitted
TP_FWD_EN_n_100_33_60_9, TP_FWD_EN_n_100_33_60_9b, TP_FWD_EN_n_260_35_14, TP_FWD_EN_n_260_35_14b: Stub; not fitted
TP_HSR_20_32_38_1, TP_HSR_20_32_38_1b: Stub; not fitted
TP_HS_20_32_35_56, TP_HS_20_32_35_56b: Stub; not fitted
TP_LS0_20_32_40_64, TP_LS0_20_32_40_64b, TP_LS1_20_32_43_18, TP_LS1_20_32_43_18b, TP_LS2_20_32_45_72, TP_LS2_20_32_45_72b, TP_LS3_20_32_48_26, TP_LS3_20_32_48_26b, TP_LS4_20_32_50_8, TP_LS4_20_32_50_8b, TP_LS5_20_32_53_34, TP_LS5_20_32_53_34b, TP_LS6_20_32_55_88, TP_LS6_20_32_55_88b, TP_LS7_20_32_58_42, TP_LS7_20_32_58_42b: Stub; not fitted
TP_LSR0_20_32_60_96, TP_LSR0_20_32_60_96b, TP_LSR1_20_32_63_5, TP_LSR1_20_32_63_5b, TP_LSR2_20_32_66_04, TP_LSR2_20_32_66_04b, TP_LSR3_20_32_68_58, TP_LSR3_20_32_68_58b, TP_LSR4_20_32_71_12, TP_LSR4_20_32_71_12b, TP_LSR5_20_32_73_66, TP_LSR5_20_32_73_66b, TP_LSR6_20_32_76_2, TP_LSR6_20_32_76_2b, TP_LSR7_20_32_78_74, TP_LSR7_20_32_78_74b: Stub; not fitted
TP_REV_EN_n_100_33_63_5, TP_REV_EN_n_100_33_63_5b, TP_REV_EN_n_279_4_149, TP_REV_EN_n_279_4_149b: Stub; not fitted
TP_VDRIVE_100_33_40_64, TP_VDRIVE_100_33_40_64b: Stub; not fitted
TP_XA0_255_27_180_34, TP_XA0_255_27_180_34b, TP_XA0_265_43_172_72, TP_XA0_265_43_172_72b, TP_XA1_255_27_210_82, TP_XA1_255_27_210_82b, TP_XA1_265_43_203_2, TP_XA1_265_43_203_2b, TP_XA2_255_27_241_3, TP_XA2_255_27_241_3b, TP_XA2_265_43_233_68, TP_XA2_265_43_233_68b, TP_XA3_289_56_172_72, TP_XA3_289_56_172_72b, TP_XA3_299_72_165_1, TP_XA3_299_72_165_1b, TP_XA4_289_56_203_2, TP_XA4_289_56_203_2b, TP_XA4_299_72_195_58, TP_XA4_299_72_195_58b, TP_XA5_289_56_233_68, TP_XA5_289_56_233_68b, TP_XA5_299_72_226_06, TP_XA5_299_72_226_06b, TP_XA6_299_72_256_54, TP_XA6_299_72_256_54b, TP_XA6_325_12_165_1, TP_XA6_325_12_165_1b, TP_XA7_325_12_195_58, TP_XA7_325_12_195_58b, TP_XA7_335_28_187_96, TP_XA7_335_28_187_96b: Stub; not fitted
TP_XB0_255_27_165_1, TP_XB0_255_27_165_1b, TP_XB0_265_43_187_96, TP_XB0_265_43_187_96b, TP_XB1_255_27_195_58, TP_XB1_255_27_195_58b, TP_XB1_265_43_218_44, TP_XB1_265_43_218_44b, TP_XB2_255_27_226_06, TP_XB2_255_27_226_06b, TP_XB2_265_43_248_92, TP_XB2_265_43_248_92b, TP_XB3_255_27_256_54, TP_XB3_255_27_256_54b, TP_XB3_299_72_180_34, TP_XB3_299_72_180_34b, TP_XB4_289_56_187_96, TP_XB4_289_56_187_96b, TP_XB4_299_72_210_82, TP_XB4_299_72_210_82b, TP_XB5_289_56_218_44, TP_XB5_289_56_218_44b, TP_XB5_299_72_241_3, TP_XB5_299_72_241_3b, TP_XB6_289_56_248_92, TP_XB6_289_56_248_92b, TP_XB6_335_28_172_72, TP_XB6_335_28_172_72b, TP_XB7_325_12_180_34, TP_XB7_325_12_180_34b, TP_XB7_335_28_203_2, TP_XB7_335_28_203_2b: Stub; not fitted
TP_XHS0R_265_43_180_3, TP_XHS0R_265_43_180_3b, TP_XHS0R_265_43_210_8, TP_XHS0R_265_43_210_8b, TP_XHS0R_265_43_241_3, TP_XHS0R_265_43_241_3b, TP_XHS0R_299_72_172_7, TP_XHS0R_299_72_172_7b, TP_XHS0R_299_72_203_2, TP_XHS0R_299_72_203_2b, TP_XHS0R_299_72_233_6, TP_XHS0R_299_72_233_6b, TP_XHS0R_335_28_165_1, TP_XHS0R_335_28_165_1b, TP_XHS0R_335_28_195_5, TP_XHS0R_335_28_195_5b, TP_XHS0_265_43_165_1, TP_XHS0_265_43_165_1b, TP_XHS0_265_43_195_58, TP_XHS0_265_43_195_58b, TP_XHS0_265_43_226_06, TP_XHS0_265_43_226_06b, TP_XHS0_265_43_256_54, TP_XHS0_265_43_256_54b, TP_XHS0_299_72_187_96, TP_XHS0_299_72_187_96b, TP_XHS0_299_72_218_44, TP_XHS0_299_72_218_44b, TP_XHS0_299_72_248_92, TP_XHS0_299_72_248_92b, TP_XHS0_335_28_180_34, TP_XHS0_335_28_180_34b: Stub; not fitted
TP_XLS0R_255_27_187_9, TP_XLS0R_255_27_187_9b, TP_XLS0_255_27_172_72, TP_XLS0_255_27_172_72b, TP_XLS1R_255_27_218_4, TP_XLS1R_255_27_218_4b, TP_XLS1_255_27_203_2, TP_XLS1_255_27_203_2b, TP_XLS2R_255_27_248_9, TP_XLS2R_255_27_248_9b, TP_XLS2_255_27_233_68, TP_XLS2_255_27_233_68b, TP_XLS3R_289_56_180_3, TP_XLS3R_289_56_180_3b, TP_XLS3_289_56_165_1, TP_XLS3_289_56_165_1b, TP_XLS4R_289_56_210_8, TP_XLS4R_289_56_210_8b, TP_XLS4_289_56_195_58, TP_XLS4_289_56_195_58b, TP_XLS5R_289_56_241_3, TP_XLS5R_289_56_241_3b, TP_XLS5_289_56_226_06, TP_XLS5_289_56_226_06b, TP_XLS6R_325_12_172_7, TP_XLS6R_325_12_172_7b, TP_XLS6_289_56_256_54, TP_XLS6_289_56_256_54b, TP_XLS7R_325_12_203_2, TP_XLS7R_325_12_203_2b, TP_XLS7_325_12_187_96, TP_XLS7_325_12_187_96b: Stub; not fitted
TP__3V3_100_33_35_56, TP__3V3_100_33_35_56b: Stub; not fitted
U_DMOS_HS_FWD: TBD62783; SOIC-18W_7.5x11.6mm_P1.27mm
U_DMOS_HS_REV: TBD62783; SOIC-18W_7.5x11.6mm_P1.27mm
U_DMOS_LS_FWD: TBD62083; SOIC-18W_7.5x11.6mm_P1.27mm
U_DMOS_LS_REV: TBD62083; SOIC-18W_7.5x11.6mm_P1.27mm
U_HS_FWD: 74AHC138; SOIC-16_3.9x9.9mm_P1.27mm
U_HS_REV: 74AHC138; SOIC-16_3.9x9.9mm_P1.27mm
U_LS_FWD: 74AHC238; SOIC-16_3.9x9.9mm_P1.27mm
U_LS_REV: 74AHC238; SOIC-16_3.9x9.9mm_P1.27mm

Connections:
+3V3: TP__3V3_100_33_35_56.1, TP__3V3_100_33_35_56b.1
A0: TP_A0_20_32_81_28.1, TP_A0_20_32_81_28b.1, TP_A0_180_34_35_56.1, TP_A0_180_34_35_56b.1
A1: TP_A1_20_32_86_36.1, TP_A1_20_32_86_36b.1, TP_A1_180_34_38_1.1, TP_A1_180_34_38_1b.1
A2: TP_A2_20_32_91_44.1, TP_A2_20_32_91_44b.1, TP_A2_180_34_40_64.1, TP_A2_180_34_40_64b.1
A3: TP_A3_20_32_96_52.1, TP_A3_20_32_96_52b.1, TP_A3_180_34_43_18.1, TP_A3_180_34_43_18b.1
A4: TP_A4_20_32_101_6.1, TP_A4_20_32_101_6b.1, TP_A4_180_34_45_72.1, TP_A4_180_34_45_72b.1
A5: TP_A5_20_32_106_68.1, TP_A5_20_32_106_68b.1, TP_A5_180_34_48_26.1, TP_A5_180_34_48_26b.1
A6: TP_A6_20_32_111_76.1, TP_A6_20_32_111_76b.1, TP_A6_180_34_50_8.1, TP_A6_180_34_50_8b.1
A7: TP_A7_20_32_116_84.1, TP_A7_20_32_116_84b.1, TP_A7_180_34_53_34.1, TP_A7_180_34_53_34b.1
ADDR_NH0: TP_ADDR_NH0_100_33_53_3.1, TP_ADDR_NH0_100_33_53_3b.1
ADDR_NH1: TP_ADDR_NH1_100_33_55_8.1, TP_ADDR_NH1_100_33_55_8b.1
ADDR_NH2: TP_ADDR_NH2_100_33_58_4.1, TP_ADDR_NH2_100_33_58_4b.1
ADDR_NL0: TP_ADDR_NL0_100_33_45_7.1, TP_ADDR_NL0_100_33_45_7b.1
ADDR_NL1: TP_ADDR_NL1_100_33_48_2.1, TP_ADDR_NL1_100_33_48_2b.1
ADDR_NL2: TP_ADDR_NL2_100_33_50_8.1, TP_ADDR_NL2_100_33_50_8b.1
AGND: TP_AGND_100_33_38_1.1, TP_AGND_100_33_38_1b.1
AGND_PWR: TP_AGND_PWR_100_33_43_1.1, TP_AGND_PWR_100_33_43_1b.1
AXIS_ID0: TP_AXIS_ID0_100_33_71_1.1, TP_AXIS_ID0_100_33_71_1b.1
AXIS_ID1: TP_AXIS_ID1_100_33_73_6.1, TP_AXIS_ID1_100_33_73_6b.1
B0: TP_B0_20_32_83_82.1, TP_B0_20_32_83_82b.1, TP_B0_180_34_55_88.1, TP_B0_180_34_55_88b.1
B1: TP_B1_20_32_88_9.1, TP_B1_20_32_88_9b.1, TP_B1_180_34_58_42.1, TP_B1_180_34_58_42b.1
B2: TP_B2_20_32_93_98.1, TP_B2_20_32_93_98b.1, TP_B2_180_34_60_96.1, TP_B2_180_34_60_96b.1
B3: TP_B3_20_32_99_06.1, TP_B3_20_32_99_06b.1, TP_B3_180_34_63_5.1, TP_B3_180_34_63_5b.1
B4: TP_B4_20_32_104_14.1, TP_B4_20_32_104_14b.1, TP_B4_180_34_66_04.1, TP_B4_180_34_66_04b.1
B5: TP_B5_20_32_109_22.1, TP_B5_20_32_109_22b.1, TP_B5_180_34_68_58.1, TP_B5_180_34_68_58b.1
B6: TP_B6_20_32_114_3.1, TP_B6_20_32_114_3b.1, TP_B6_180_34_71_12.1, TP_B6_180_34_71_12b.1
B7: TP_B7_20_32_119_38.1, TP_B7_20_32_119_38b.1, TP_B7_180_34_73_66.1, TP_B7_180_34_73_66b.1
CCS_RET_AXIS: TP_CCS_RET_AXIS_100_33_.1, TP_CCS_RET_AXIS_100_33_b.1
DEC_EN: TP_DEC_EN_100_33_66_04.1, TP_DEC_EN_100_33_66_04b.1, TP_DEC_EN_299_72_149_.1, TP_DEC_EN_299_72_149_b.1
FWD_EN_n: TP_FWD_EN_n_100_33_60_9.1, TP_FWD_EN_n_100_33_60_9b.1, TP_FWD_EN_n_260_35_14.1, TP_FWD_EN_n_260_35_14b.1
HS: TP_HS_20_32_35_56.1, TP_HS_20_32_35_56b.1
HSR: TP_HSR_20_32_38_1.1, TP_HSR_20_32_38_1b.1
LS0: TP_LS0_20_32_40_64.1, TP_LS0_20_32_40_64b.1
LS1: TP_LS1_20_32_43_18.1, TP_LS1_20_32_43_18b.1
LS2: TP_LS2_20_32_45_72.1, TP_LS2_20_32_45_72b.1
LS3: TP_LS3_20_32_48_26.1, TP_LS3_20_32_48_26b.1
LS4: TP_LS4_20_32_50_8.1, TP_LS4_20_32_50_8b.1
LS5: TP_LS5_20_32_53_34.1, TP_LS5_20_32_53_34b.1
LS6: TP_LS6_20_32_55_88.1, TP_LS6_20_32_55_88b.1
LS7: TP_LS7_20_32_58_42.1, TP_LS7_20_32_58_42b.1
LSR0: TP_LSR0_20_32_60_96.1, TP_LSR0_20_32_60_96b.1
LSR1: TP_LSR1_20_32_63_5.1, TP_LSR1_20_32_63_5b.1
LSR2: TP_LSR2_20_32_66_04.1, TP_LSR2_20_32_66_04b.1
LSR3: TP_LSR3_20_32_68_58.1, TP_LSR3_20_32_68_58b.1
LSR4: TP_LSR4_20_32_71_12.1, TP_LSR4_20_32_71_12b.1
LSR5: TP_LSR5_20_32_73_66.1, TP_LSR5_20_32_73_66b.1
LSR6: TP_LSR6_20_32_76_2.1, TP_LSR6_20_32_76_2b.1
LSR7: TP_LSR7_20_32_78_74.1, TP_LSR7_20_32_78_74b.1
REV_EN_n: TP_REV_EN_n_100_33_63_5.1, TP_REV_EN_n_100_33_63_5b.1, TP_REV_EN_n_279_4_149.1, TP_REV_EN_n_279_4_149b.1
VDRIVE: TP_VDRIVE_100_33_40_64.1, TP_VDRIVE_100_33_40_64b.1
XA0: D0_1.2 (A), D0_2.1 (K), TP_XA0_255_27_180_34.1, TP_XA0_255_27_180_34b.1, TP_XA0_265_43_172_72.1, TP_XA0_265_43_172_72b.1
XA1: D0_5.2 (A), D0_6.1 (K), TP_XA1_255_27_210_82.1, TP_XA1_255_27_210_82b.1, TP_XA1_265_43_203_2.1, TP_XA1_265_43_203_2b.1
XA2: D0_9.2 (A), D0_10.1 (K), TP_XA2_255_27_241_3.1, TP_XA2_255_27_241_3b.1, TP_XA2_265_43_233_68.1, TP_XA2_265_43_233_68b.1
XA3: D0_13.2 (A), D0_14.1 (K), TP_XA3_289_56_172_72.1, TP_XA3_289_56_172_72b.1, TP_XA3_299_72_165_1.1, TP_XA3_299_72_165_1b.1
XA4: D0_17.2 (A), D0_18.1 (K), TP_XA4_289_56_203_2.1, TP_XA4_289_56_203_2b.1, TP_XA4_299_72_195_58.1, TP_XA4_299_72_195_58b.1
XA5: D0_21.2 (A), D0_22.1 (K), TP_XA5_289_56_233_68.1, TP_XA5_289_56_233_68b.1, TP_XA5_299_72_226_06.1, TP_XA5_299_72_226_06b.1
XA6: D0_25.2 (A), D0_26.1 (K), TP_XA6_299_72_256_54.1, TP_XA6_299_72_256_54b.1, TP_XA6_325_12_165_1.1, TP_XA6_325_12_165_1b.1
XA7: D0_29.2 (A), D0_30.1 (K), TP_XA7_325_12_195_58.1, TP_XA7_325_12_195_58b.1, TP_XA7_335_28_187_96.1, TP_XA7_335_28_187_96b.1
XB0: D0_0.1 (K), D0_3.2 (A), TP_XB0_255_27_165_1.1, TP_XB0_255_27_165_1b.1, TP_XB0_265_43_187_96.1, TP_XB0_265_43_187_96b.1
XB1: D0_4.1 (K), D0_7.2 (A), TP_XB1_255_27_195_58.1, TP_XB1_255_27_195_58b.1, TP_XB1_265_43_218_44.1, TP_XB1_265_43_218_44b.1
XB2: D0_8.1 (K), D0_11.2 (A), TP_XB2_255_27_226_06.1, TP_XB2_255_27_226_06b.1, TP_XB2_265_43_248_92.1, TP_XB2_265_43_248_92b.1
XB3: D0_12.1 (K), D0_15.2 (A), TP_XB3_255_27_256_54.1, TP_XB3_255_27_256_54b.1, TP_XB3_299_72_180_34.1, TP_XB3_299_72_180_34b.1
XB4: D0_16.1 (K), D0_19.2 (A), TP_XB4_289_56_187_96.1, TP_XB4_289_56_187_96b.1, TP_XB4_299_72_210_82.1, TP_XB4_299_72_210_82b.1
XB5: D0_20.1 (K), D0_23.2 (A), TP_XB5_289_56_218_44.1, TP_XB5_289_56_218_44b.1, TP_XB5_299_72_241_3.1, TP_XB5_299_72_241_3b.1
XB6: D0_24.1 (K), D0_27.2 (A), TP_XB6_289_56_248_92.1, TP_XB6_289_56_248_92b.1, TP_XB6_335_28_172_72.1, TP_XB6_335_28_172_72b.1
XB7: D0_28.1 (K), D0_31.2 (A), TP_XB7_325_12_180_34.1, TP_XB7_325_12_180_34b.1, TP_XB7_335_28_203_2.1, TP_XB7_335_28_203_2b.1
XHS0: D0_0.2 (A), D0_4.2 (A), D0_8.2 (A), D0_12.2 (A), D0_16.2 (A), D0_20.2 (A), D0_24.2 (A), D0_28.2 (A), TP_XHS0_265_43_165_1.1, TP_XHS0_265_43_165_1b.1, TP_XHS0_265_43_195_58.1, TP_XHS0_265_43_195_58b.1, TP_XHS0_265_43_226_06.1, TP_XHS0_265_43_226_06b.1, TP_XHS0_265_43_256_54.1, TP_XHS0_265_43_256_54b.1, TP_XHS0_299_72_187_96.1, TP_XHS0_299_72_187_96b.1, TP_XHS0_299_72_218_44.1, TP_XHS0_299_72_218_44b.1, TP_XHS0_299_72_248_92.1, TP_XHS0_299_72_248_92b.1, TP_XHS0_335_28_180_34.1, TP_XHS0_335_28_180_34b.1
XHS0R: D0_2.2 (A), D0_6.2 (A), D0_10.2 (A), D0_14.2 (A), D0_18.2 (A), D0_22.2 (A), D0_26.2 (A), D0_30.2 (A), TP_XHS0R_265_43_180_3.1, TP_XHS0R_265_43_180_3b.1, TP_XHS0R_265_43_210_8.1, TP_XHS0R_265_43_210_8b.1, TP_XHS0R_265_43_241_3.1, TP_XHS0R_265_43_241_3b.1, TP_XHS0R_299_72_172_7.1, TP_XHS0R_299_72_172_7b.1, TP_XHS0R_299_72_203_2.1, TP_XHS0R_299_72_203_2b.1, TP_XHS0R_299_72_233_6.1, TP_XHS0R_299_72_233_6b.1, TP_XHS0R_335_28_165_1.1, TP_XHS0R_335_28_165_1b.1, TP_XHS0R_335_28_195_5.1, TP_XHS0R_335_28_195_5b.1
XLS0: D0_1.1 (K), TP_XLS0_255_27_172_72.1, TP_XLS0_255_27_172_72b.1
XLS0R: D0_3.1 (K), TP_XLS0R_255_27_187_9.1, TP_XLS0R_255_27_187_9b.1
XLS1: D0_5.1 (K), TP_XLS1_255_27_203_2.1, TP_XLS1_255_27_203_2b.1
XLS1R: D0_7.1 (K), TP_XLS1R_255_27_218_4.1, TP_XLS1R_255_27_218_4b.1
XLS2: D0_9.1 (K), TP_XLS2_255_27_233_68.1, TP_XLS2_255_27_233_68b.1
XLS2R: D0_11.1 (K), TP_XLS2R_255_27_248_9.1, TP_XLS2R_255_27_248_9b.1
XLS3: D0_13.1 (K), TP_XLS3_289_56_165_1.1, TP_XLS3_289_56_165_1b.1
XLS3R: D0_15.1 (K), TP_XLS3R_289_56_180_3.1, TP_XLS3R_289_56_180_3b.1
XLS4: D0_17.1 (K), TP_XLS4_289_56_195_58.1, TP_XLS4_289_56_195_58b.1
XLS4R: D0_19.1 (K), TP_XLS4R_289_56_210_8.1, TP_XLS4R_289_56_210_8b.1
XLS5: D0_21.1 (K), TP_XLS5_289_56_226_06.1, TP_XLS5_289_56_226_06b.1
XLS5R: D0_23.1 (K), TP_XLS5R_289_56_241_3.1, TP_XLS5R_289_56_241_3b.1
XLS6: D0_25.1 (K), TP_XLS6_289_56_256_54.1, TP_XLS6_289_56_256_54b.1
XLS6R: D0_27.1 (K), TP_XLS6R_325_12_172_7.1, TP_XLS6R_325_12_172_7b.1
XLS7: D0_29.1 (K), TP_XLS7_325_12_187_96.1, TP_XLS7_325_12_187_96b.1
XLS7R: D0_31.1 (K), TP_XLS7R_325_12_203_2.1, TP_XLS7R_325_12_203_2b.1

Notes on the sheet:
GENERATED by generators/ — do not hand-edit; uv run python -m generators.cli --board axis
Decode 74AHC138+74AHC238; DMOS TBD62783/TBD62083; steer SS14
REQ-HIER-OCTAL steer pins=34 lines=[0, 1, 2, 3, 4, 5, 6, 7]
JP_AXIS=X|Y JP_G[2:0]=group bring-up: g=0
