fractalclockwork/core-memory-redux/kicad/pcb_ccs_sense/pcb_ccs_sense.kicad_sch

## KiCad design kicad/pcb_ccs_sense/pcb_ccs_sense.kicad_sch (2026-10-05)

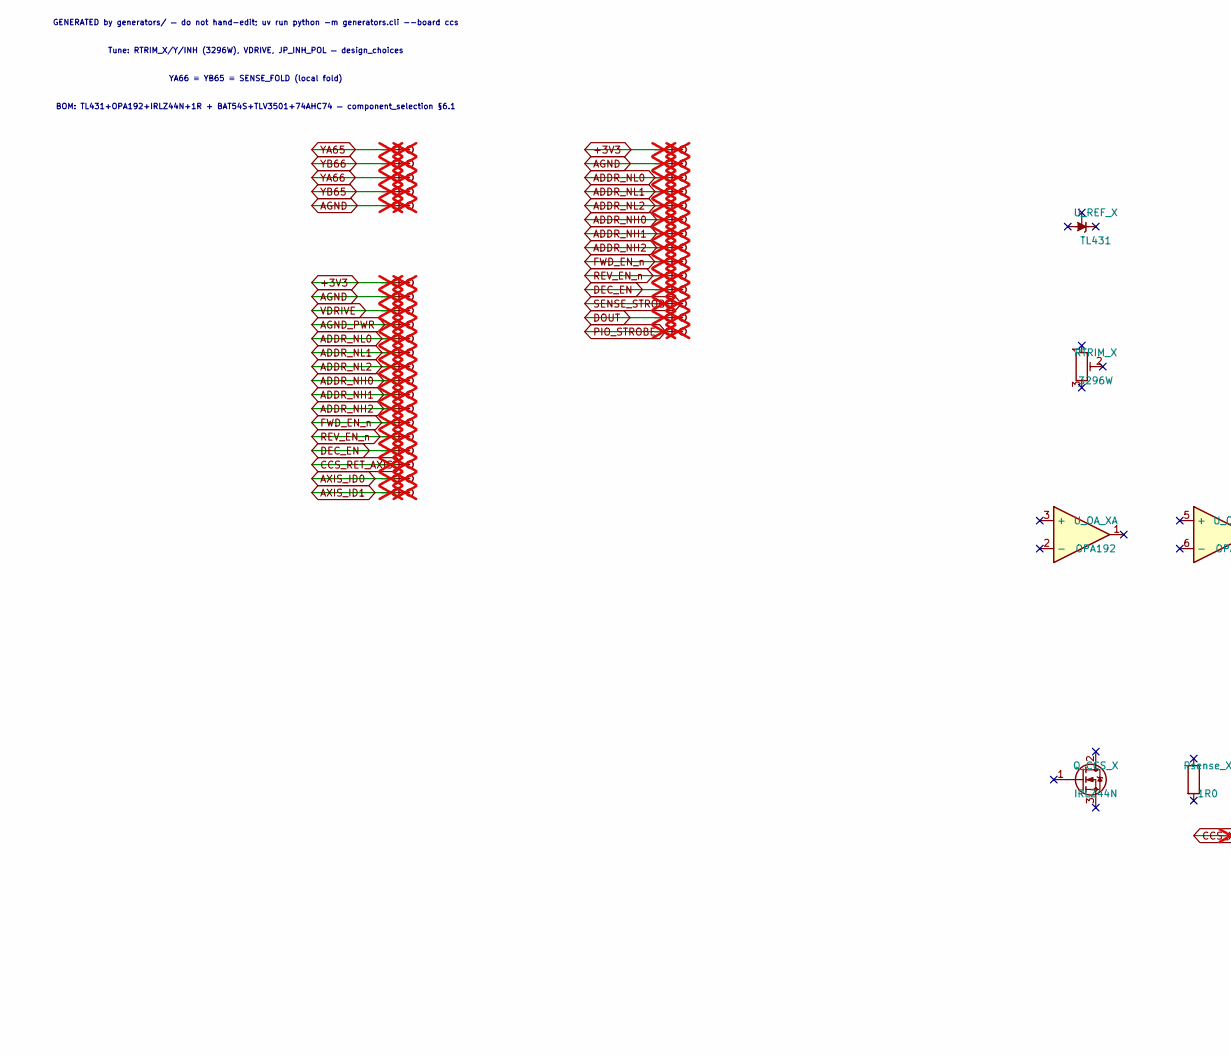
[picture p48: schematic pcb_ccs_sense.kicad_sch, part in row 1, column 1]

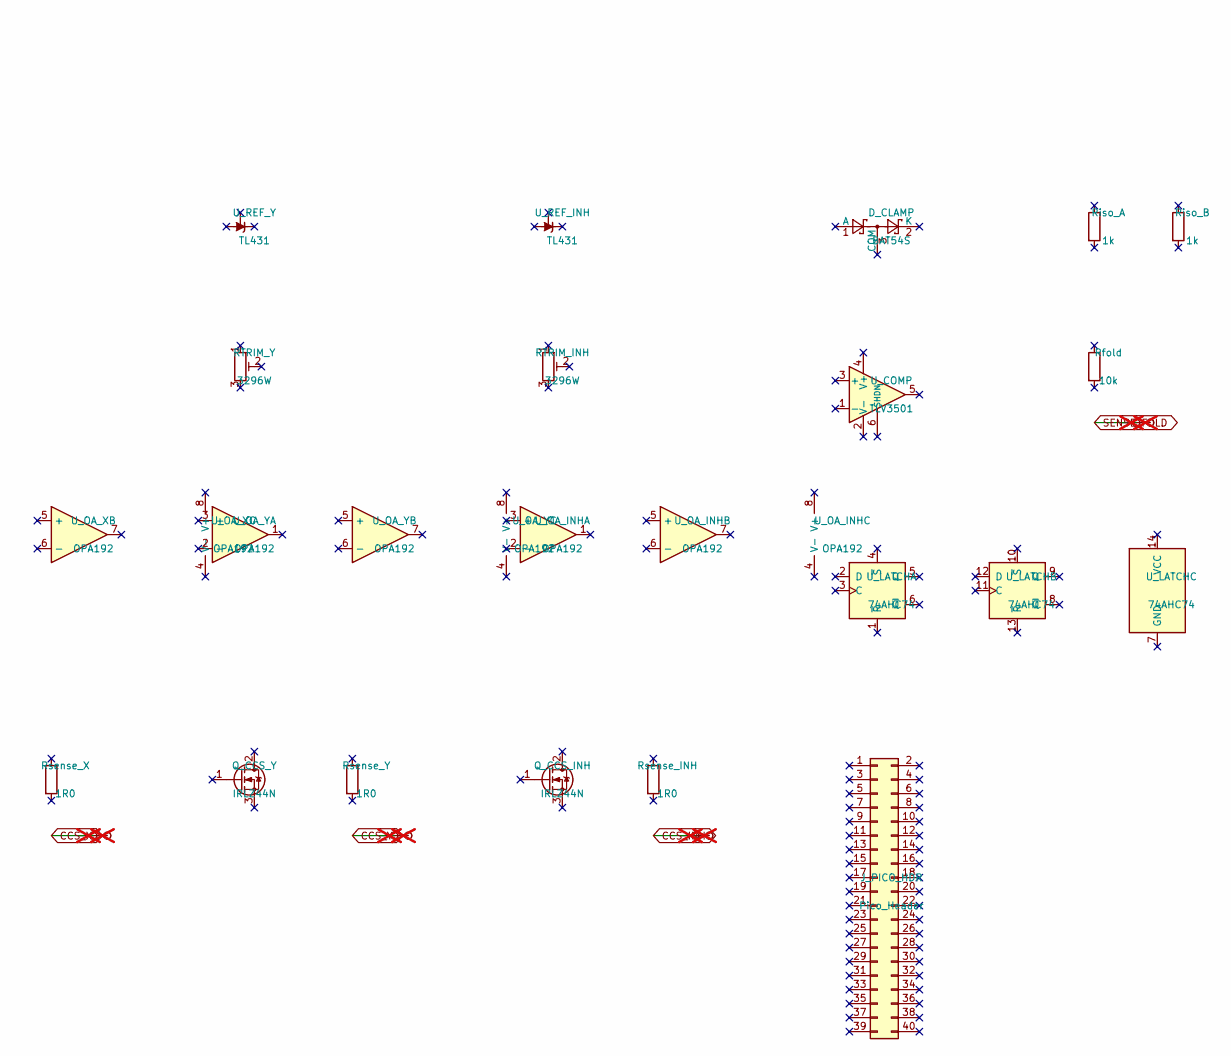
[picture p49: schematic pcb_ccs_sense.kicad_sch, part in row 1, column 2]

Parts:
D_CLAMP: BAT54S; SOT-23
J_PICO_HDR: Pico_Header; PinHeader_2x20_P2.54mm_Vertical
Q_CCS_INH: IRLZ44N; TO-220-3_Vertical
Q_CCS_X: IRLZ44N; TO-220-3_Vertical
Q_CCS_Y: IRLZ44N; TO-220-3_Vertical
RTRIM_INH: 3296W; Potentiometer_Bourns_3296W_Vertical
RTRIM_X: 3296W; Potentiometer_Bourns_3296W_Vertical
RTRIM_Y: 3296W; Potentiometer_Bourns_3296W_Vertical
Rfold: 10k; R_0805_2012Metric
Riso_A: 1k; R_0805_2012Metric
Riso_B: 1k; R_0805_2012Metric
Rsense_INH: 1R0; R_2512_6332Metric
Rsense_X: 1R0; R_2512_6332Metric
Rsense_Y: 1R0; R_2512_6332Metric
TP_ADDR_NH0_20_32_72_39, TP_ADDR_NH0_20_32_72_39b, TP_ADDR_NH0_69_85_43_18, TP_ADDR_NH0_69_85_43_18b, TP_ADDR_NH1_20_32_74_93, TP_ADDR_NH1_20_32_74_93b, TP_ADDR_NH1_69_85_45_72, TP_ADDR_NH1_69_85_45_72b, TP_ADDR_NH2_20_32_77_47, TP_ADDR_NH2_20_32_77_47b, TP_ADDR_NH2_69_85_48_26, TP_ADDR_NH2_69_85_48_26b: Stub; not fitted
TP_ADDR_NL0_20_32_64_77, TP_ADDR_NL0_20_32_64_77b, TP_ADDR_NL0_69_85_35_56, TP_ADDR_NL0_69_85_35_56b, TP_ADDR_NL1_20_32_67_31, TP_ADDR_NL1_20_32_67_31b, TP_ADDR_NL1_69_85_38_1, TP_ADDR_NL1_69_85_38_1b, TP_ADDR_NL2_20_32_69_85, TP_ADDR_NL2_20_32_69_85b, TP_ADDR_NL2_69_85_40_64, TP_ADDR_NL2_69_85_40_64b: Stub; not fitted
TP_AGND_20_32_40_64, TP_AGND_20_32_40_64b, TP_AGND_20_32_57_15, TP_AGND_20_32_57_15b, TP_AGND_69_85_33_02, TP_AGND_69_85_33_02b: Stub; not fitted
TP_AGND_PWR_20_32_62_23, TP_AGND_PWR_20_32_62_23b: Stub; not fitted
TP_AXIS_ID0_20_32_90_17, TP_AXIS_ID0_20_32_90_17b, TP_AXIS_ID1_20_32_92_71, TP_AXIS_ID1_20_32_92_71b: Stub; not fitted
TP_CCS_INH_289_56_154, TP_CCS_INH_289_56_154b: Stub; not fitted
TP_CCS_RET_AXIS_20_32_8, TP_CCS_RET_AXIS_20_32_8b: Stub; not fitted
TP_CCS_X_180_34_154_9, TP_CCS_X_180_34_154_9b: Stub; not fitted
TP_CCS_Y_234_95_154_9, TP_CCS_Y_234_95_154_9b: Stub; not fitted
TP_DEC_EN_20_32_85_09, TP_DEC_EN_20_32_85_09b, TP_DEC_EN_69_85_55_88, TP_DEC_EN_69_85_55_88b: Stub; not fitted
TP_DOUT_69_85_60_96, TP_DOUT_69_85_60_96b: Stub; not fitted
TP_FWD_EN_n_20_32_80_01, TP_FWD_EN_n_20_32_80_01b, TP_FWD_EN_n_69_85_50_8, TP_FWD_EN_n_69_85_50_8b: Stub; not fitted
TP_PIO_STROBE_69_85_63_, TP_PIO_STROBE_69_85_63_b: Stub; not fitted
TP_REV_EN_n_20_32_82_55, TP_REV_EN_n_20_32_82_55b, TP_REV_EN_n_69_85_53_34, TP_REV_EN_n_69_85_53_34b: Stub; not fitted
TP_SENSE_FOLD_369_57_, TP_SENSE_FOLD_369_57_b: Stub; not fitted
TP_SENSE_STROBE_69_85_5, TP_SENSE_STROBE_69_85_5b: Stub; not fitted
TP_VDRIVE_20_32_59_69, TP_VDRIVE_20_32_59_69b: Stub; not fitted
TP_YA65_20_32_30_48, TP_YA65_20_32_30_48b, TP_YA66_20_32_35_56, TP_YA66_20_32_35_56b: Stub; not fitted
TP_YB65_20_32_38_1, TP_YB65_20_32_38_1b, TP_YB66_20_32_33_02, TP_YB66_20_32_33_02b: Stub; not fitted
TP__3V3_20_32_54_61, TP__3V3_20_32_54_61b, TP__3V3_69_85_30_48, TP__3V3_69_85_30_48b: Stub; not fitted
U_COMP: TLV3501; SOT-23-6
U_LATCH: 74AHC74; SOIC-14_3.9x8.7mm_P1.27mm
U_OA_INH: OPA192; SOIC-8_3.9x4.9mm_P1.27mm
U_OA_X: OPA192; SOIC-8_3.9x4.9mm_P1.27mm
U_OA_Y: OPA192; SOIC-8_3.9x4.9mm_P1.27mm
U_REF_INH: TL431; SOT-23
U_REF_X: TL431; SOT-23
U_REF_Y: TL431; SOT-23

Connections:
+3V3: TP__3V3_20_32_54_61.1, TP__3V3_20_32_54_61b.1, TP__3V3_69_85_30_48.1, TP__3V3_69_85_30_48b.1
ADDR_NH0: TP_ADDR_NH0_20_32_72_39.1, TP_ADDR_NH0_20_32_72_39b.1, TP_ADDR_NH0_69_85_43_18.1, TP_ADDR_NH0_69_85_43_18b.1
ADDR_NH1: TP_ADDR_NH1_20_32_74_93.1, TP_ADDR_NH1_20_32_74_93b.1, TP_ADDR_NH1_69_85_45_72.1, TP_ADDR_NH1_69_85_45_72b.1
ADDR_NH2: TP_ADDR_NH2_20_32_77_47.1, TP_ADDR_NH2_20_32_77_47b.1, TP_ADDR_NH2_69_85_48_26.1, TP_ADDR_NH2_69_85_48_26b.1
ADDR_NL0: TP_ADDR_NL0_20_32_64_77.1, TP_ADDR_NL0_20_32_64_77b.1, TP_ADDR_NL0_69_85_35_56.1, TP_ADDR_NL0_69_85_35_56b.1
ADDR_NL1: TP_ADDR_NL1_20_32_67_31.1, TP_ADDR_NL1_20_32_67_31b.1, TP_ADDR_NL1_69_85_38_1.1, TP_ADDR_NL1_69_85_38_1b.1
ADDR_NL2: TP_ADDR_NL2_20_32_69_85.1, TP_ADDR_NL2_20_32_69_85b.1, TP_ADDR_NL2_69_85_40_64.1, TP_ADDR_NL2_69_85_40_64b.1
AGND: TP_AGND_20_32_40_64.1, TP_AGND_20_32_40_64b.1, TP_AGND_20_32_57_15.1, TP_AGND_20_32_57_15b.1, TP_AGND_69_85_33_02.1, TP_AGND_69_85_33_02b.1
AGND_PWR: TP_AGND_PWR_20_32_62_23.1, TP_AGND_PWR_20_32_62_23b.1
AXIS_ID0: TP_AXIS_ID0_20_32_90_17.1, TP_AXIS_ID0_20_32_90_17b.1
AXIS_ID1: TP_AXIS_ID1_20_32_92_71.1, TP_AXIS_ID1_20_32_92_71b.1
CCS_INH: TP_CCS_INH_289_56_154.1, TP_CCS_INH_289_56_154b.1
CCS_RET_AXIS: TP_CCS_RET_AXIS_20_32_8.1, TP_CCS_RET_AXIS_20_32_8b.1
CCS_X: TP_CCS_X_180_34_154_9.1, TP_CCS_X_180_34_154_9b.1
CCS_Y: TP_CCS_Y_234_95_154_9.1, TP_CCS_Y_234_95_154_9b.1
DEC_EN: TP_DEC_EN_20_32_85_09.1, TP_DEC_EN_20_32_85_09b.1, TP_DEC_EN_69_85_55_88.1, TP_DEC_EN_69_85_55_88b.1
DOUT: TP_DOUT_69_85_60_96.1, TP_DOUT_69_85_60_96b.1
FWD_EN_n: TP_FWD_EN_n_20_32_80_01.1, TP_FWD_EN_n_20_32_80_01b.1, TP_FWD_EN_n_69_85_50_8.1, TP_FWD_EN_n_69_85_50_8b.1
PIO_STROBE: TP_PIO_STROBE_69_85_63_.1, TP_PIO_STROBE_69_85_63_b.1
REV_EN_n: TP_REV_EN_n_20_32_82_55.1, TP_REV_EN_n_20_32_82_55b.1, TP_REV_EN_n_69_85_53_34.1, TP_REV_EN_n_69_85_53_34b.1
SENSE_FOLD: TP_SENSE_FOLD_369_57_.1, TP_SENSE_FOLD_369_57_b.1
SENSE_STROBE: TP_SENSE_STROBE_69_85_5.1, TP_SENSE_STROBE_69_85_5b.1
VDRIVE: TP_VDRIVE_20_32_59_69.1, TP_VDRIVE_20_32_59_69b.1
YA65: TP_YA65_20_32_30_48.1, TP_YA65_20_32_30_48b.1
YA66: TP_YA66_20_32_35_56.1, TP_YA66_20_32_35_56b.1
YB65: TP_YB65_20_32_38_1.1, TP_YB65_20_32_38_1b.1
YB66: TP_YB66_20_32_33_02.1, TP_YB66_20_32_33_02b.1

Notes on the sheet:
Tune: RTRIM_X/Y/INH (3296W), VDRIVE, JP_INH_POL — design_choices
GENERATED by generators/ — do not hand-edit; uv run python -m generators.cli --board ccs
BOM: TL431+OPA192+IRLZ44N+1R + BAT54S+TLV3501+74AHC74 — component_selection §6.1
YA66 ≡ YB65 ≡ SENSE_FOLD (local fold)
